kgroveshok/z80-homebrew/images/20220320_144750.jpg

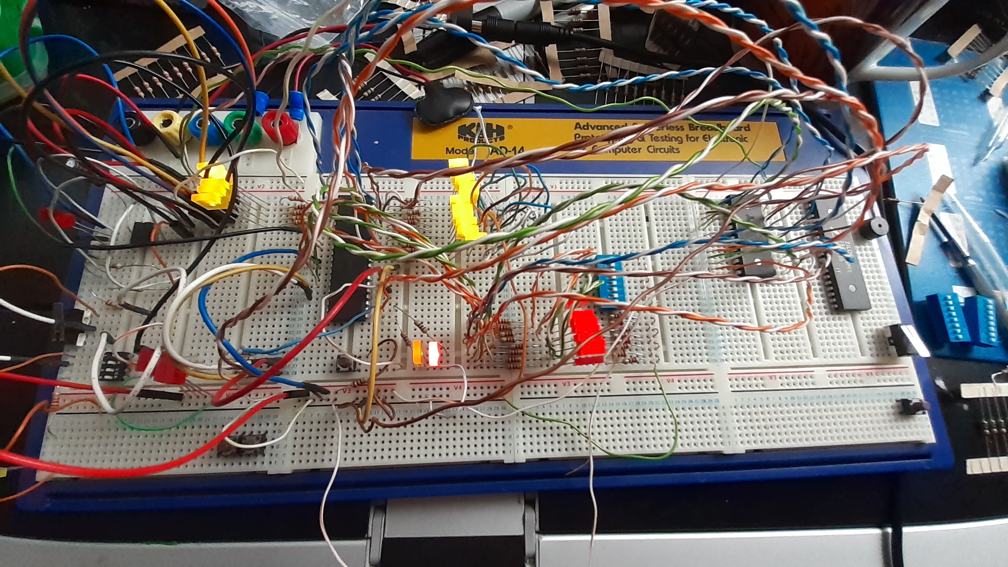
images/20220320_144750.jpg
