kgroveshok/z80-homebrew/images/20220322_210655.jpg

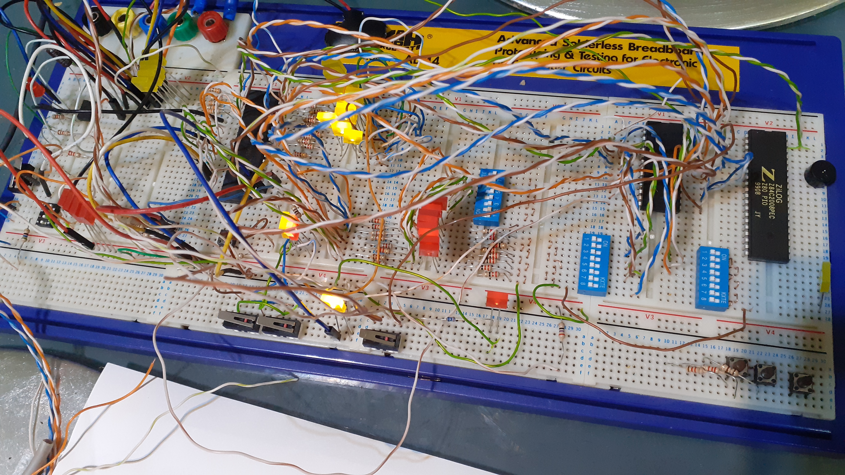
images/20220322_210655.jpg
