kgroveshok/z80-homebrew/Schematics/PCB_PCB_z80-spi-sound-cat5_2025-08-04.png

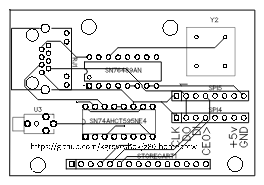
Schematics/PCB_PCB_z80-spi-sound-cat5_2025-08-04.png
