kgroveshok/z80-homebrew/Schematics/Schematic_PicoSPINet_2025-07-04.png

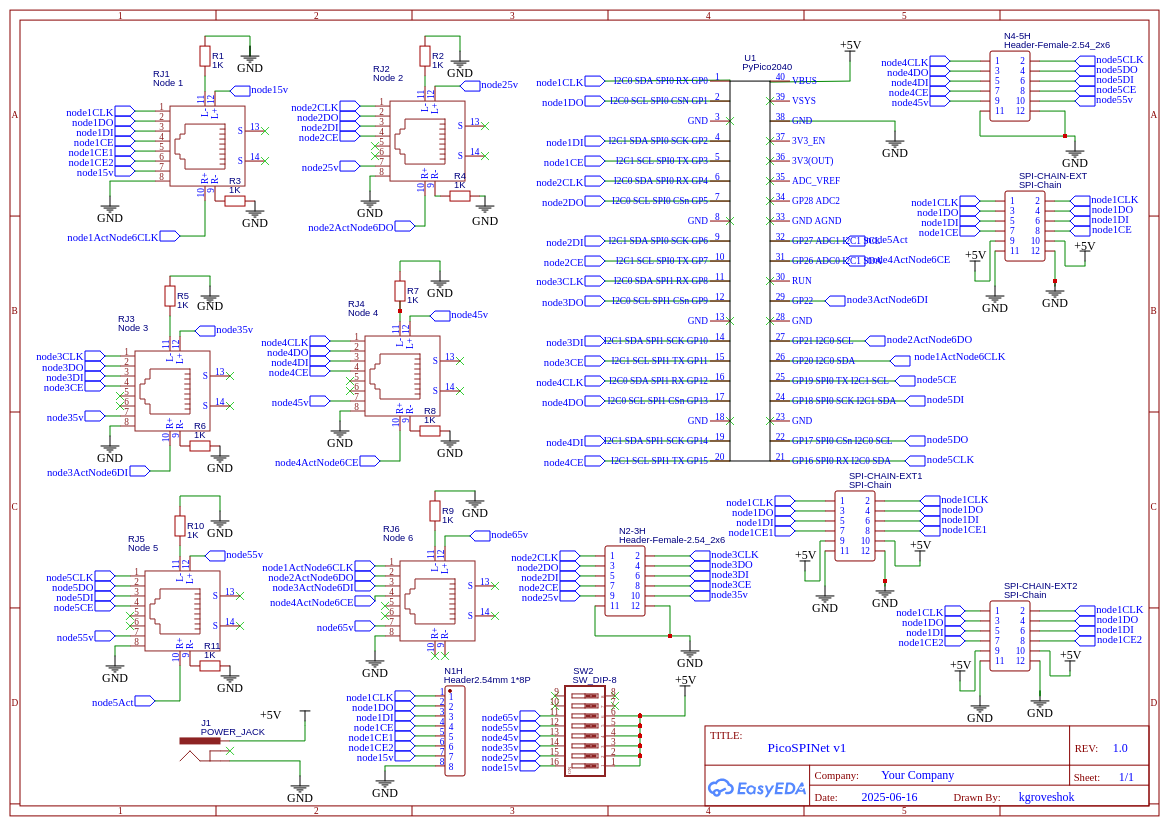
Schematics/Schematic_PicoSPINet_2025-07-04.png
