kgroveshok/z80-homebrew/Schematics/Schematic_z80-spi-sound-cat5_2025-08-04.png

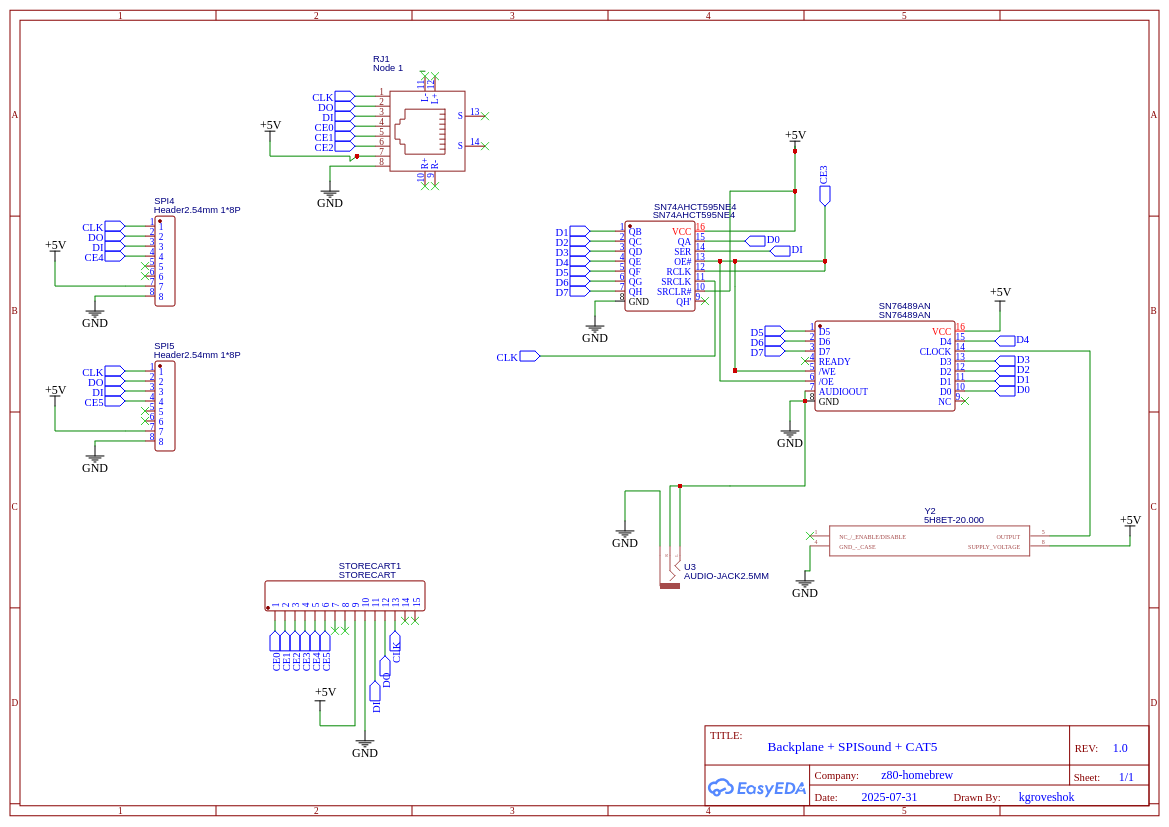
Schematics/Schematic_z80-spi-sound-cat5_2025-08-04.png
