kgroveshok/z80-homebrew/stage3.0/20230630_131646.jpg

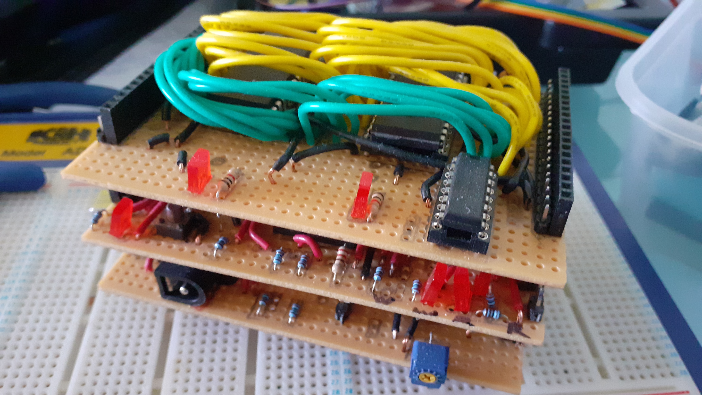
stage3.0/20230630_131646.jpg
