kgroveshok/z80-homebrew/stage3.0/20230630_132038.jpg

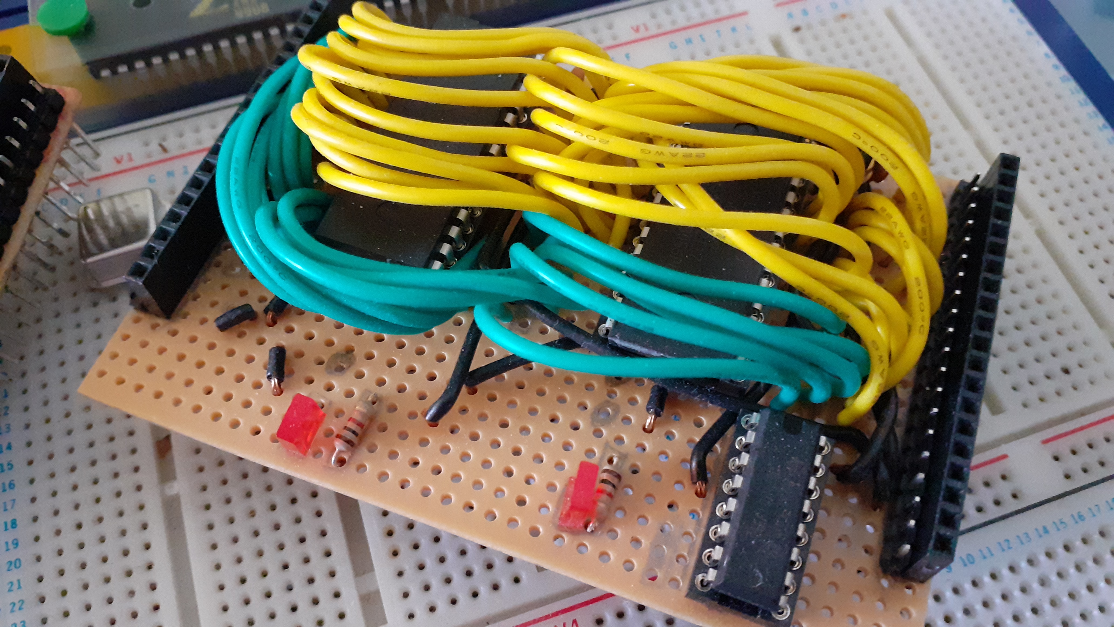
stage3.0/20230630_132038.jpg
