kgroveshok/z80-homebrew/stage3.0/20230630_132042.jpg

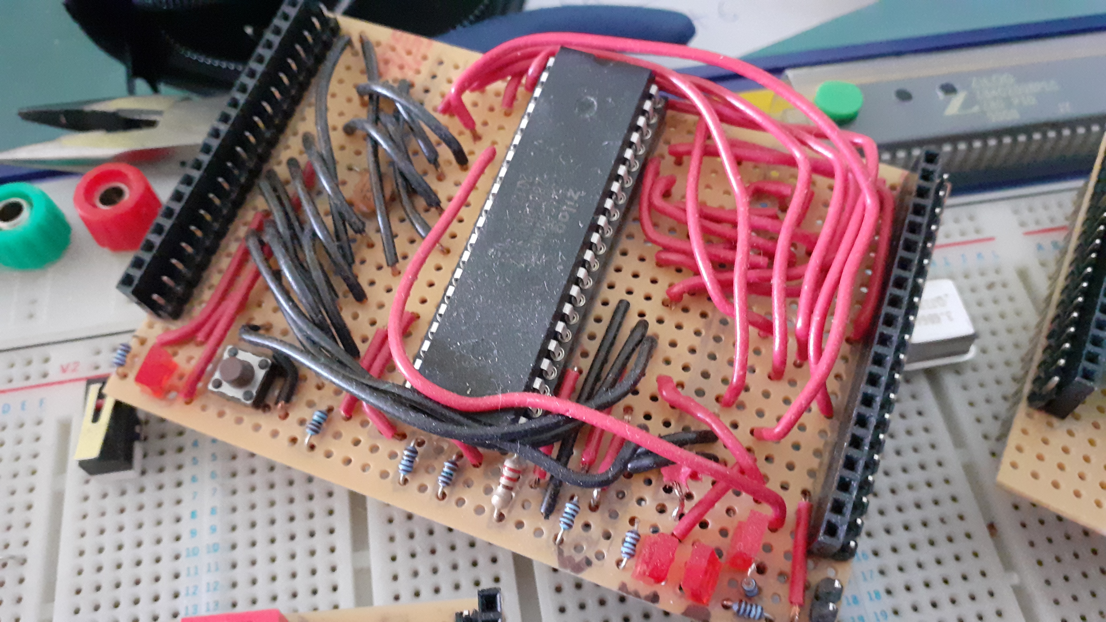
stage3.0/20230630_132042.jpg
