kgroveshok/z80-homebrew/stage3.0/20230711_081456.jpg

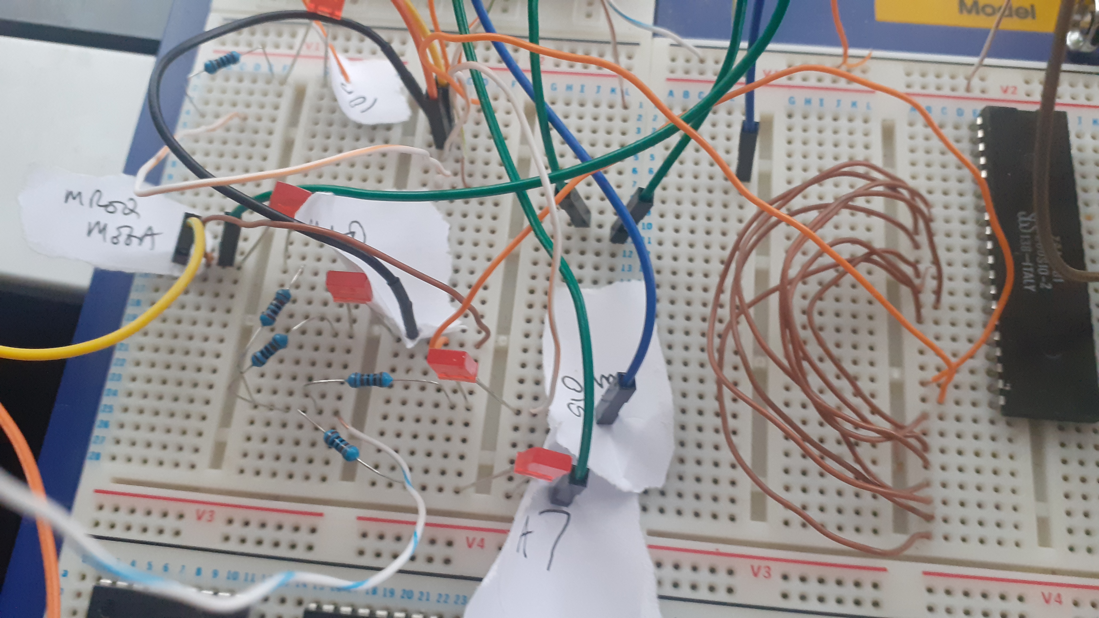
stage3.0/20230711_081456.jpg
