kgroveshok/z80-homebrew/stage3.0/20230711_081505.jpg

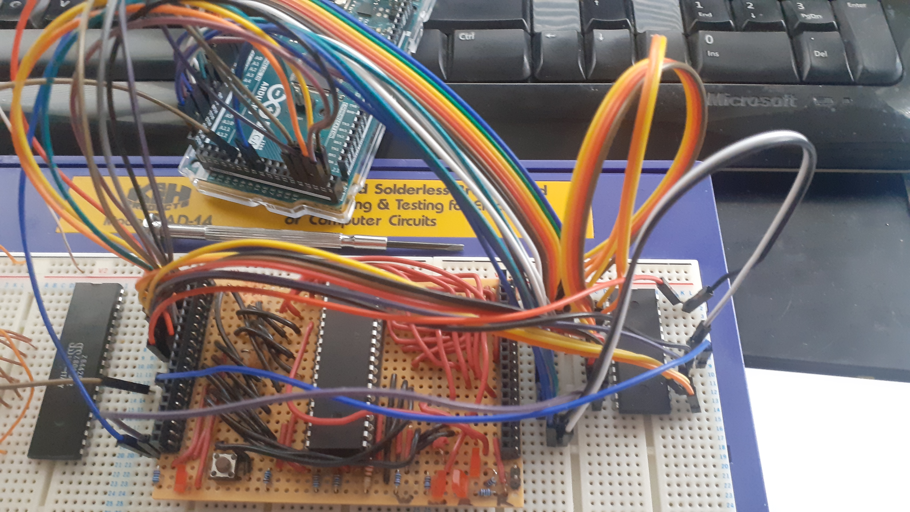
stage3.0/20230711_081505.jpg
