kgroveshok/z80-homebrew/stage3.0/20230711_175603.jpg

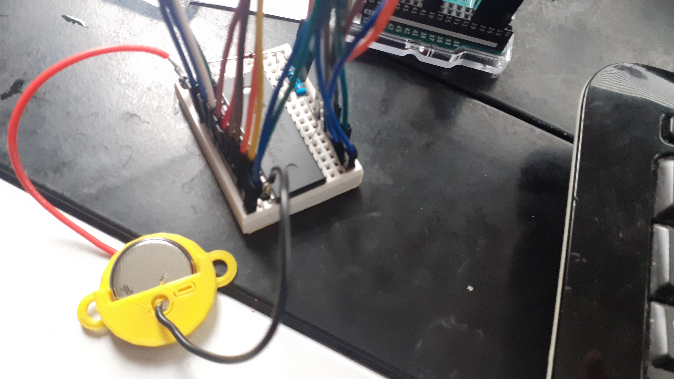
stage3.0/20230711_175603.jpg
