kgroveshok/z80-homebrew/stage3.0/addreslogic.png

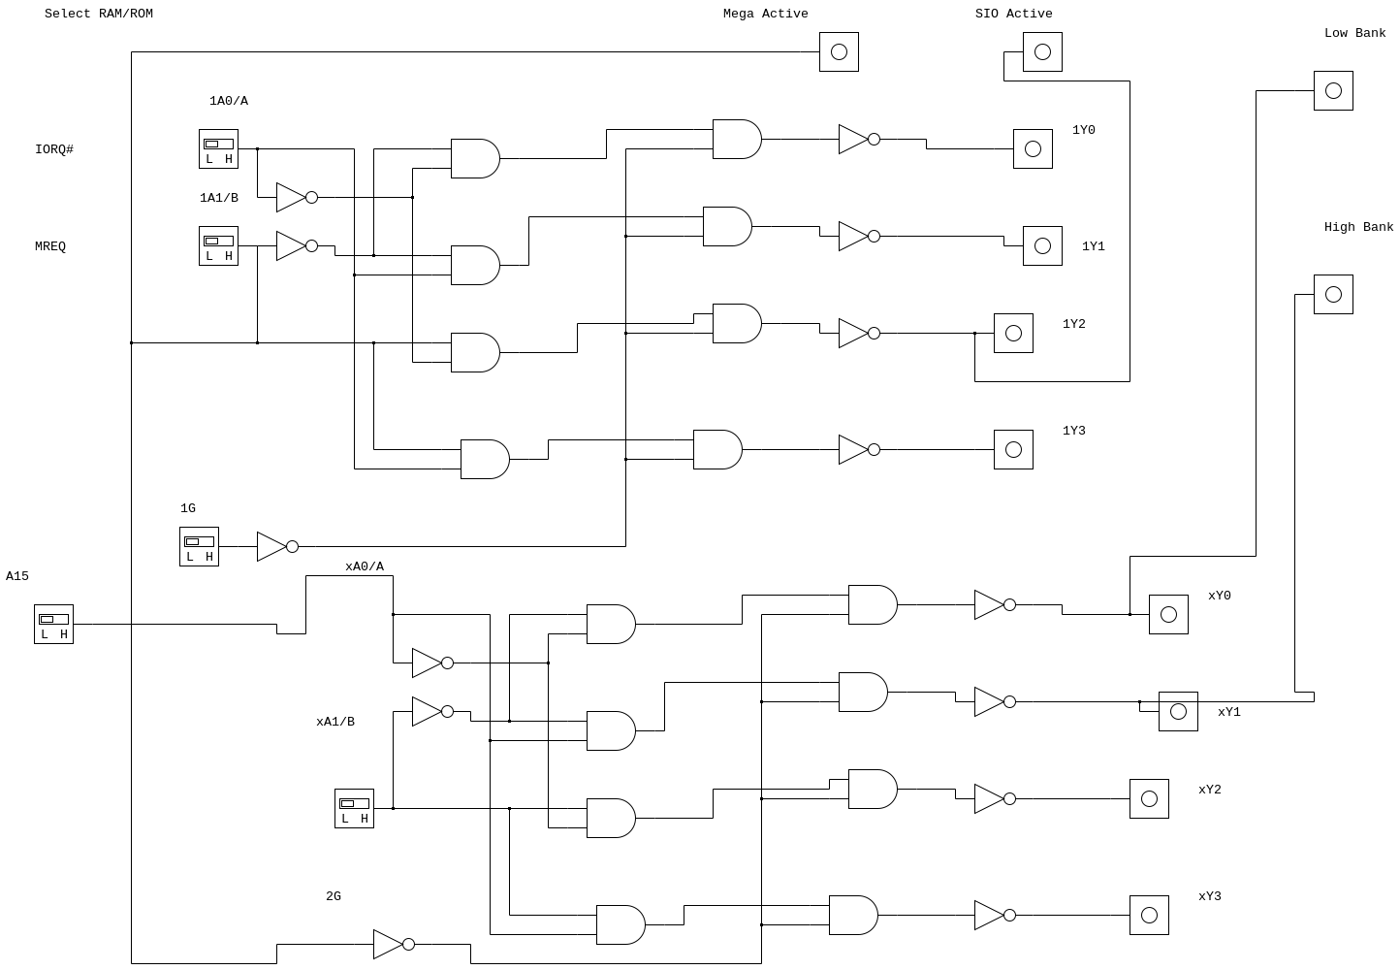
stage3.0/addreslogic.png
