kgroveshok/z80-homebrew/case/megav4.5-leftkeyboard.stl

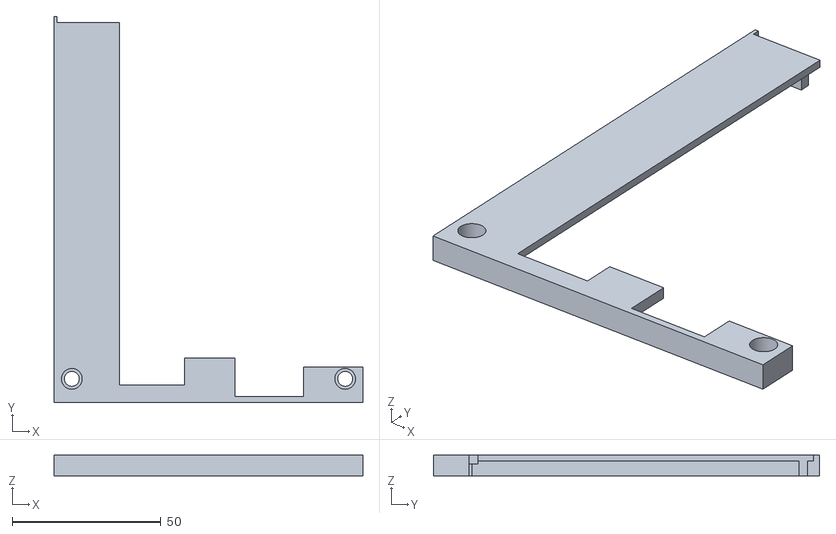
[picture p55: CAD file, 2026-07-11]
case/megav4.5-leftkeyboard.stl
104.0 x 130.0 x 7.00
