kgroveshok/z80-homebrew/case/megav4.5-pcbfoot.stl

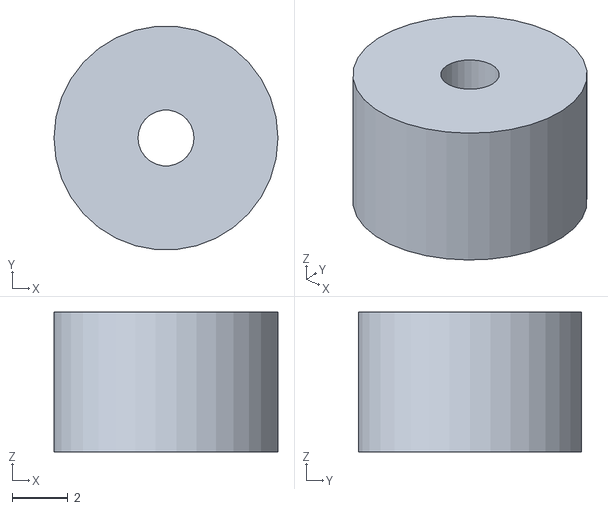
[picture p56: CAD file, 2026-07-11]
case/megav4.5-pcbfoot.stl
8.00 x 7.97 x 5.00
