kgroveshok/z80-homebrew/case/megav4.5-lid.stl

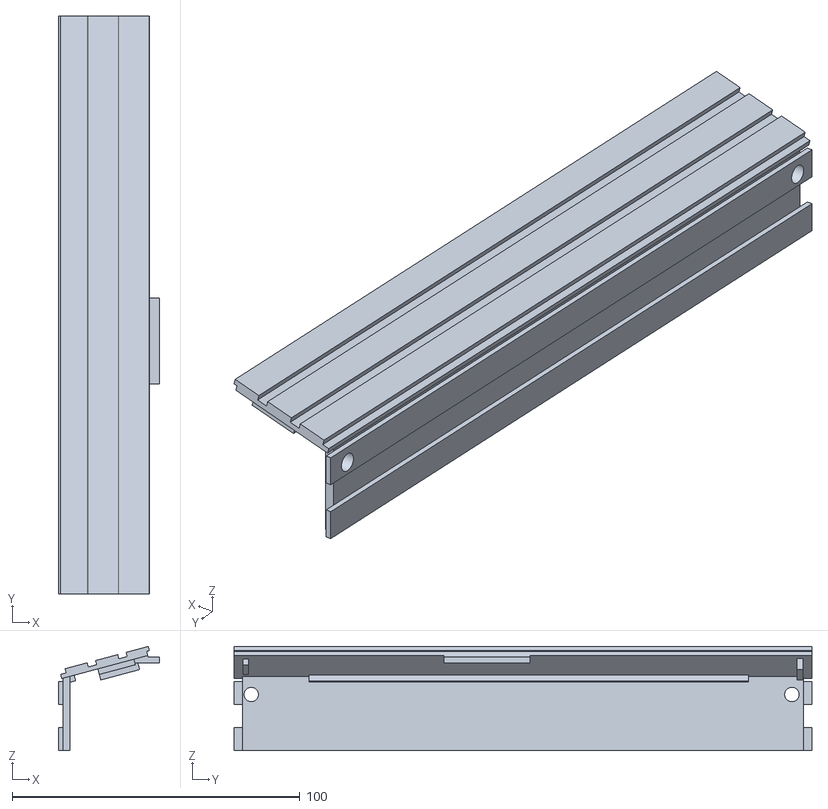
[picture p57: CAD file, 2026-06-28]
case/megav4.5-lid.stl
35.0 x 201.0 x 36.2
