kgroveshok/z80-homebrew/case/megav4.5-rightside.stl

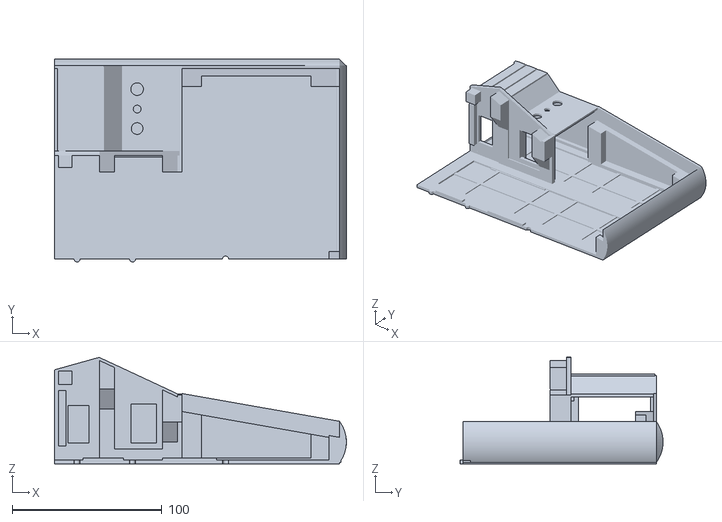
[picture p58: CAD file, 2026-06-28]
case/megav4.5-rightside.stl
194.7 x 135.4 x 71.0
