kgroveshok/z80-homebrew/case/megav2.FCStd

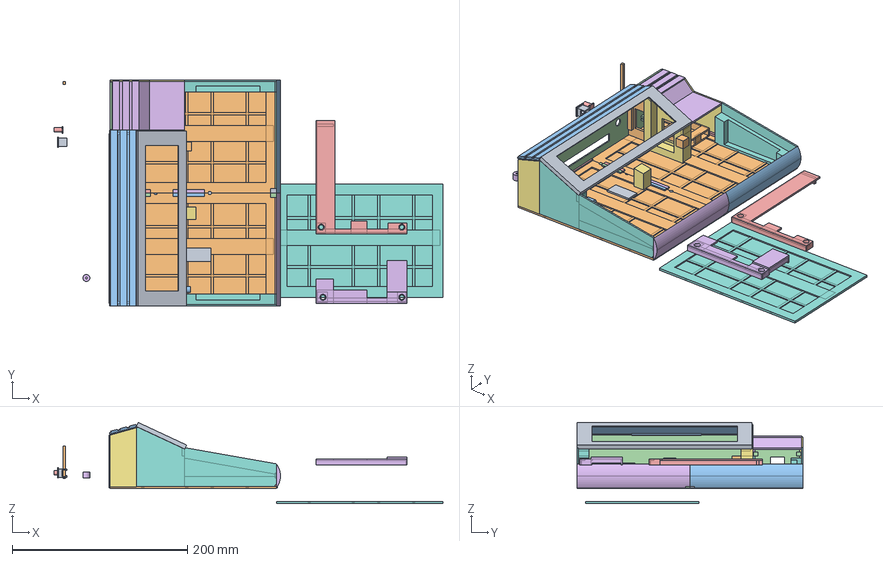
[picture p59: CAD file, 2025-09-19]
case/megav2.FCStd
444.0 x 258.0 x 92.5 mm
reset
pwrjack
PCBFoot
keyboardcentrepillar
RightPillar001
keyboardcentrepillar002
RightExtCartSlotWithHole
WristRest002
NewBasePanelSection
LinkPlate
BoxPanelSupports
LcdBezel
keyboardcentrepillar001
WristRest1
LeftExtCartSlot
keyboardlcdleftpillar
BoxLid
BoxPanelRight
LcdBezel001
LcdBezel002
batteryholder
