kgroveshok/z80-homebrew/case/megav2-NewLid.stl

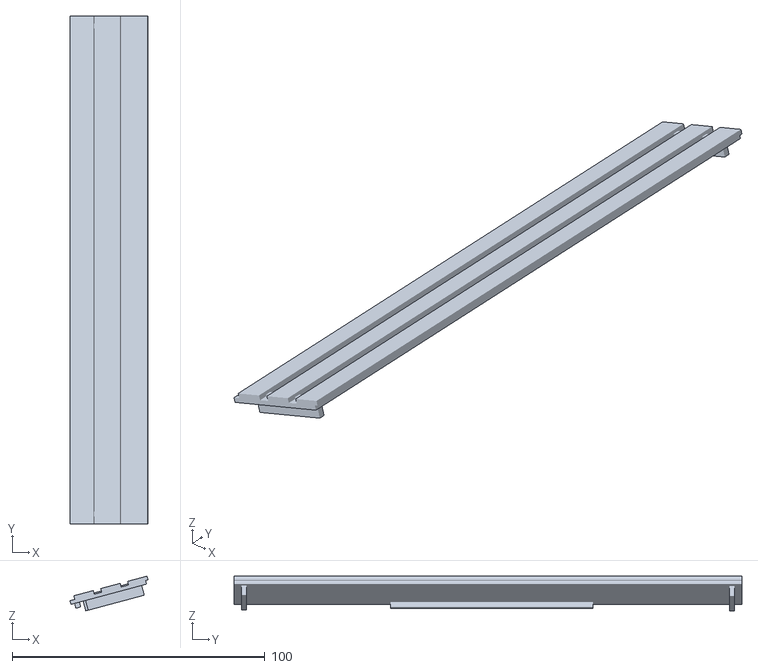
[picture p60: CAD file, 2025-04-25]
case/megav2-NewLid.stl
30.9 x 201.0 x 13.7
