kgroveshok/z80-homebrew/case/megav2-Back.stl

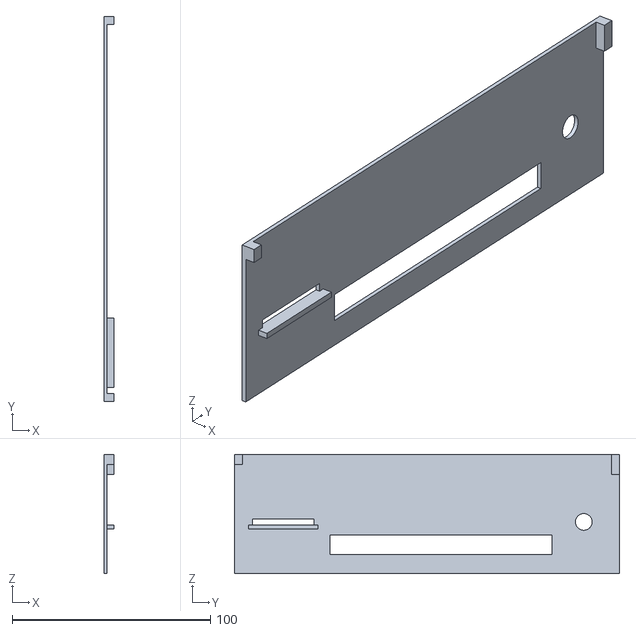
[picture p61: CAD file, 2025-03-21]
case/megav2-Back.stl
5.00 x 194.0 x 60.0
