kgroveshok/z80-homebrew/case/megav2-PowerBox.stl

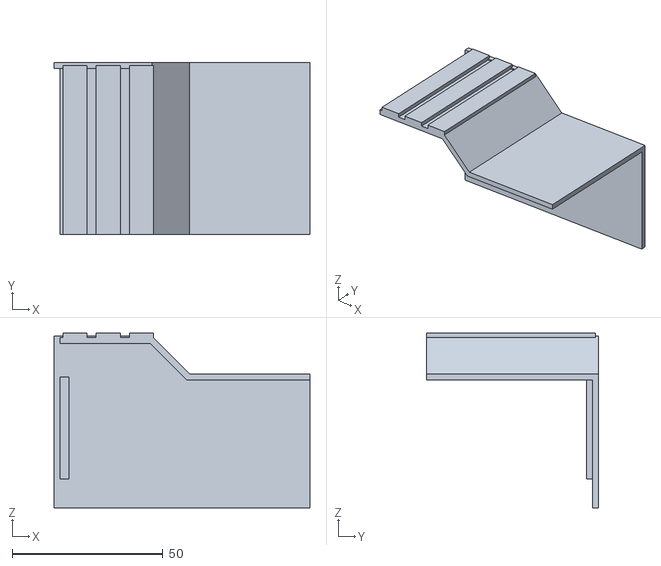
[picture p62: CAD file, 2025-03-20]
case/megav2-PowerBox.stl
85.0 x 57.0 x 58.0
