kgroveshok/z80-homebrew/case/megav2-RightSide.stl

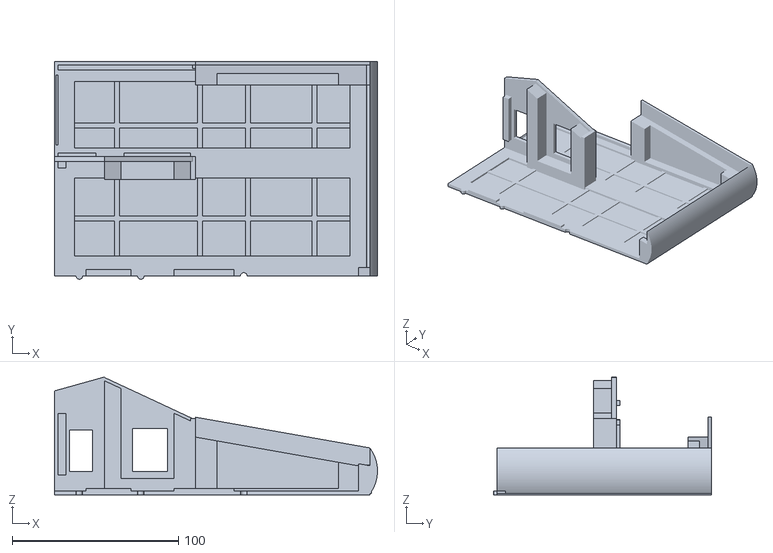
[picture p63: CAD file, 2025-03-20]
case/megav2-RightSide.stl
194.5 x 131.0 x 71.0
