kgroveshok/z80-homebrew/case/megav2-LeftSide.stl

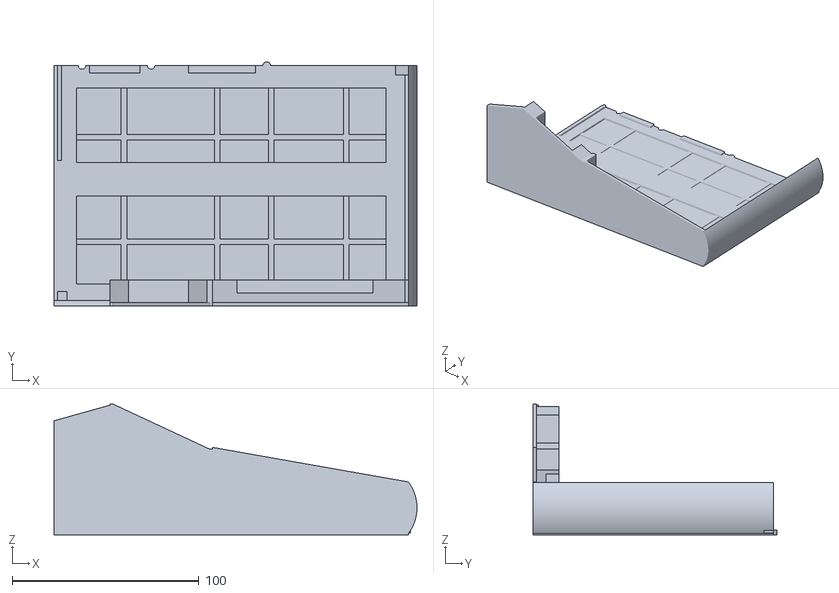
[picture p64: CAD file, 2025-03-20]
case/megav2-LeftSide.stl
194.5 x 131.0 x 70.0
