kgroveshok/z80-homebrew/case/megav4.5-batteryholder.stl

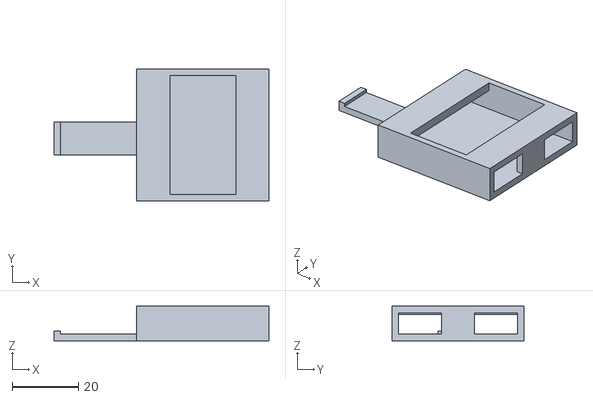
[picture p65: CAD file, 2025-03-20]
case/megav4.5-batteryholder.stl
65.0 x 40.0 x 10.5
