kgroveshok/z80-homebrew/case/megav2-Lid002.stl

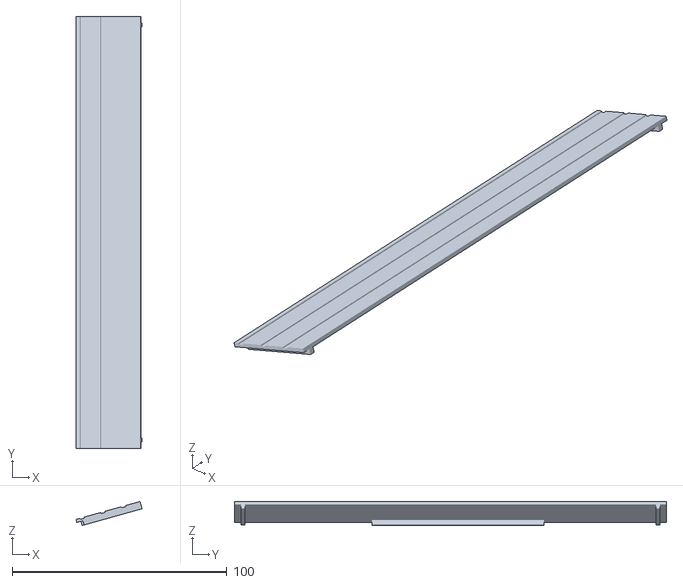
[picture p66: CAD file, 2025-03-14]
case/megav2-Lid002.stl
30.8 x 201.0 x 11.2
