kgroveshok/z80-homebrew/case/megav1.FCStd

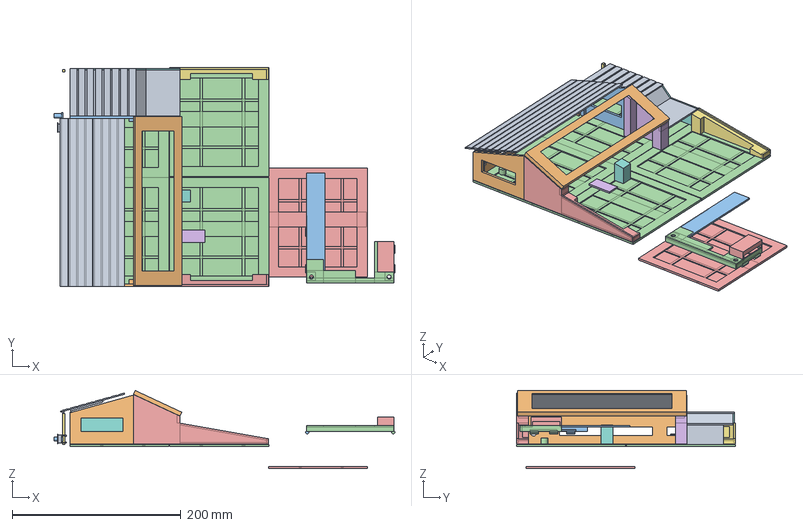
[picture p67: CAD file, 2024-06-13]
case/megav1.FCStd
404.0 x 259.0 x 92.5 mm
PCBFoot
keyboardlcdleftpillar
rightlcdpillar002
keyboardrightpillar
keyboardcentrepillar
Lid002
LeftExtCartSlotWithHole
RightExtCartSlotWithHole
NewBasePanelSection
LinkPlate
BoxPanelSupports
BoxPanelRight
BoxLid
LcdBezel
KeyboardBezelLeft
KeyboardBezelRight
