kgroveshok/z80-homebrew/case/megav1-LcdBezel.stl

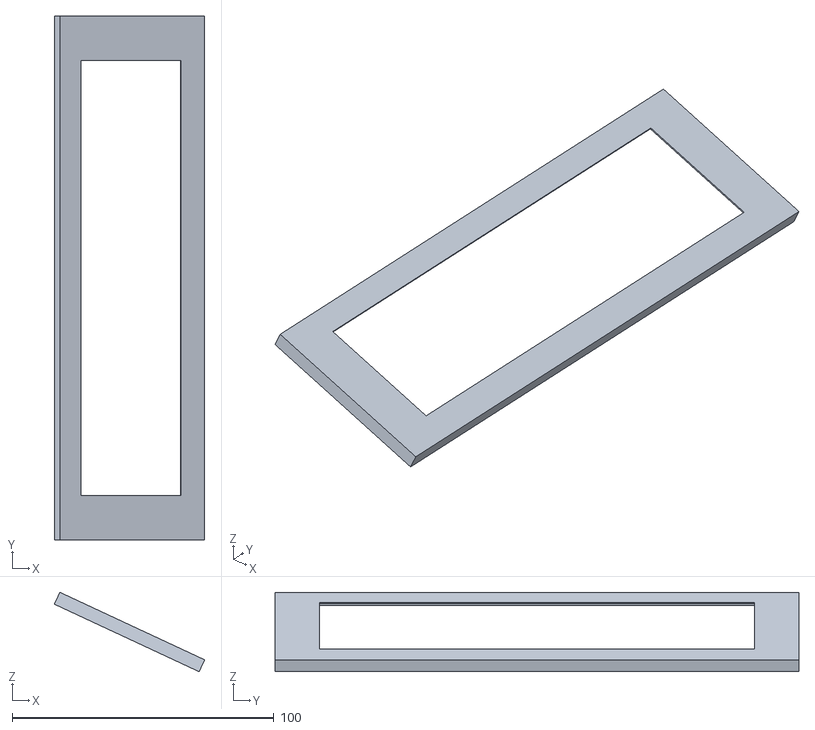
[picture p68: CAD file, 2024-06-13]
case/megav1-LcdBezel.stl
57.4 x 200.0 x 30.3
