kgroveshok/z80-homebrew/case/megav1-LinkPlate.stl

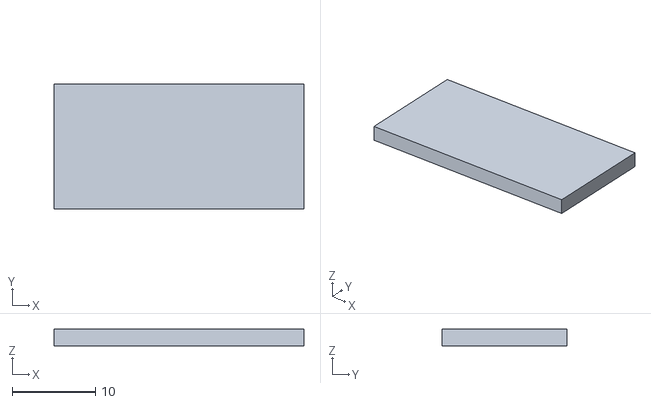
[picture p69: CAD file, 2024-06-11]
case/megav1-LinkPlate.stl
30.0 x 15.0 x 2.00
