kgroveshok/z80-homebrew/case/megav1-KeyboardBezelLeft.stl

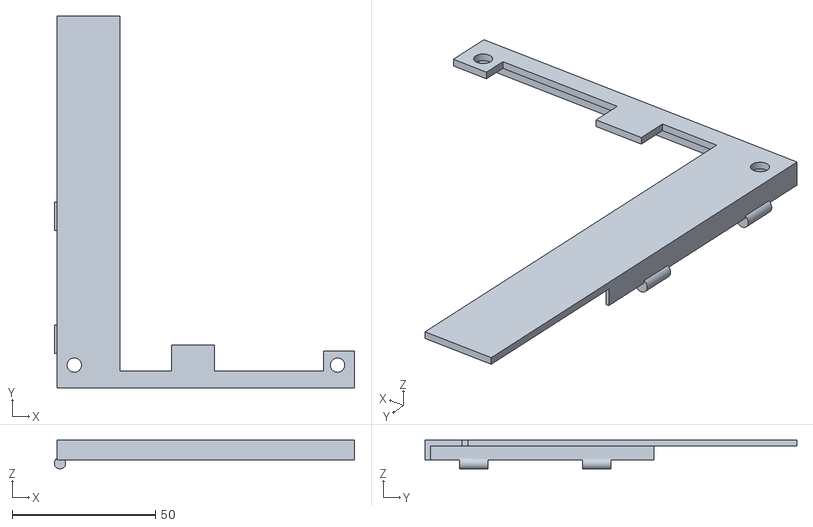
[picture p70: CAD file, 2024-06-11]
case/megav1-KeyboardBezelLeft.stl
105.0 x 130.0 x 10.00
