kgroveshok/z80-homebrew/case/megav1-KeyboardBezelRightBox.stl

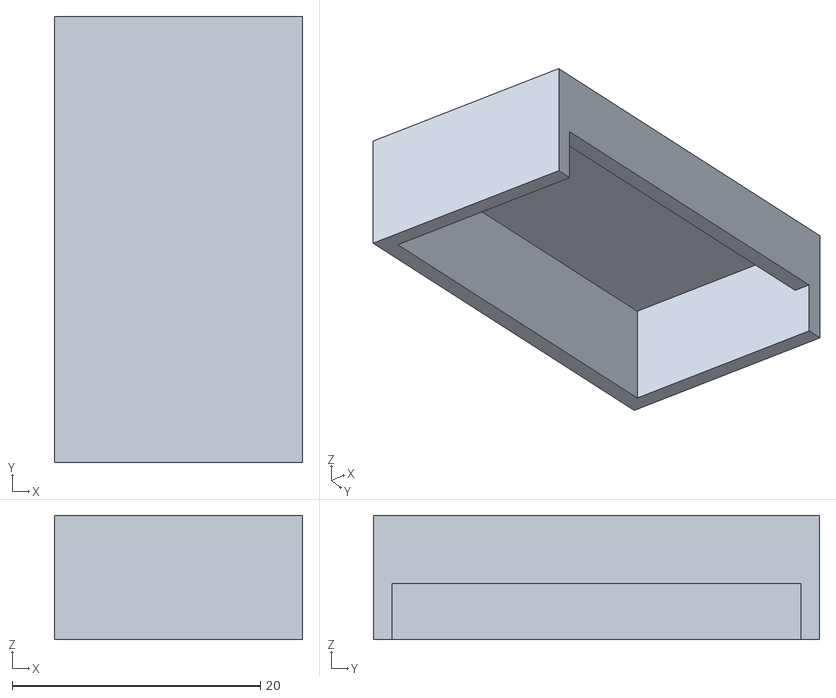
[picture p71: CAD file, 2024-06-11]
case/megav1-KeyboardBezelRightBox.stl
20.0 x 36.0 x 10.0
