kgroveshok/z80-homebrew/case/megav1-BoxPanelRight.stl

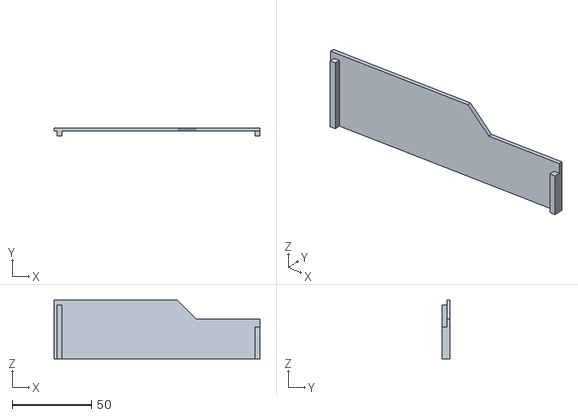
[picture p72: CAD file, 2024-06-11]
case/megav1-BoxPanelRight.stl
130.0 x 5.00 x 37.0
