kgroveshok/z80-homebrew/case/megav1-set1.3mf

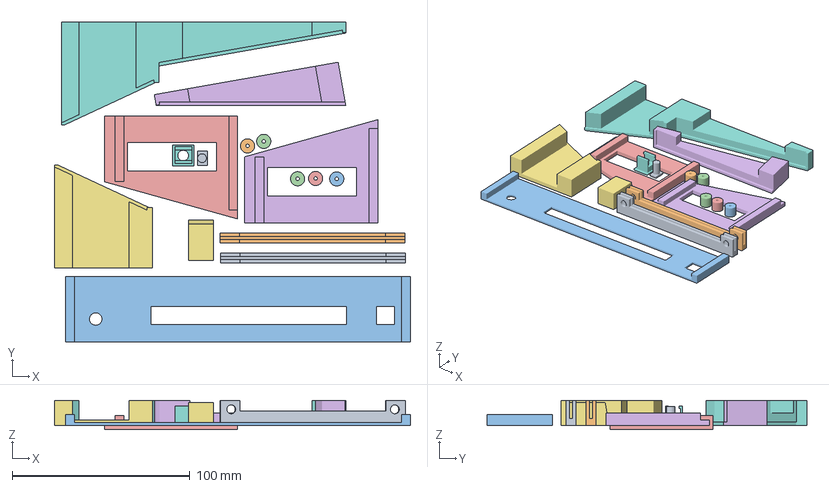
[picture p73: CAD file, 2024-06-11]
case/megav1-set1.3mf
200.2 x 180.1 x 16.3 mm
megav1-KeyBoardRiser.stl
megav1-KeyBoardRiser.stl(1)
megav1-Back.stl
megav1-PCBFoot.stl
megav1-LeftExtCartSlotWithHole.stl
megav1-RightExtCartSlotWithHole.stl
megav1-keyboardcentrepillar.stl
megav1-resetbutton-case.stl
megav1-resetbutton.stl
megav1-PCBFoot.stl(1)
megav1-PCBFoot.stl(2)
megav1-PCBFoot.stl(3)
megav1-PCBFoot.stl(4)
megav1-keyboardrightpillar.stl
megav1-rightlcdpillar002.stl
megav1-keyboardlcdleftpillar.stl
