kgroveshok/z80-homebrew/case/megav1-KeyboardBezelRight.stl

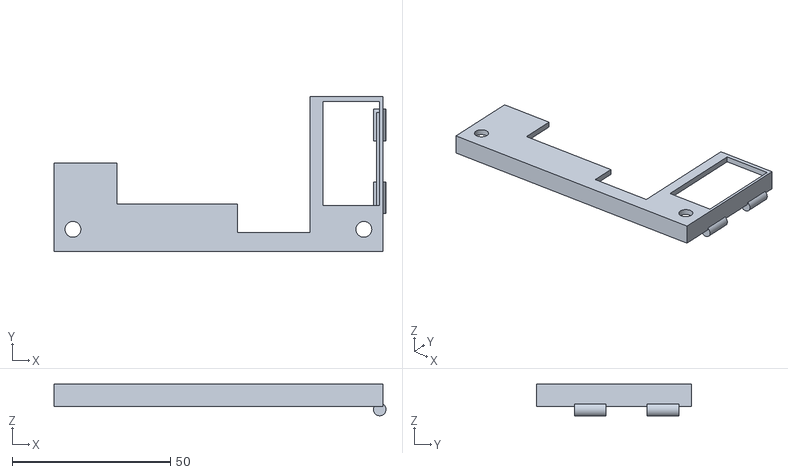
[picture p74: CAD file, 2024-06-11]
case/megav1-KeyboardBezelRight.stl
105.0 x 49.0 x 10.00
