kgroveshok/z80-homebrew/case/megav4.5-keyboardpillar.stl

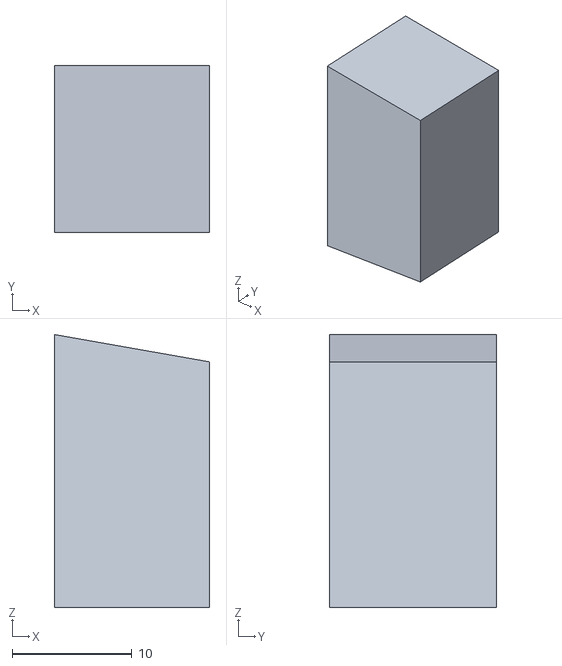
[picture p75: CAD file, 2024-06-11]
case/megav4.5-keyboardpillar.stl
13.0 x 14.0 x 22.8
