kgroveshok/z80-homebrew/case/megav1-BoxLid.stl

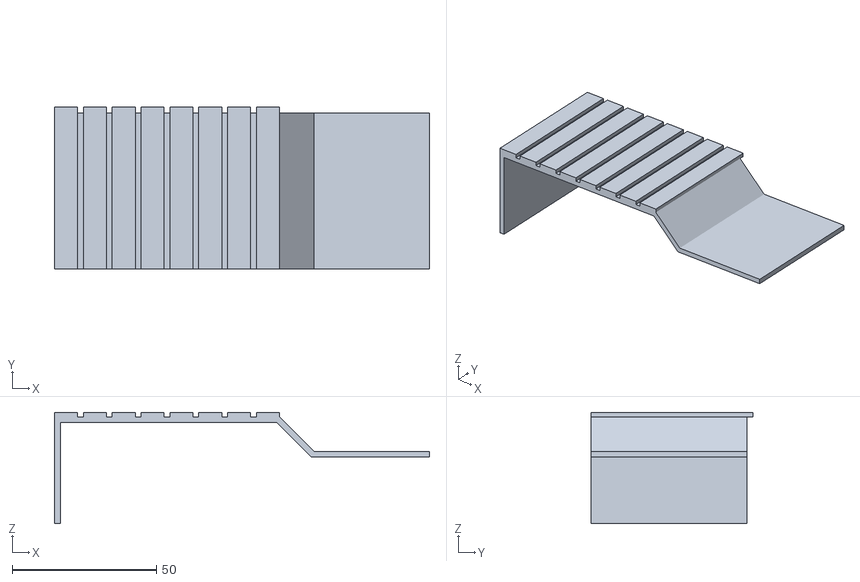
[picture p76: CAD file, 2024-06-11]
case/megav1-BoxLid.stl
130.0 x 56.0 x 38.5
