kgroveshok/z80-homebrew/case/megav1-rightlcdpillar002.stl

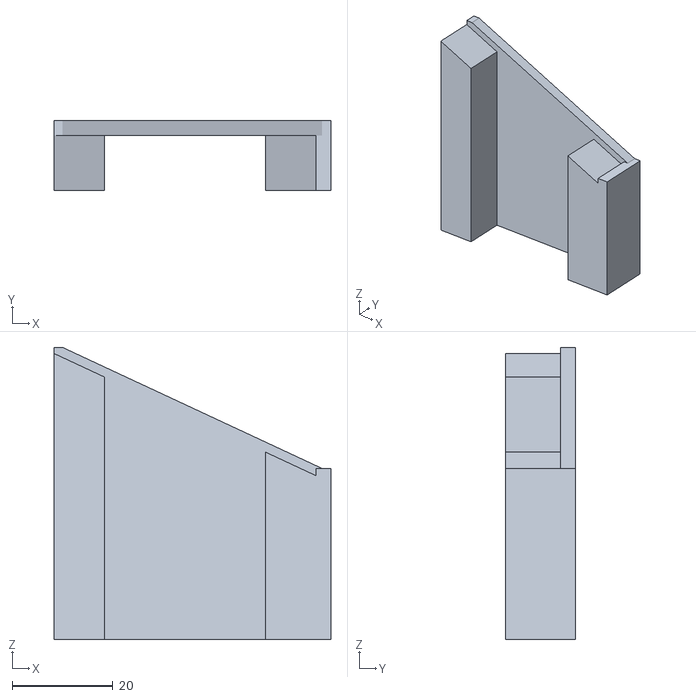
[picture p77: CAD file, 2024-06-11]
case/megav1-rightlcdpillar002.stl
55.0 x 14.0 x 58.0
