kgroveshok/z80-homebrew/case/megav1-NewBasePanelSection.stl

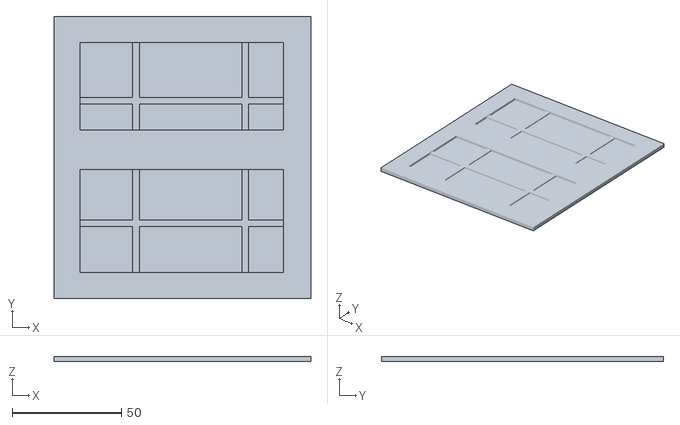
[picture p78: CAD file, 2024-06-09]
case/megav1-NewBasePanelSection.stl
117.5 x 129.0 x 2.50
