kgroveshok/z80-homebrew/case/megav1-keyboardlcdleftpillar.stl

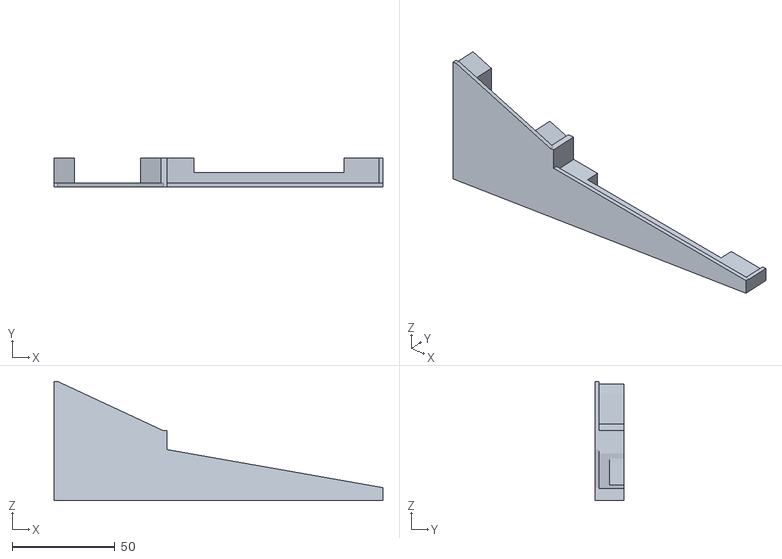
[picture p79: CAD file, 2024-06-09]
case/megav1-keyboardlcdleftpillar.stl
160.0 x 14.0 x 58.0
