kgroveshok/z80-homebrew/case/megav1-KeyBoardRiser.stl

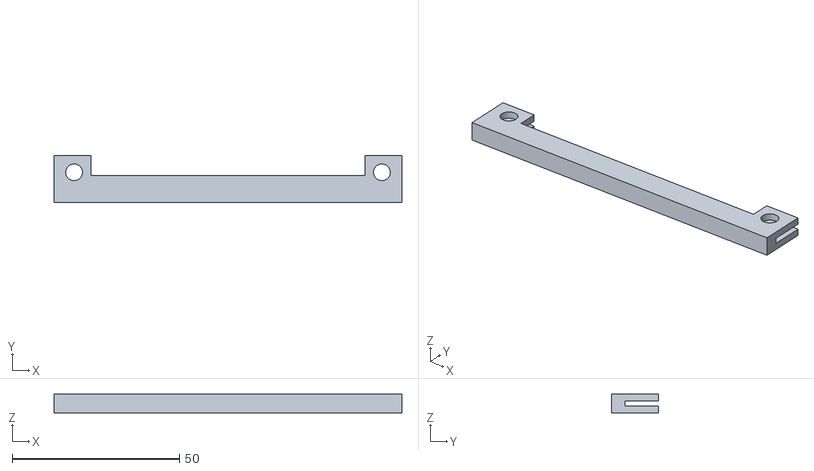
[picture p80: CAD file, 2024-06-09]
case/megav1-KeyBoardRiser.stl
104.0 x 14.0 x 5.60
