kgroveshok/z80-homebrew/case/megav1-PCBFoot.stl

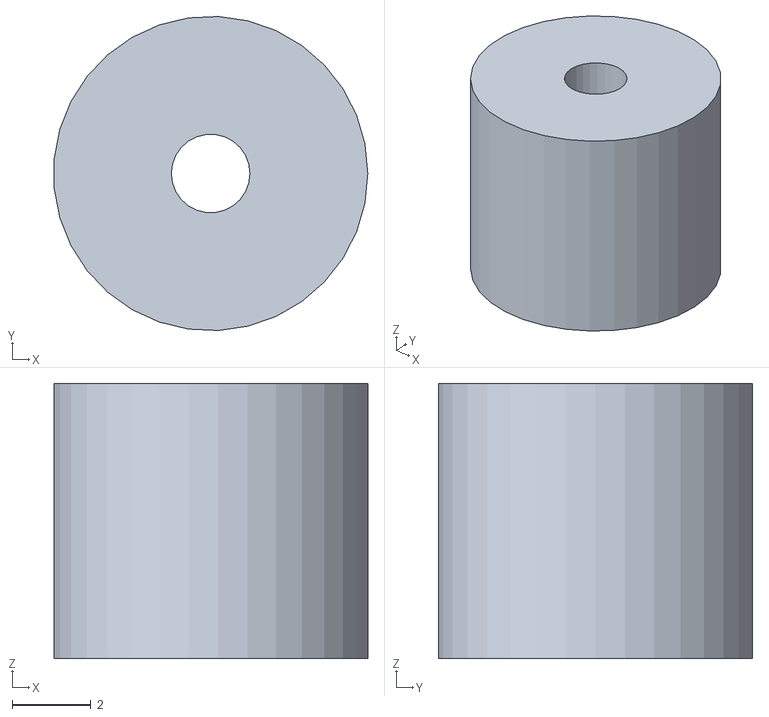
[picture p81: CAD file, 2024-06-08]
case/megav1-PCBFoot.stl
7.98 x 7.99 x 7.00
