kgroveshok/z80-homebrew/case/megav1-Lid002.stl

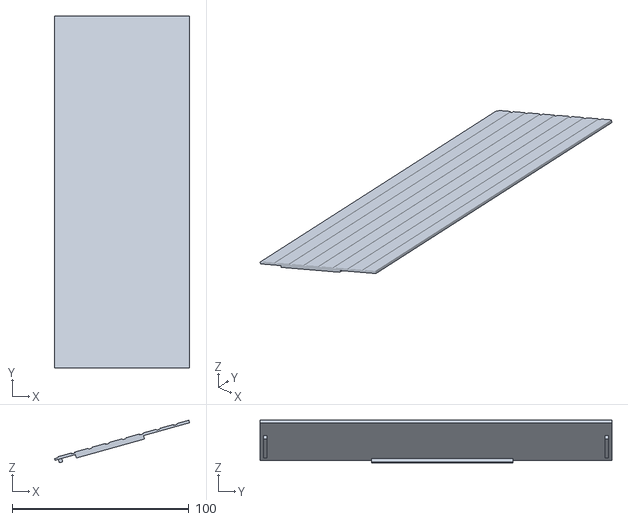
[picture p82: CAD file, 2024-06-07]
case/megav1-Lid002.stl
76.4 x 199.0 x 24.1
