kgroveshok/z80-homebrew/case/megav1-KeyboardRight.stl

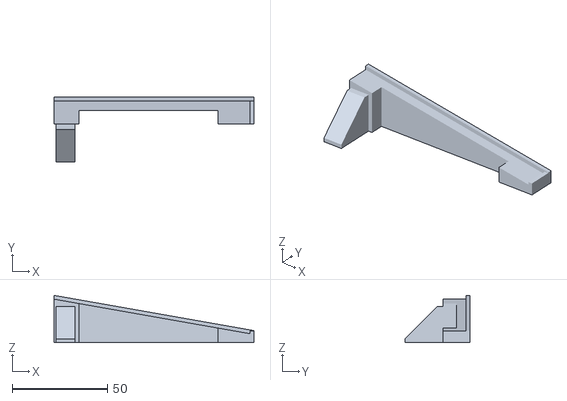
[picture p83: CAD file, 2024-06-07]
case/megav1-KeyboardRight.stl
105.0 x 34.0 x 24.8
