kgroveshok/z80-homebrew/case/megav1-keyboardrightpillar.stl

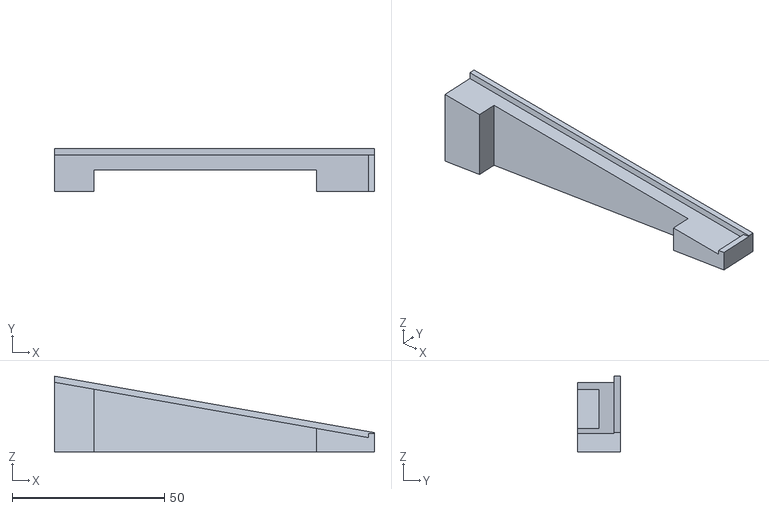
[picture p84: CAD file, 2024-06-07]
case/megav1-keyboardrightpillar.stl
105.0 x 14.0 x 24.8
