kgroveshok/z80-homebrew/case/megav1-lcdrightpillar.stl

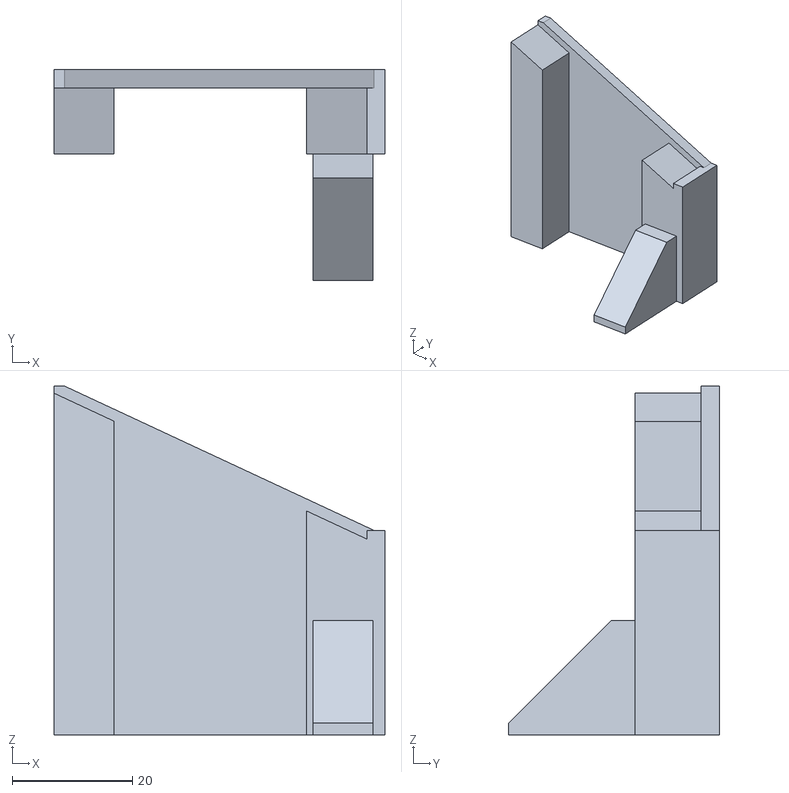
[picture p85: CAD file, 2024-06-07]
case/megav1-lcdrightpillar.stl
55.0 x 35.0 x 58.0
