kgroveshok/z80-homebrew/case/megav1-resetbutton-case.stl

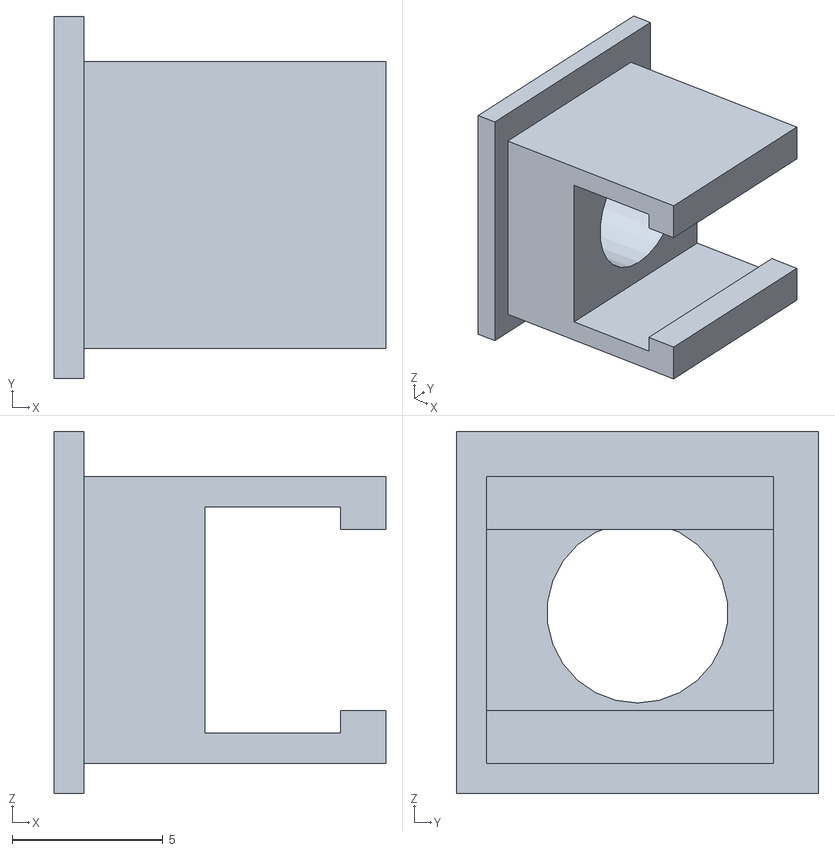
[picture p86: CAD file, 2024-06-07]
case/megav1-resetbutton-case.stl
11.0 x 12.0 x 12.0
