kgroveshok/z80-homebrew/case/megav1-LeftExtCartSlotWithHole.stl

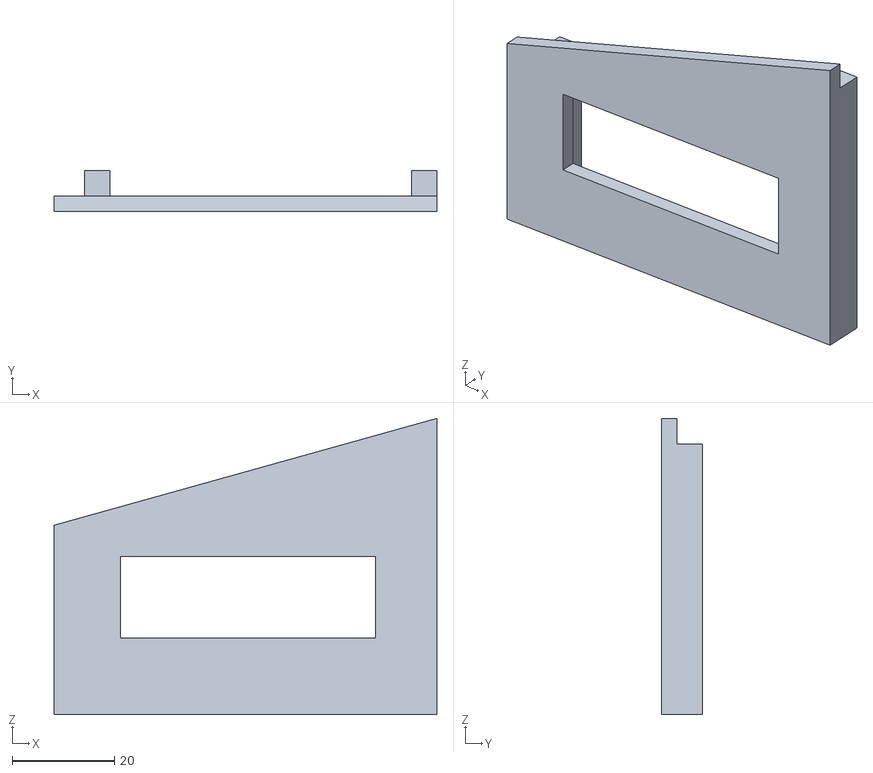
[picture p87: CAD file, 2024-06-07]
case/megav1-LeftExtCartSlotWithHole.stl
75.0 x 8.00 x 58.0
