kgroveshok/z80-homebrew/case/megav1-RightExtCartSlotWithHole.stl

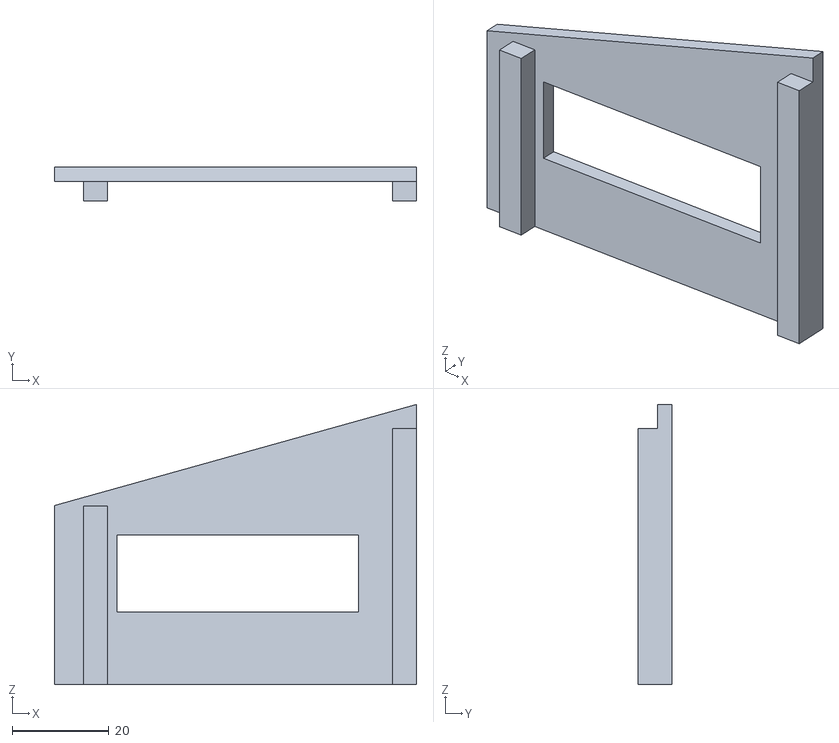
[picture p88: CAD file, 2024-06-07]
case/megav1-RightExtCartSlotWithHole.stl
75.0 x 7.00 x 58.0
