kgroveshok/z80-homebrew/case/megav1-Back.stl

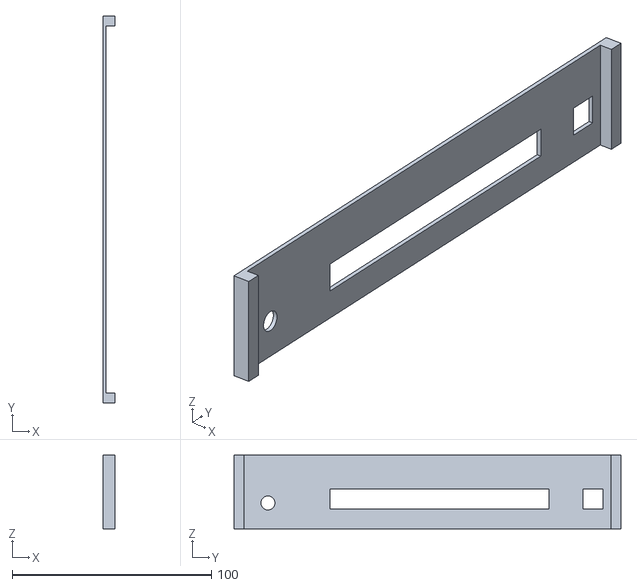
[picture p89: CAD file, 2024-06-07]
case/megav1-Back.stl
6.00 x 194.0 x 37.0
