kgroveshok/z80-homebrew/case/megav1-resetbutton.stl

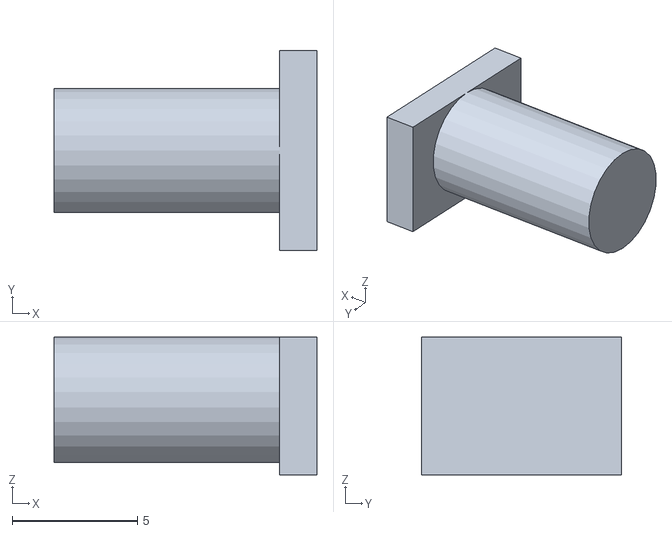
[picture p90: CAD file, 2024-06-07]
case/megav1-resetbutton.stl
10.5 x 8.00 x 5.50
