kgroveshok/z80-homebrew/case/case4.FCStd

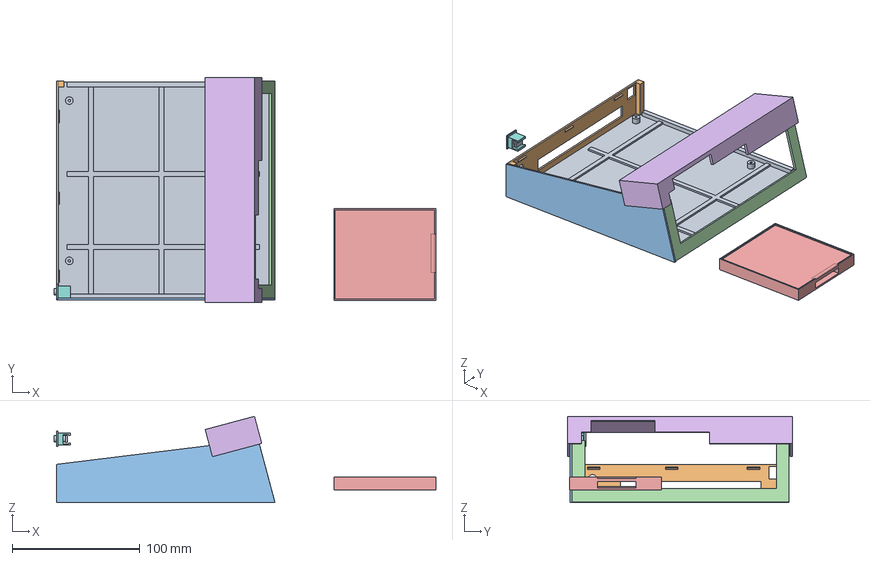
[picture p91: CAD file, 2024-06-06]
case/case4.FCStd
299.0 x 176.0 x 67.6 mm
sidewall
