kgroveshok/z80-homebrew/case/case2.FCStd

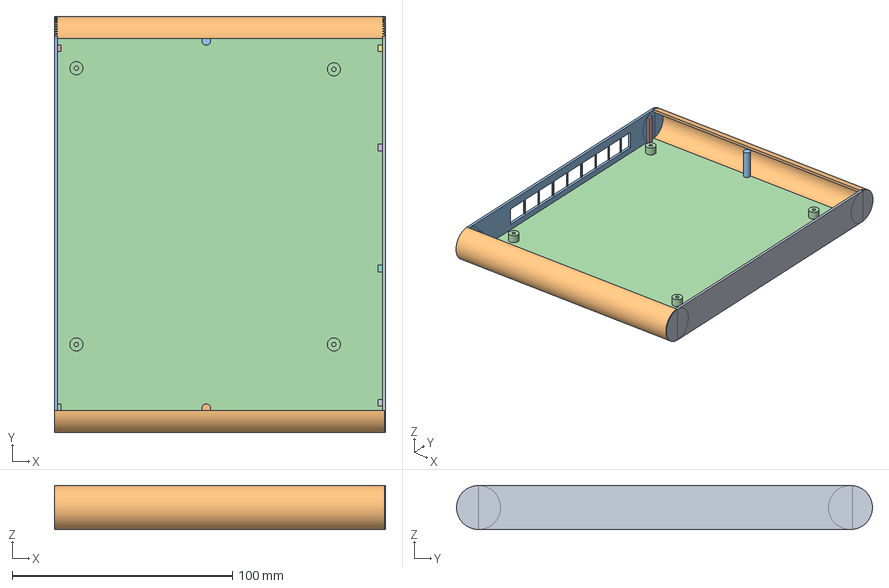
[picture p92: CAD file, 2024-05-09]
case/case2.FCStd
150.5 x 189.0 x 20.0 mm
Front
