kgroveshok/z80-homebrew/case/case3.FCStd

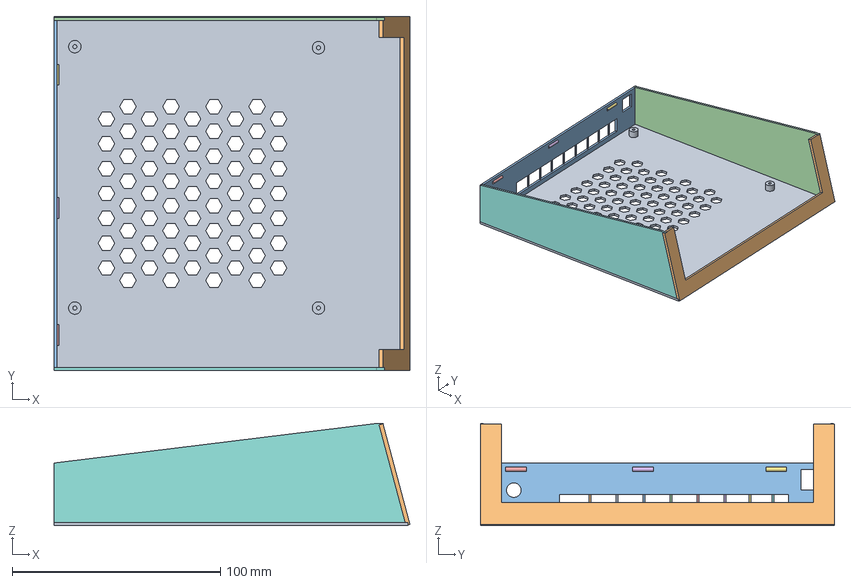
[picture p93: CAD file, 2024-05-09]
case/case3.FCStd
170.9 x 170.0 x 49.0 mm
sidewall001
sidewall
