kgroveshok/z80-homebrew/case/case1.FCStd

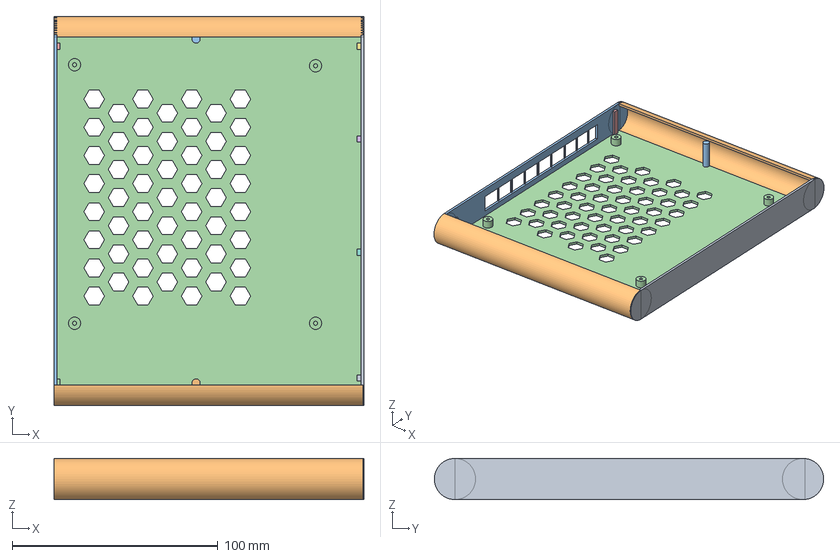
[picture p94: CAD file, 2024-05-09]
case/case1.FCStd
150.5 x 189.0 x 20.0 mm
Front
