kgroveshok/z80-homebrew/case/case4-Side1.stl

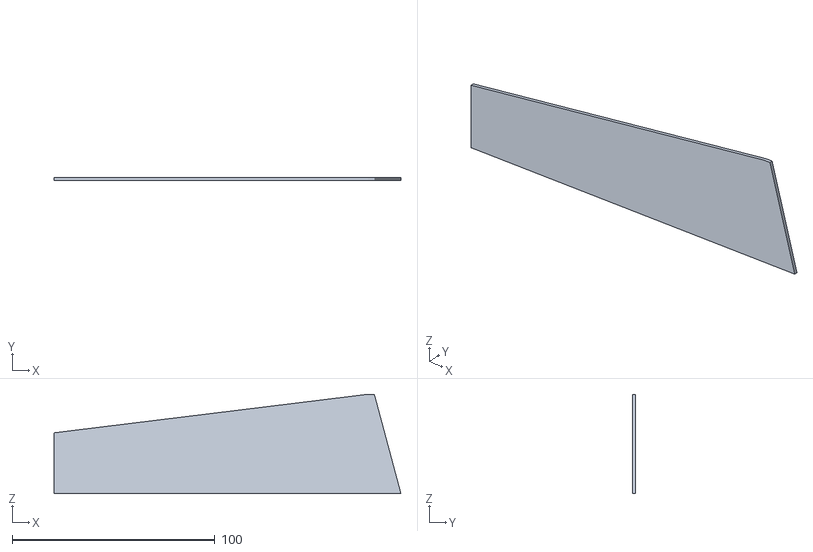
[picture p96: CAD file, 2024-05-09]
case/case4-Side1.stl
171.0 x 1.50 x 49.0
