kgroveshok/z80-homebrew/case/case1-Front.stl

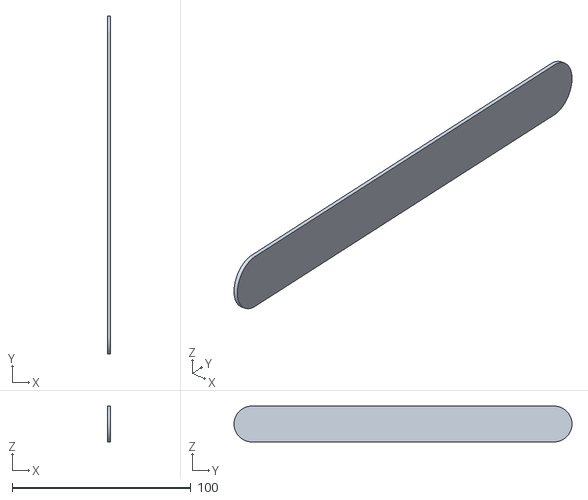
[picture p97: CAD file, 2024-05-09]
case/case1-Front.stl
1.50 x 189.0 x 20.0
