kgroveshok/z80-homebrew/case/case1-Fusion004solid.stl

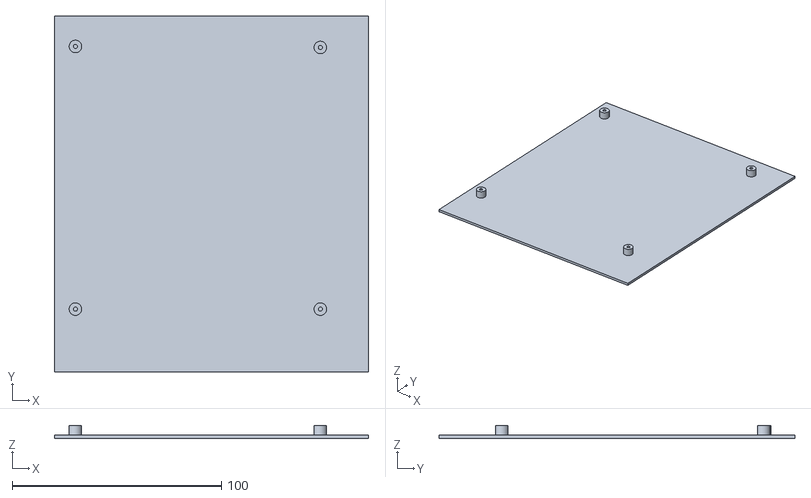
[picture p98: CAD file, 2024-05-09]
case/case1-Fusion004solid.stl
150.0 x 170.0 x 6.00
