kgroveshok/z80-homebrew/case/case4-keypad.stl

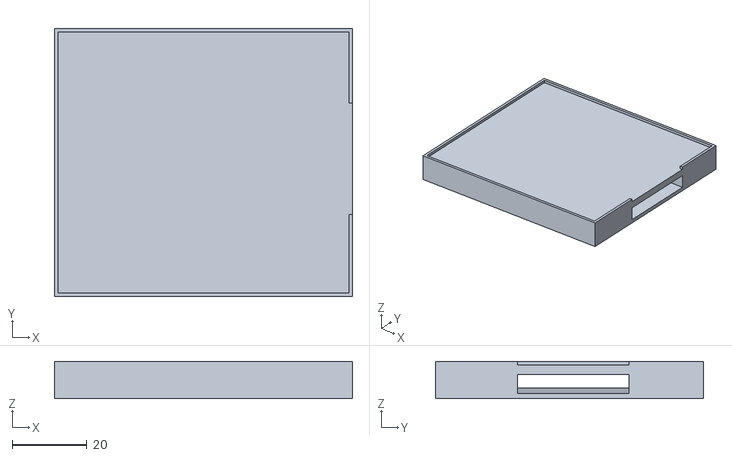
[picture p99: CAD file, 2024-05-09]
case/case4-keypad.stl
80.0 x 72.0 x 10.0
