kgroveshok/z80-homebrew/case/case1-Case.step

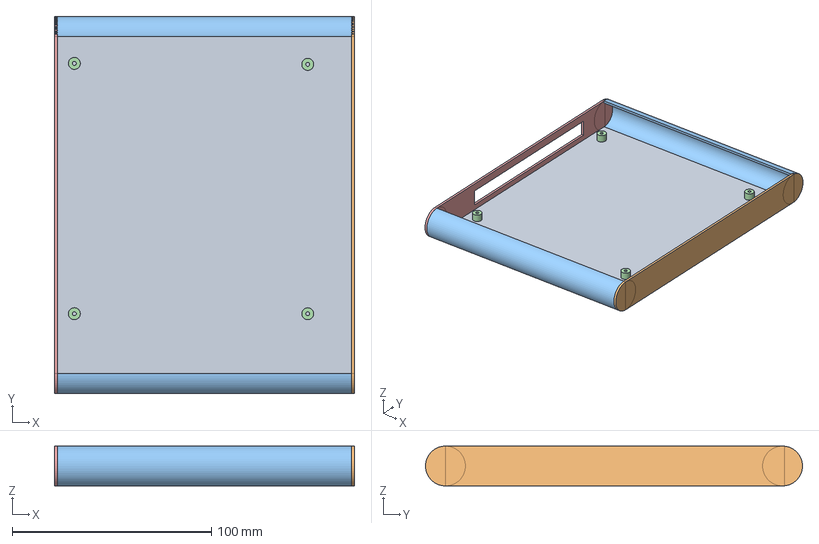
[picture p100: CAD file, 2024-05-09]
case/case1-Case.step
150.5 x 189.0 x 20.0 mm
base
Front
