kgroveshok/z80-homebrew/case/case4-CaseBase.stl

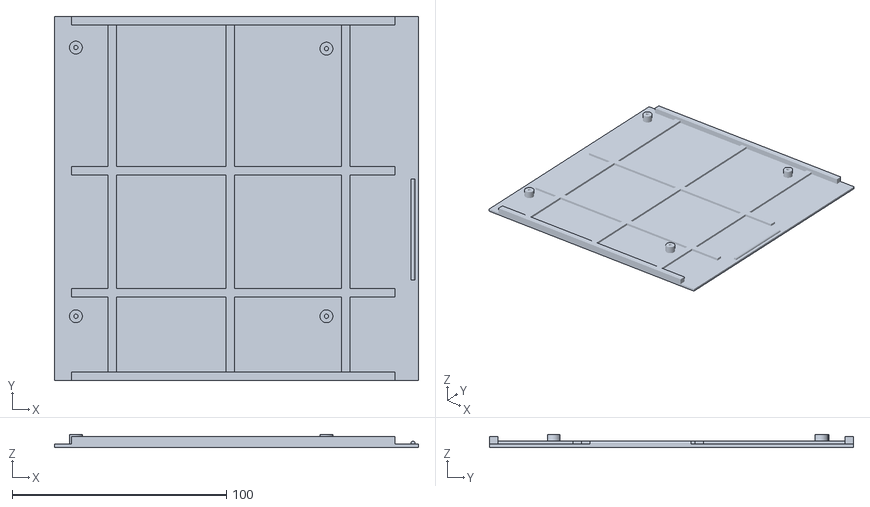
[picture p101: CAD file, 2024-05-09]
case/case4-CaseBase.stl
170.0 x 170.0 x 6.00
