kgroveshok/z80-homebrew/case/case4-Back.stl

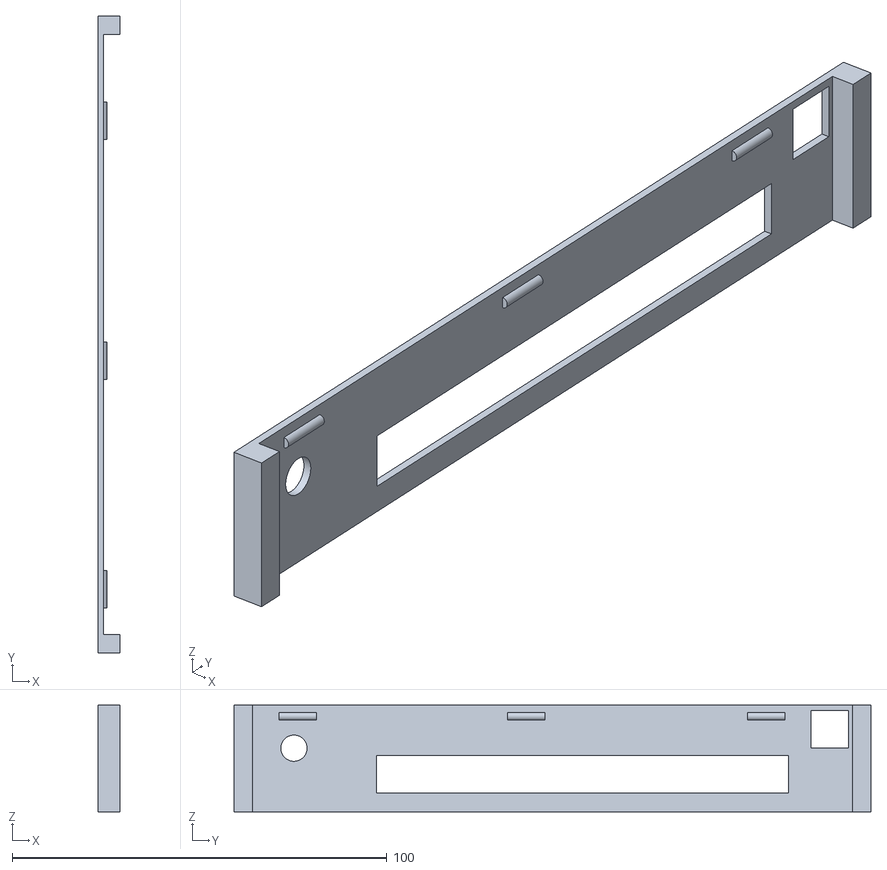
[picture p102: CAD file, 2024-05-09]
case/case4-Back.stl
6.00 x 170.0 x 28.5
