kgroveshok/z80-homebrew/case/case4-Front.stl

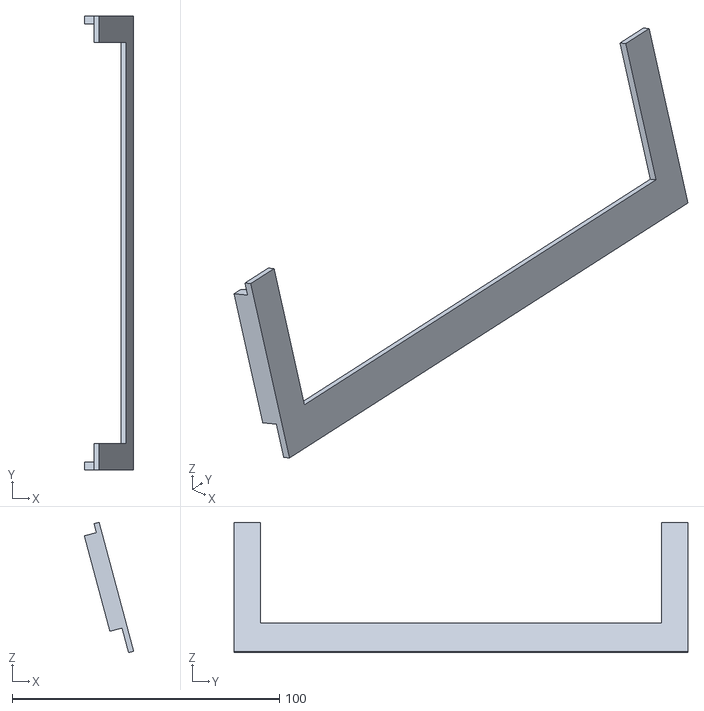
[picture p103: CAD file, 2024-05-09]
case/case4-Front.stl
18.5 x 170.0 x 48.8
