kgroveshok/z80-homebrew/case/case3-CaseBase-nogrill.stl

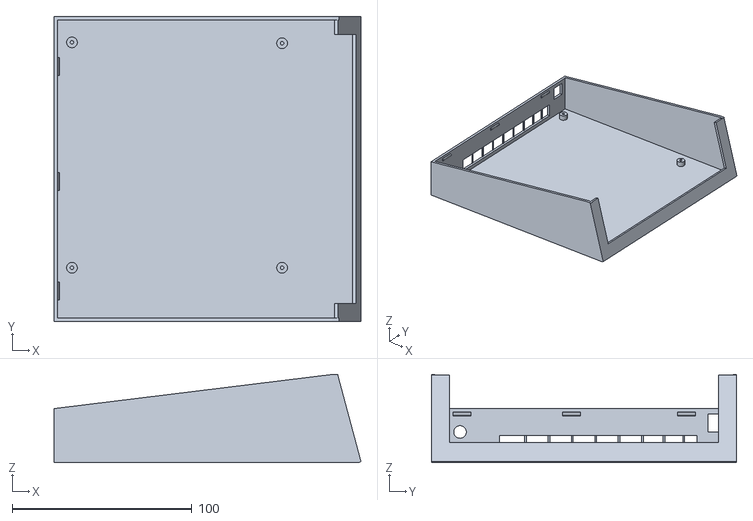
[picture p104: CAD file, 2024-05-09]
case/case3-CaseBase-nogrill.stl
170.9 x 170.0 x 49.0
