kgroveshok/z80-homebrew/case/case4-LCDCap.stl

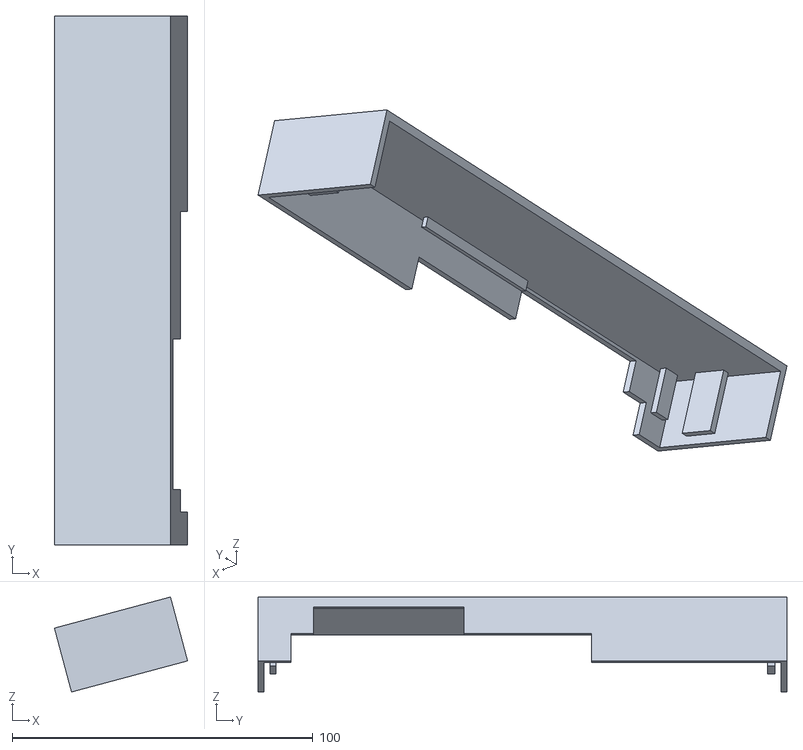
[picture p105: CAD file, 2024-05-09]
case/case4-LCDCap.stl
44.3 x 176.0 x 31.6
