kgroveshok/z80-homebrew/case/case1-Cut003.stl

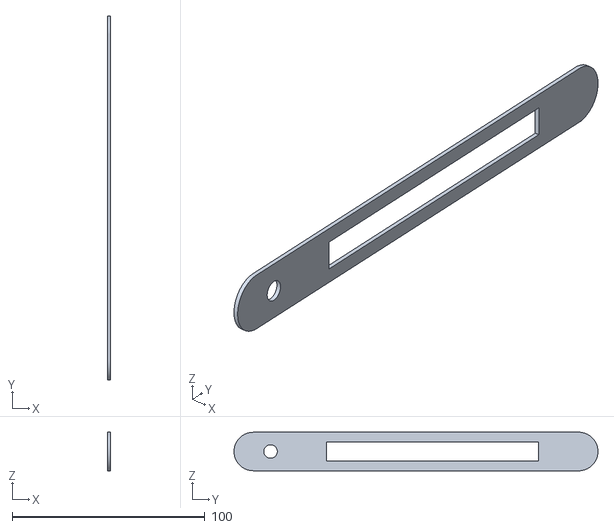
[picture p106: CAD file, 2024-05-09]
case/case1-Cut003.stl
1.50 x 189.0 x 20.0
