kgroveshok/z80-homebrew/stage2.0/Front-Panel-Layer.pdf

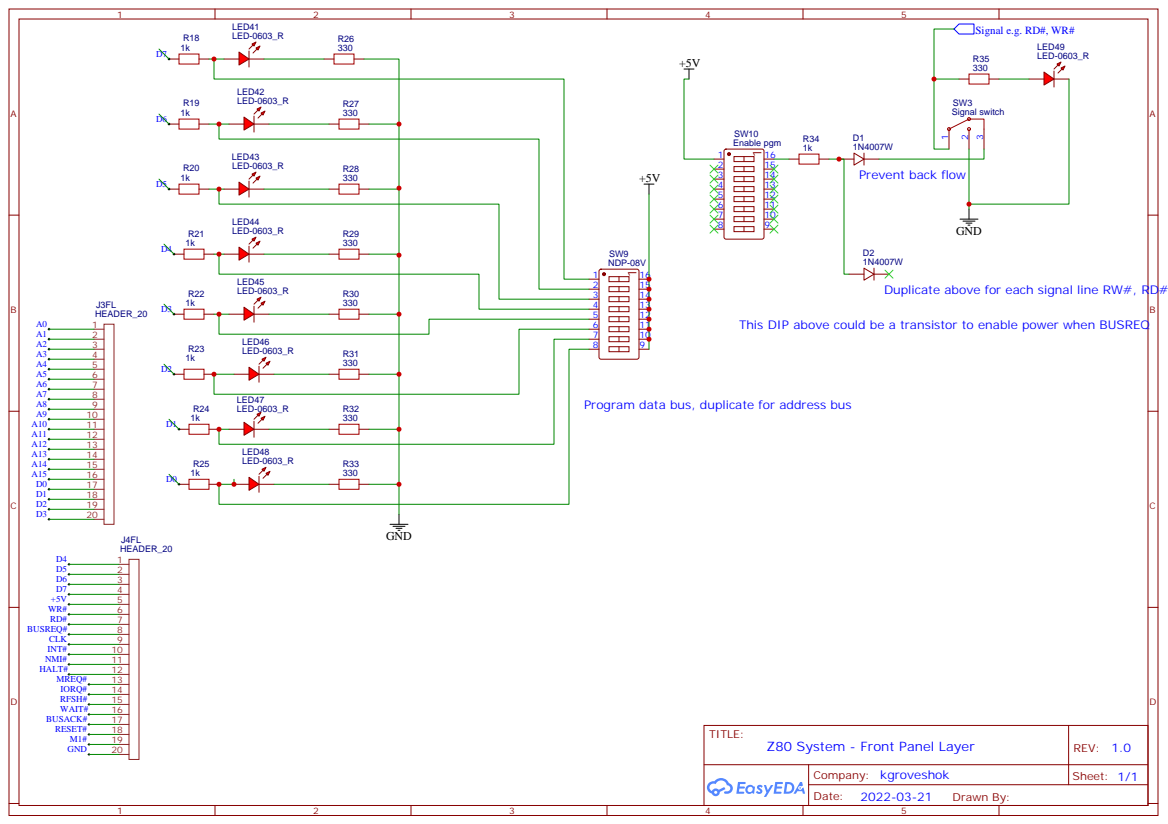
[picture p135: page 1]

Duplicate above for each signal line RW#, RD#, etc

This DIP above could be a transistor to enable power when BUSREQ

Program data bus, duplicate for address bus
