kgroveshok/z80-homebrew/stage2.0/Memory-Layer.pdf

+5V | +5V
WR# | WR#

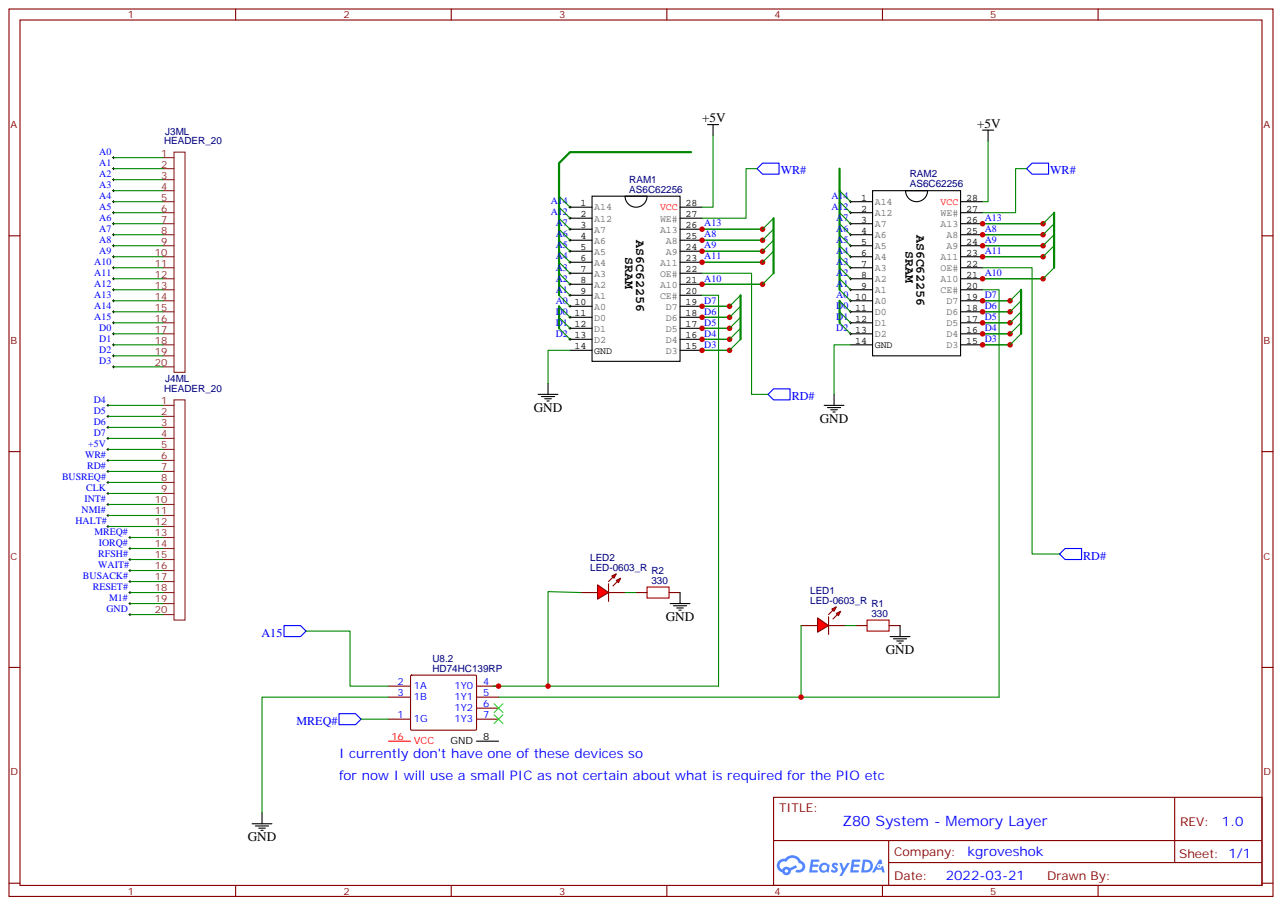
[picture p136: page 1]

I currently don't have one of these devices so
for now I will use a small PIC as not certain about what is required for the PIO etc
