kgroveshok/z80-homebrew/Schematics/PCB_PCB_z80-system-3-sbc_2025-04-02.pdf

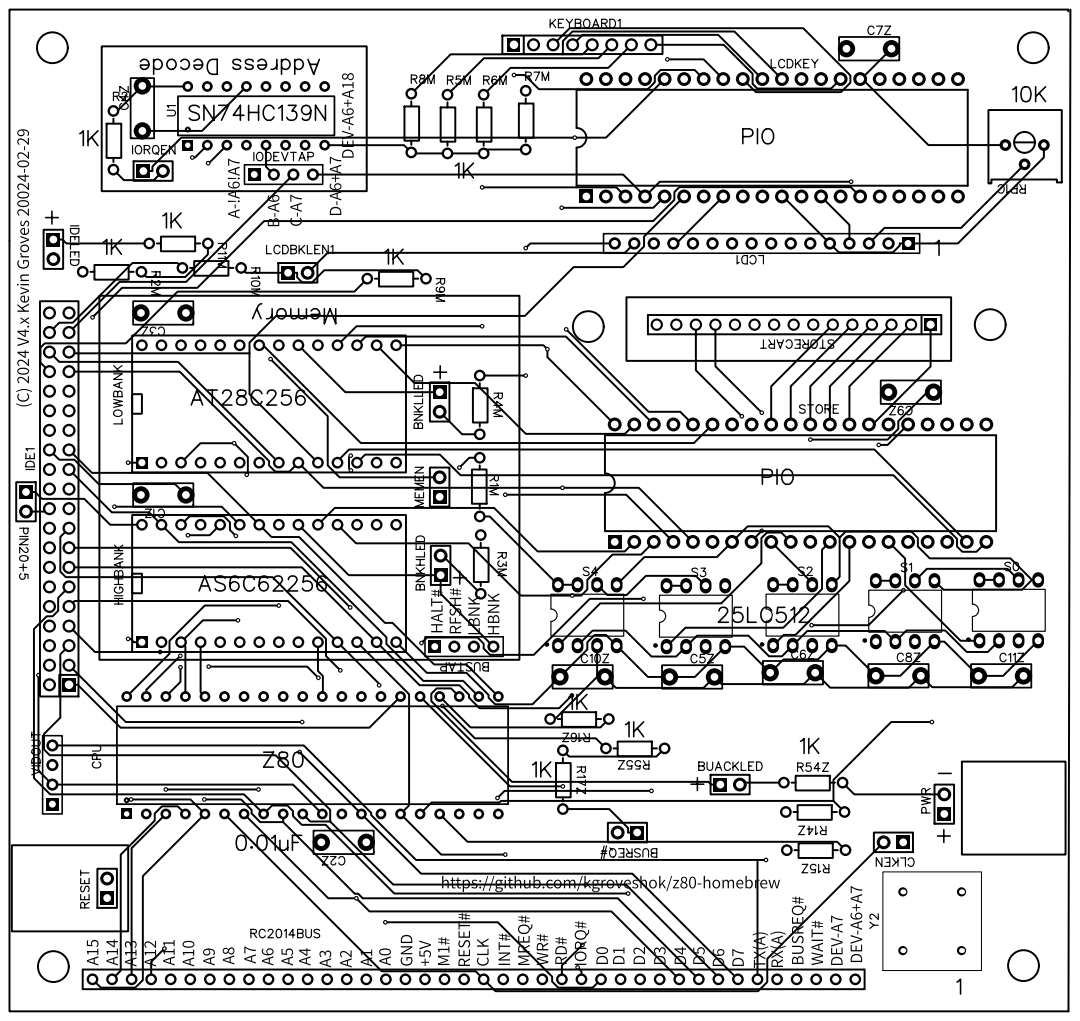
[picture p148: page 1]
