kgroveshok/z80-homebrew/Schematics/PCB_PCB_z80-system-4-maxi keyboard_2025-04-02.pdf

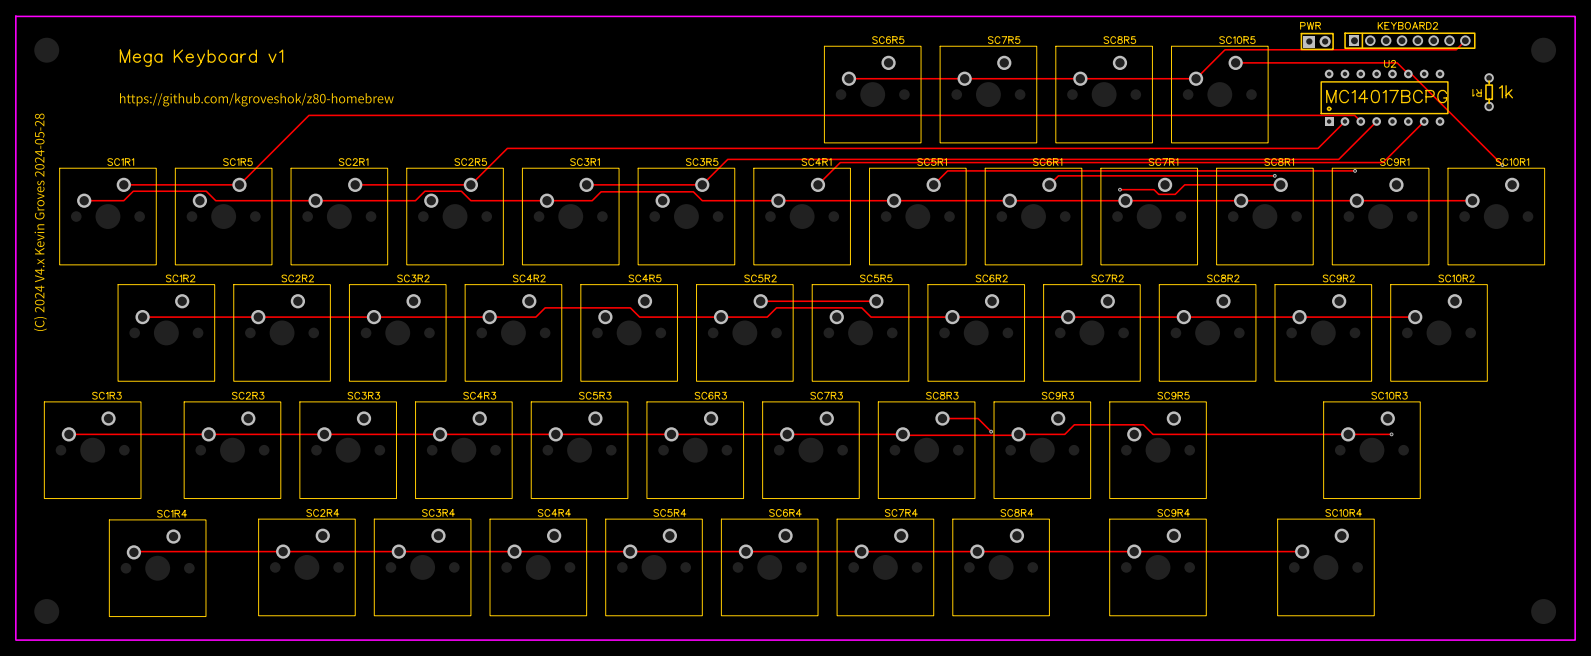
[picture p149: page 1]
