kgroveshok/z80-homebrew/Schematics/Schematic_z80-system-4-maxi keyboard_2025-04-02.pdf

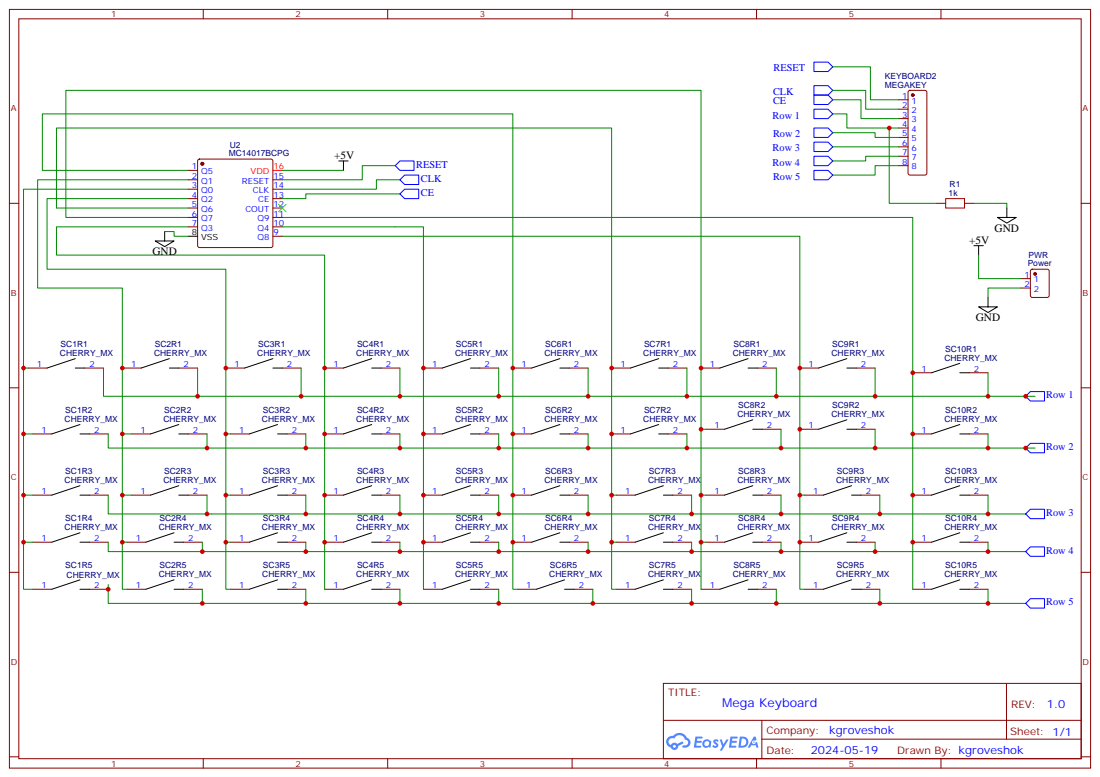
[picture p150: page 1]
