kgroveshok/z80-homebrew/Schematics/Schematic_z80-system-4-sbc copy_2025-04-02.pdf

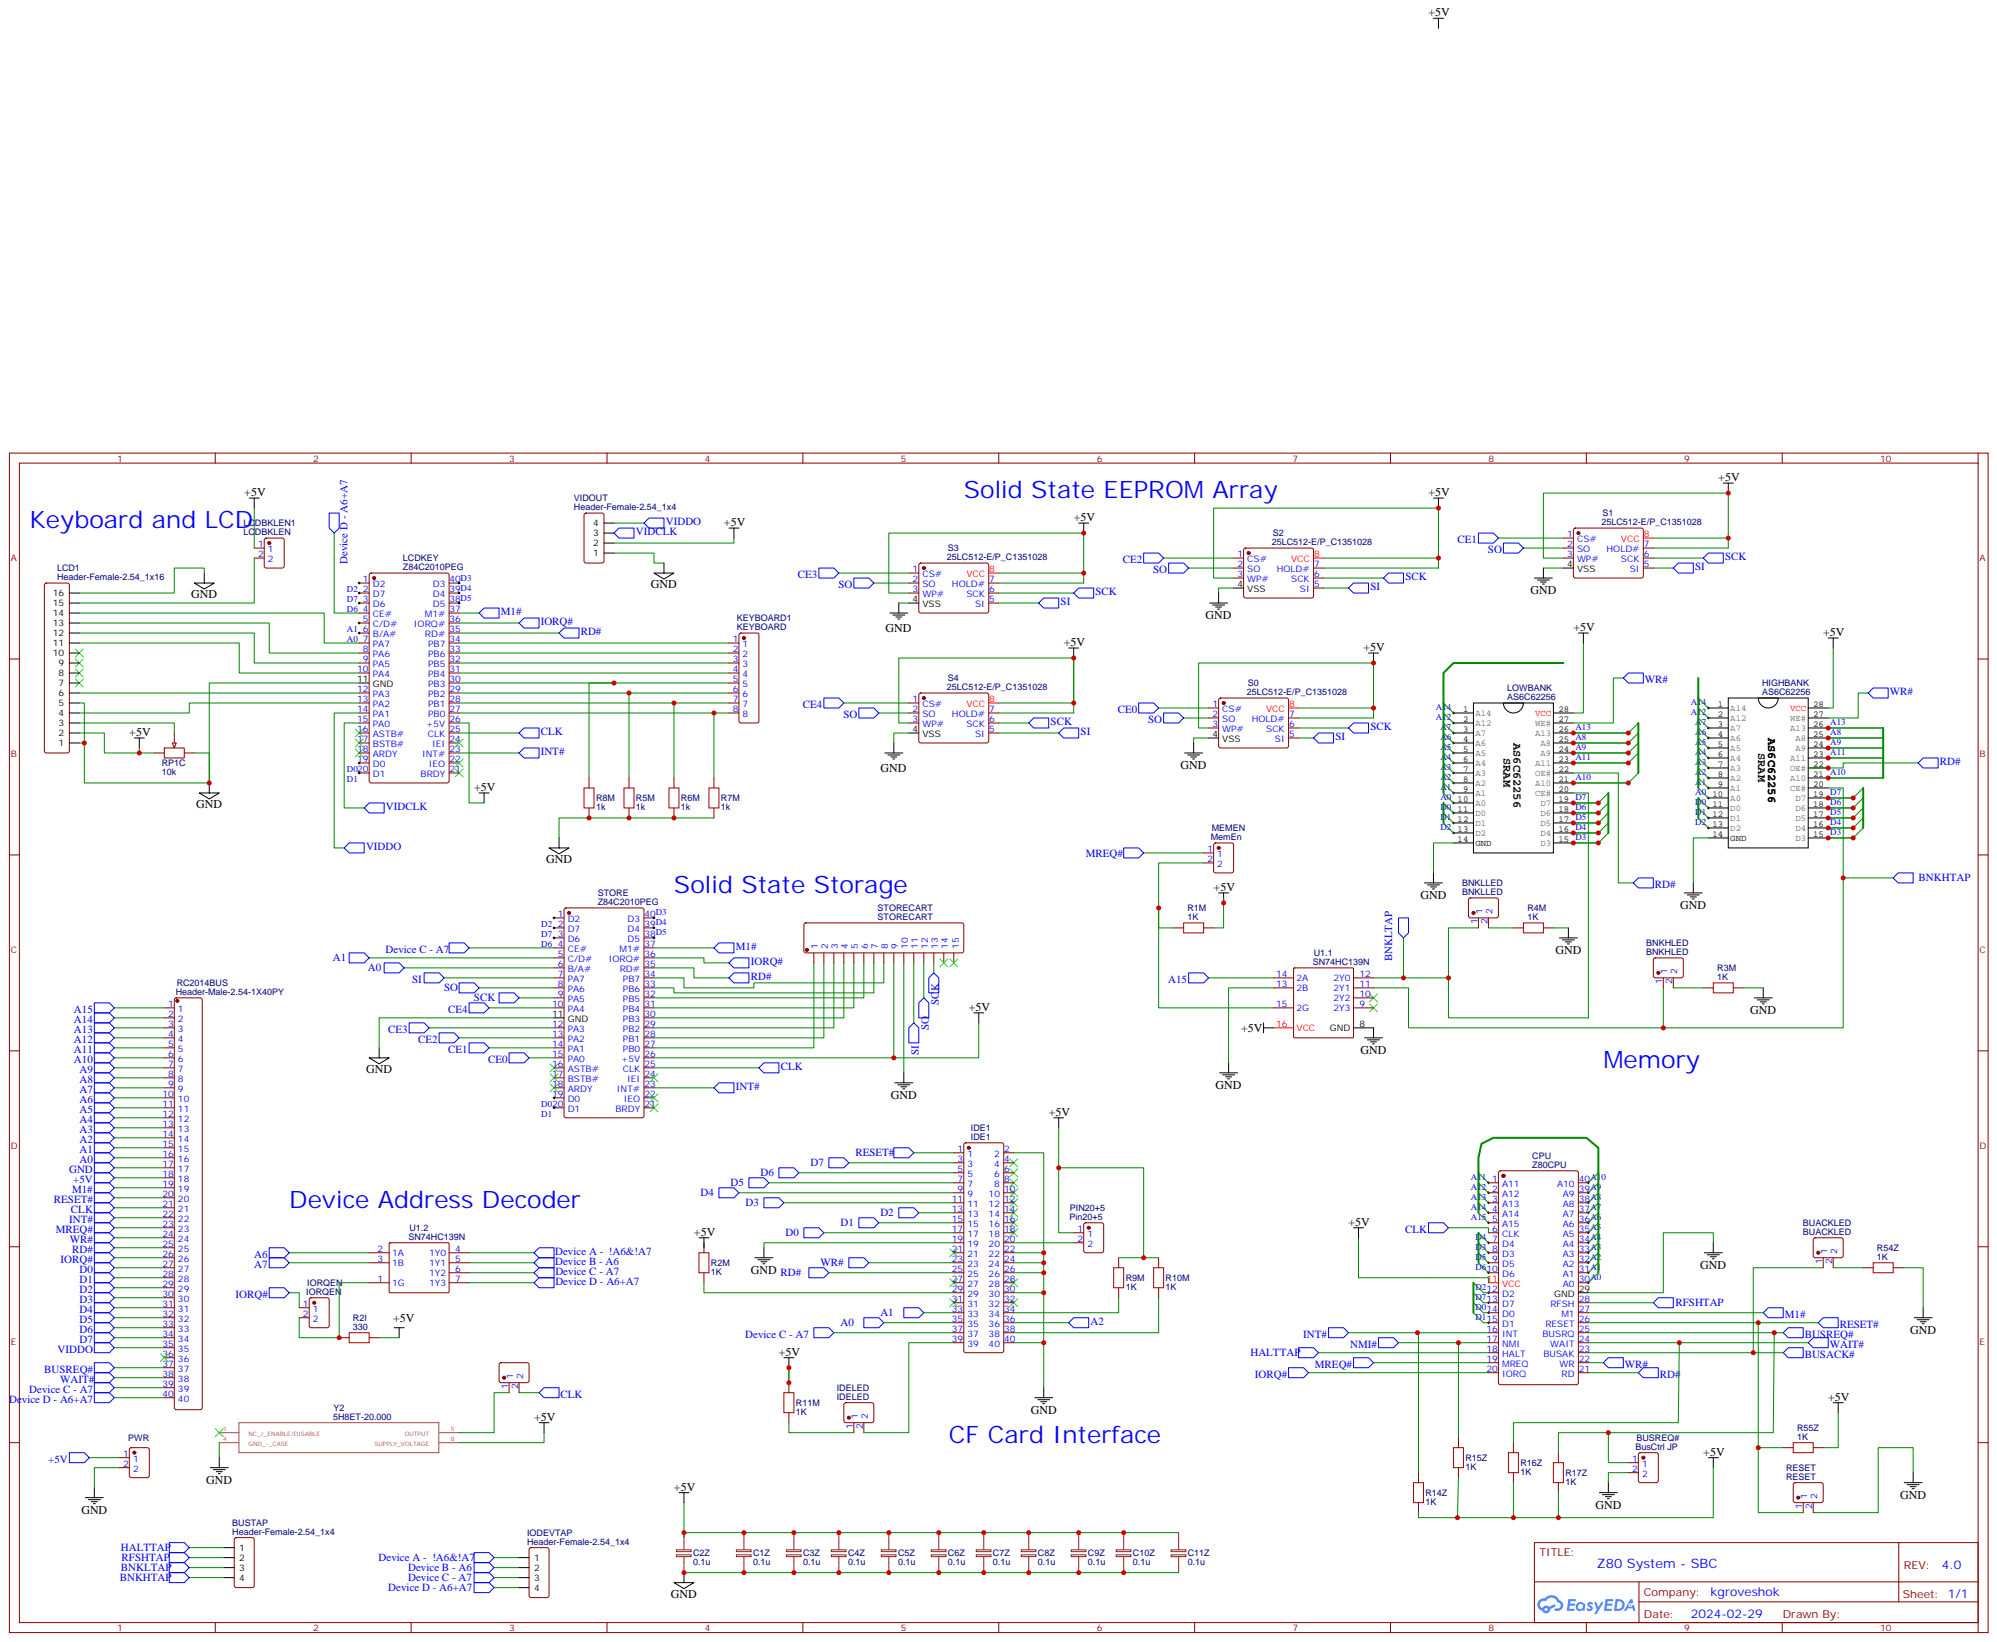
[picture p151: page 1]

Solid State EEPROM Array
