kgroveshok/z80-homebrew/stage4.0/Schematic_z80-system-4-sbc-2024-03-02.pdf

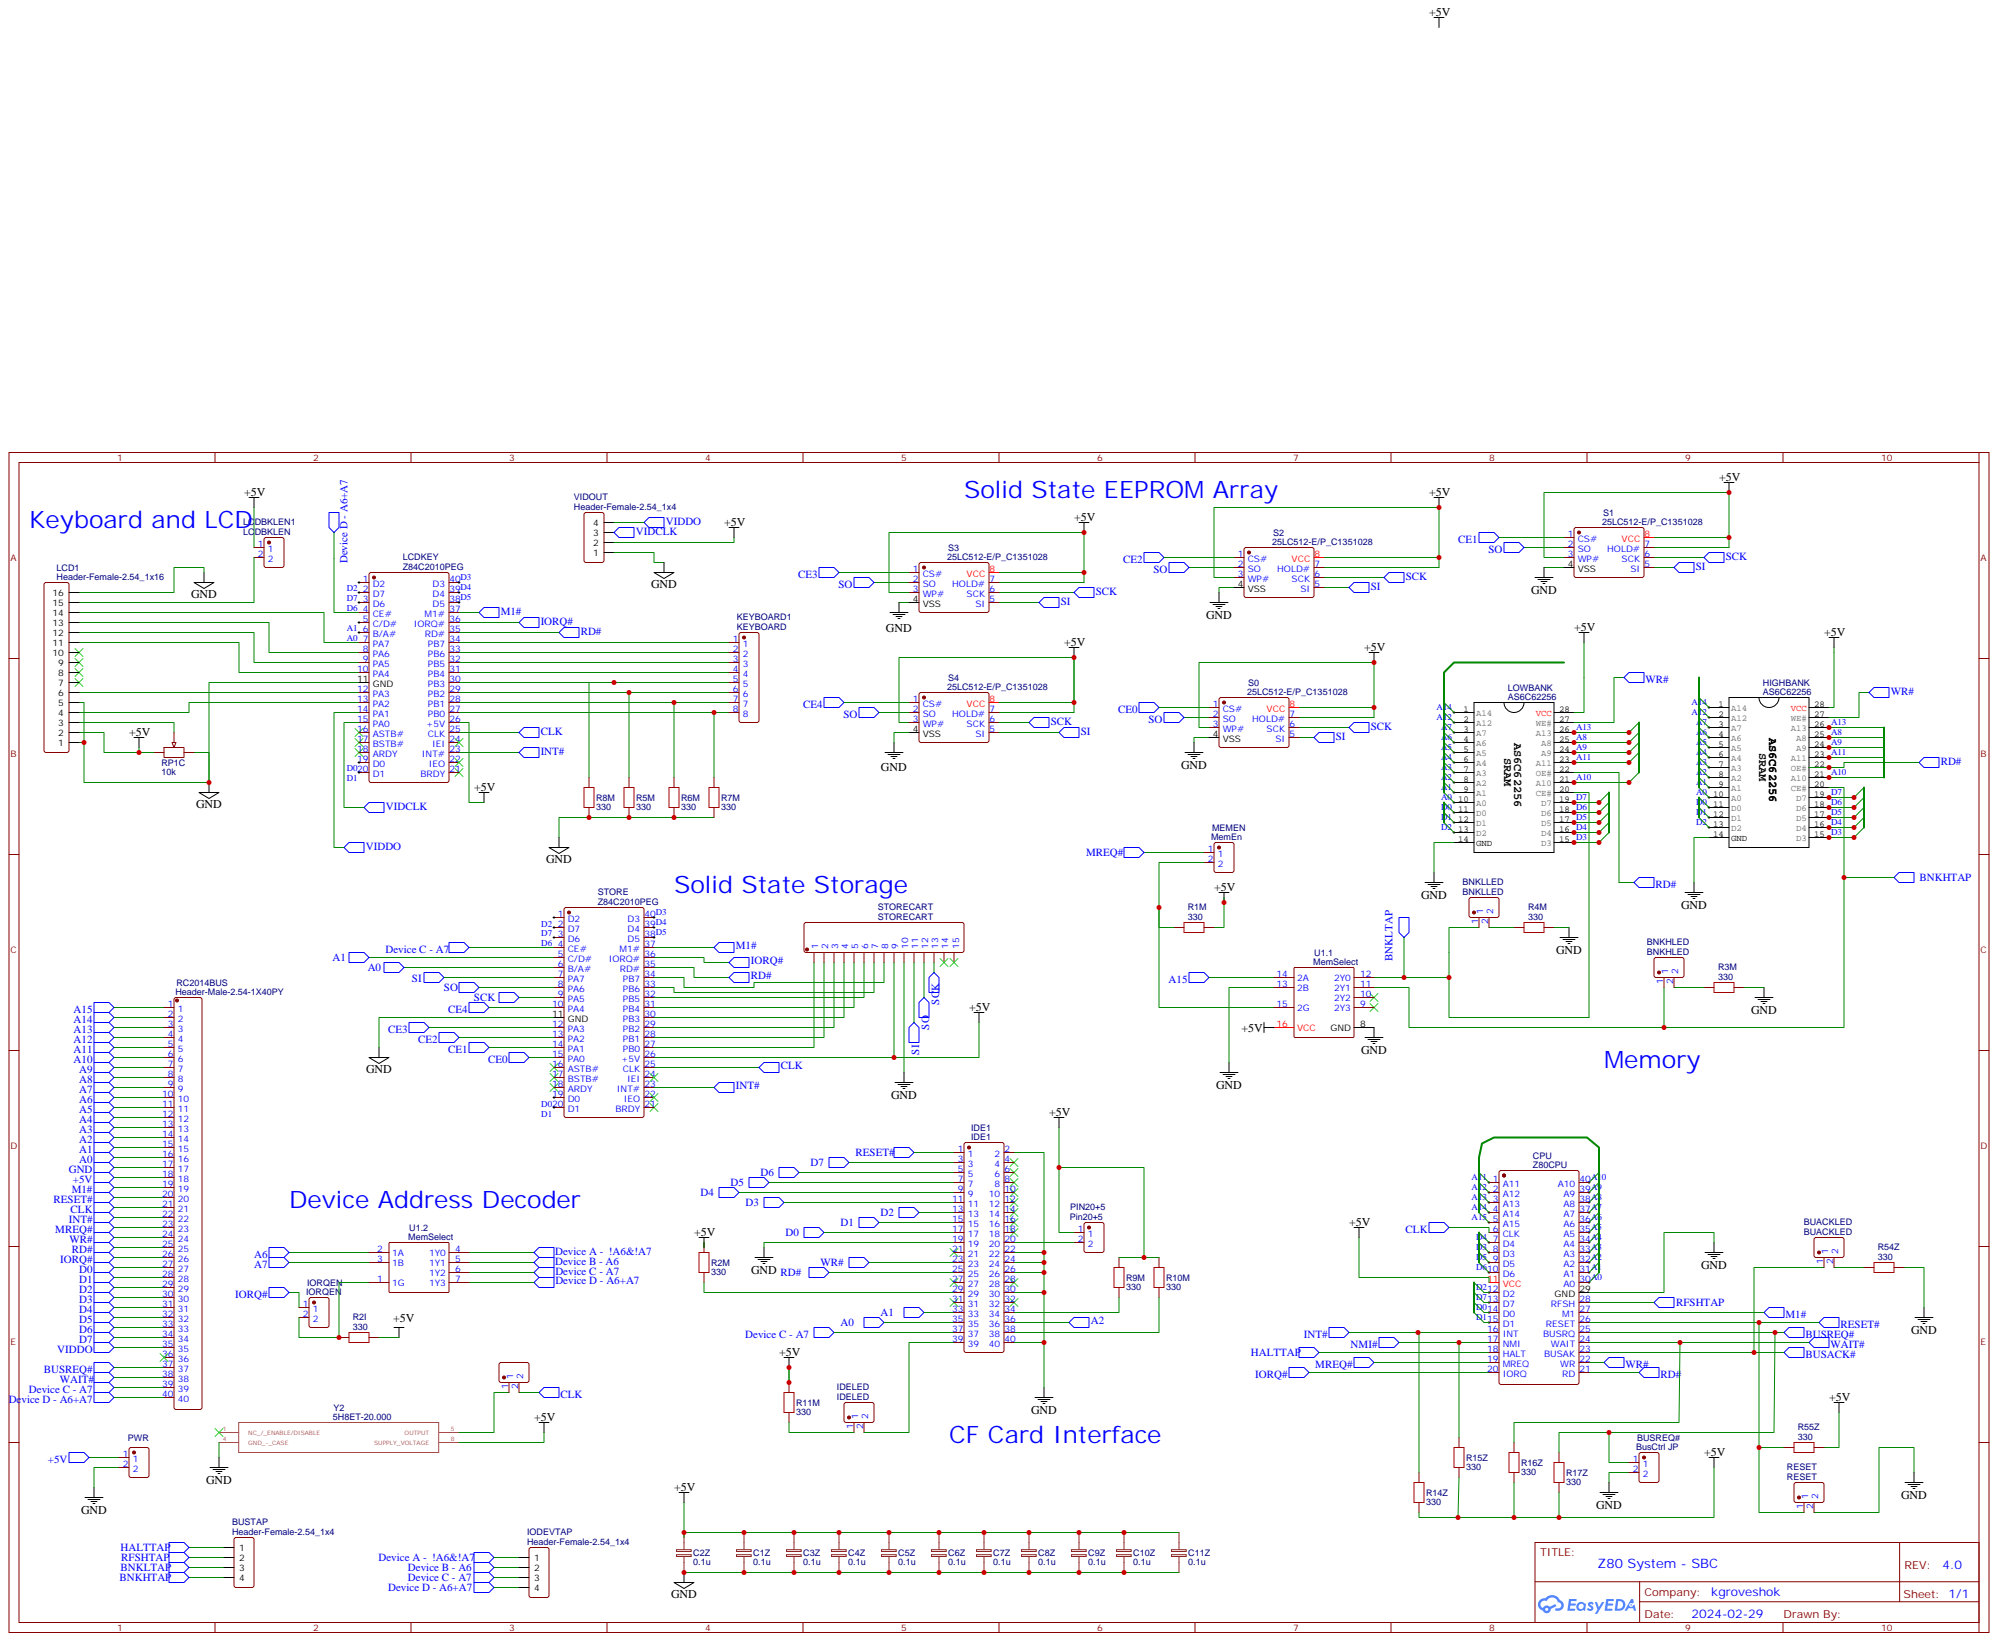
[picture p152: page 1]

Solid State EEPROM Array
