kgroveshok/z80-homebrew/stage3.0/Schematic_z80-system-3-sbc_2023-07-12.pdf

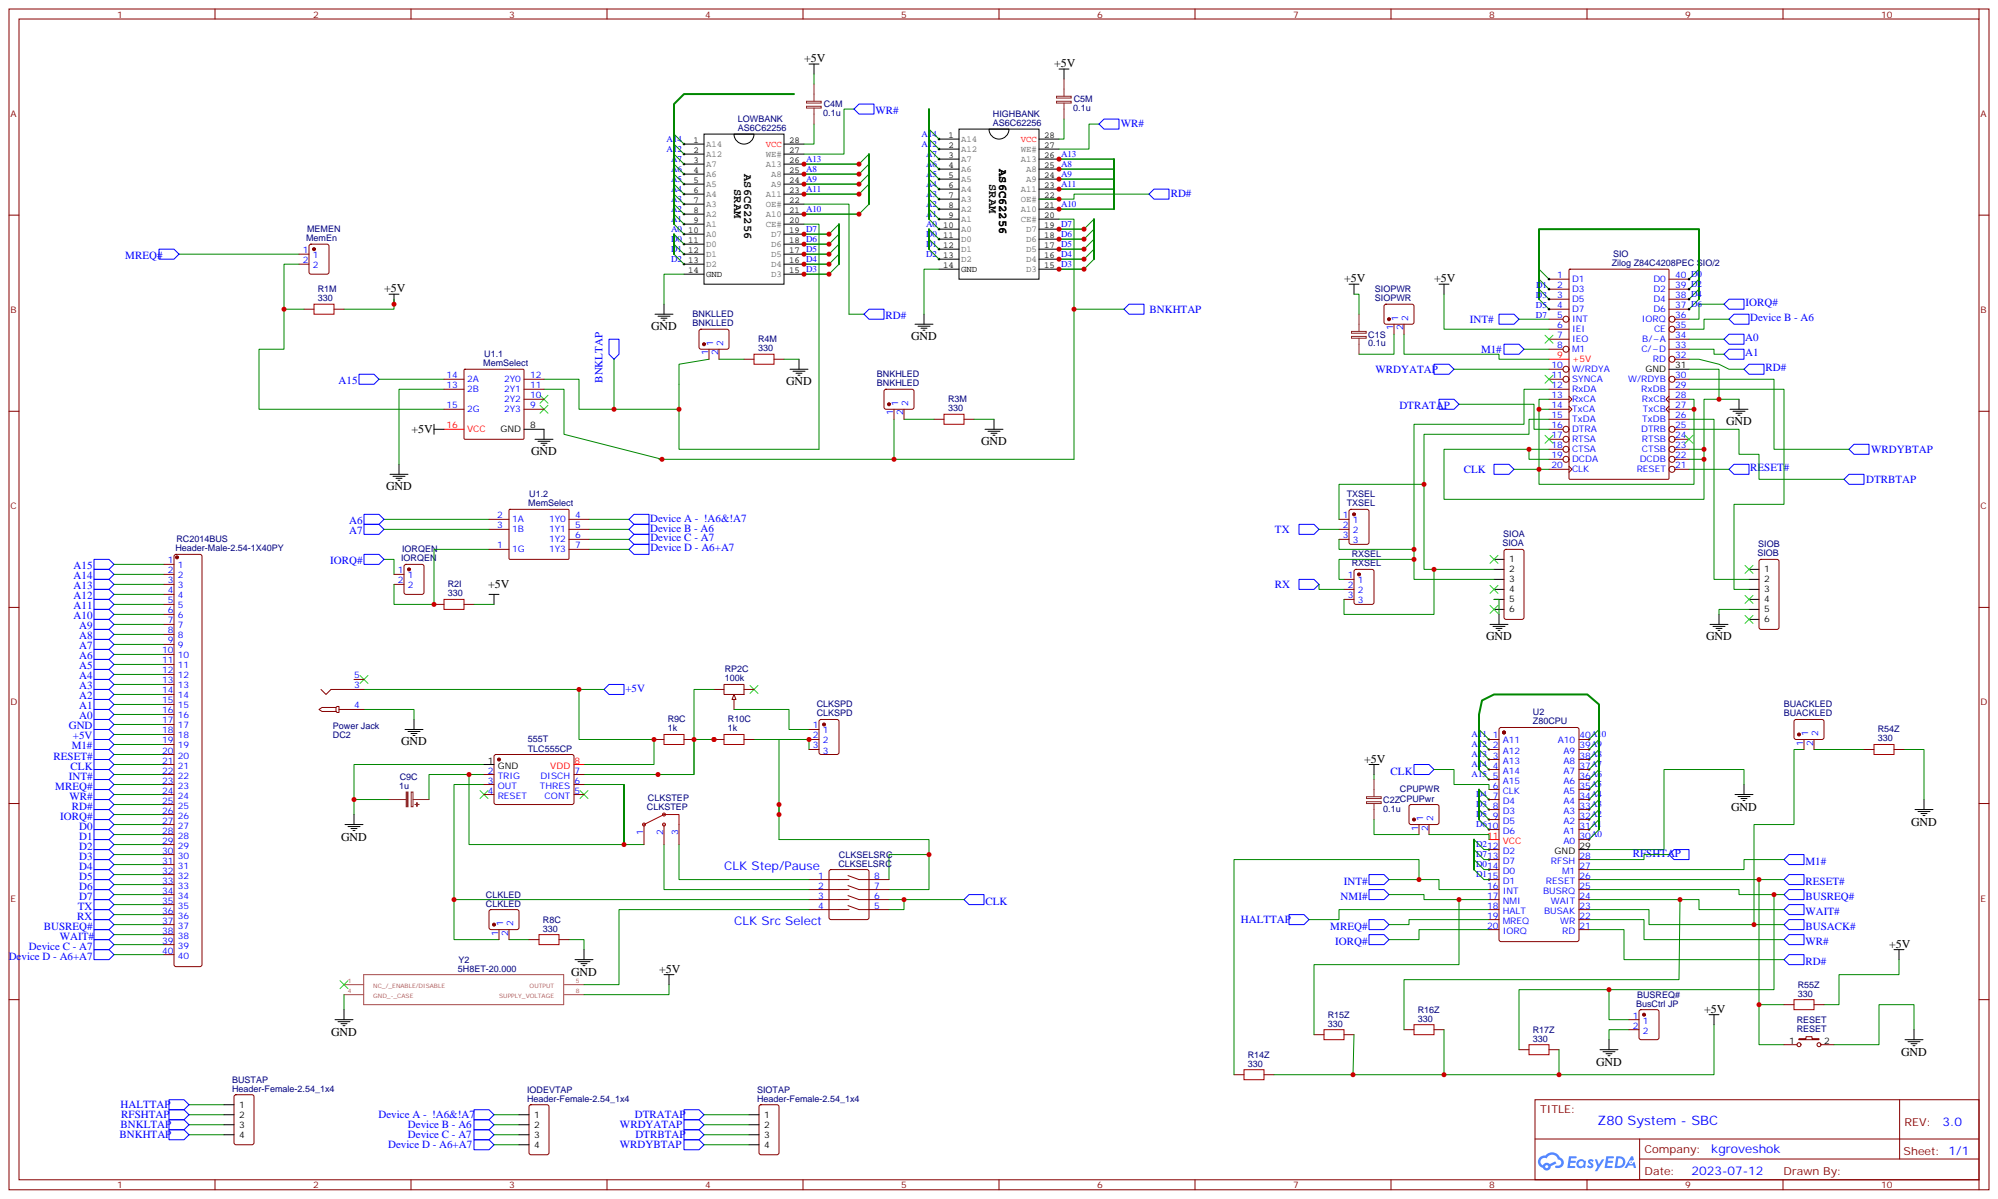
[picture p153: page 1]
