kgroveshok/z80-homebrew/stage3.0/PCB_PCB_z80-system-3-sbc_2023-07-12.pdf

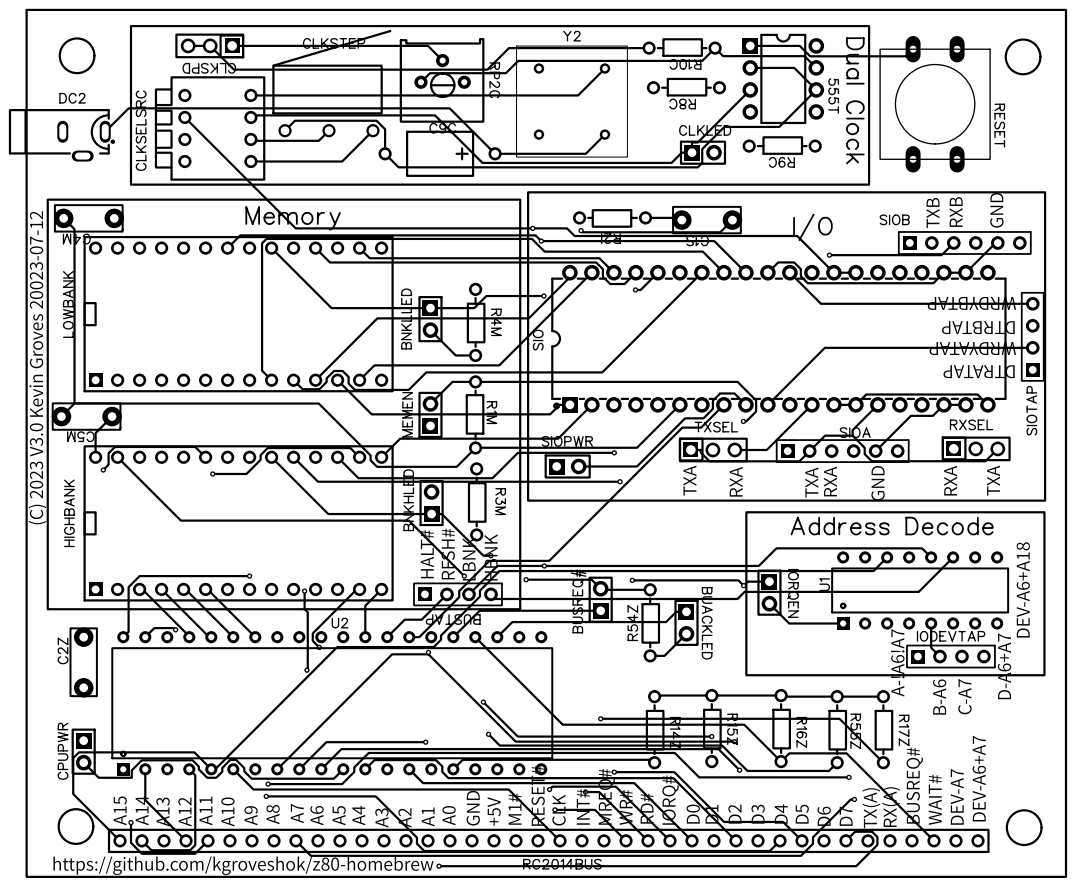
[picture p154: page 1]
