kgroveshok/z80-homebrew/stage2.0/CPU-Layer.pdf

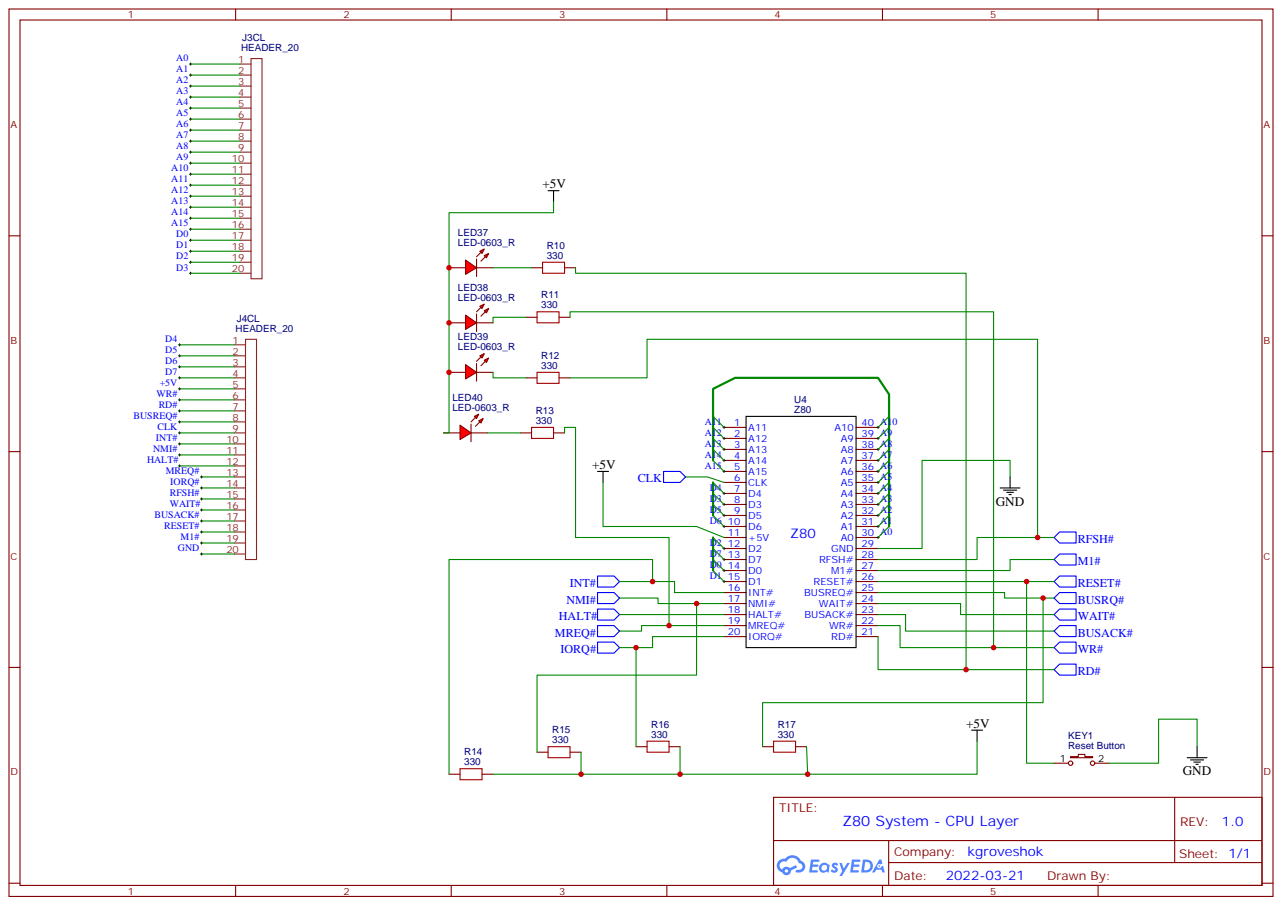
[picture p155: page 1]
