kgroveshok/z80-homebrew/stage2.0/PIC-Loader-Layer.pdf

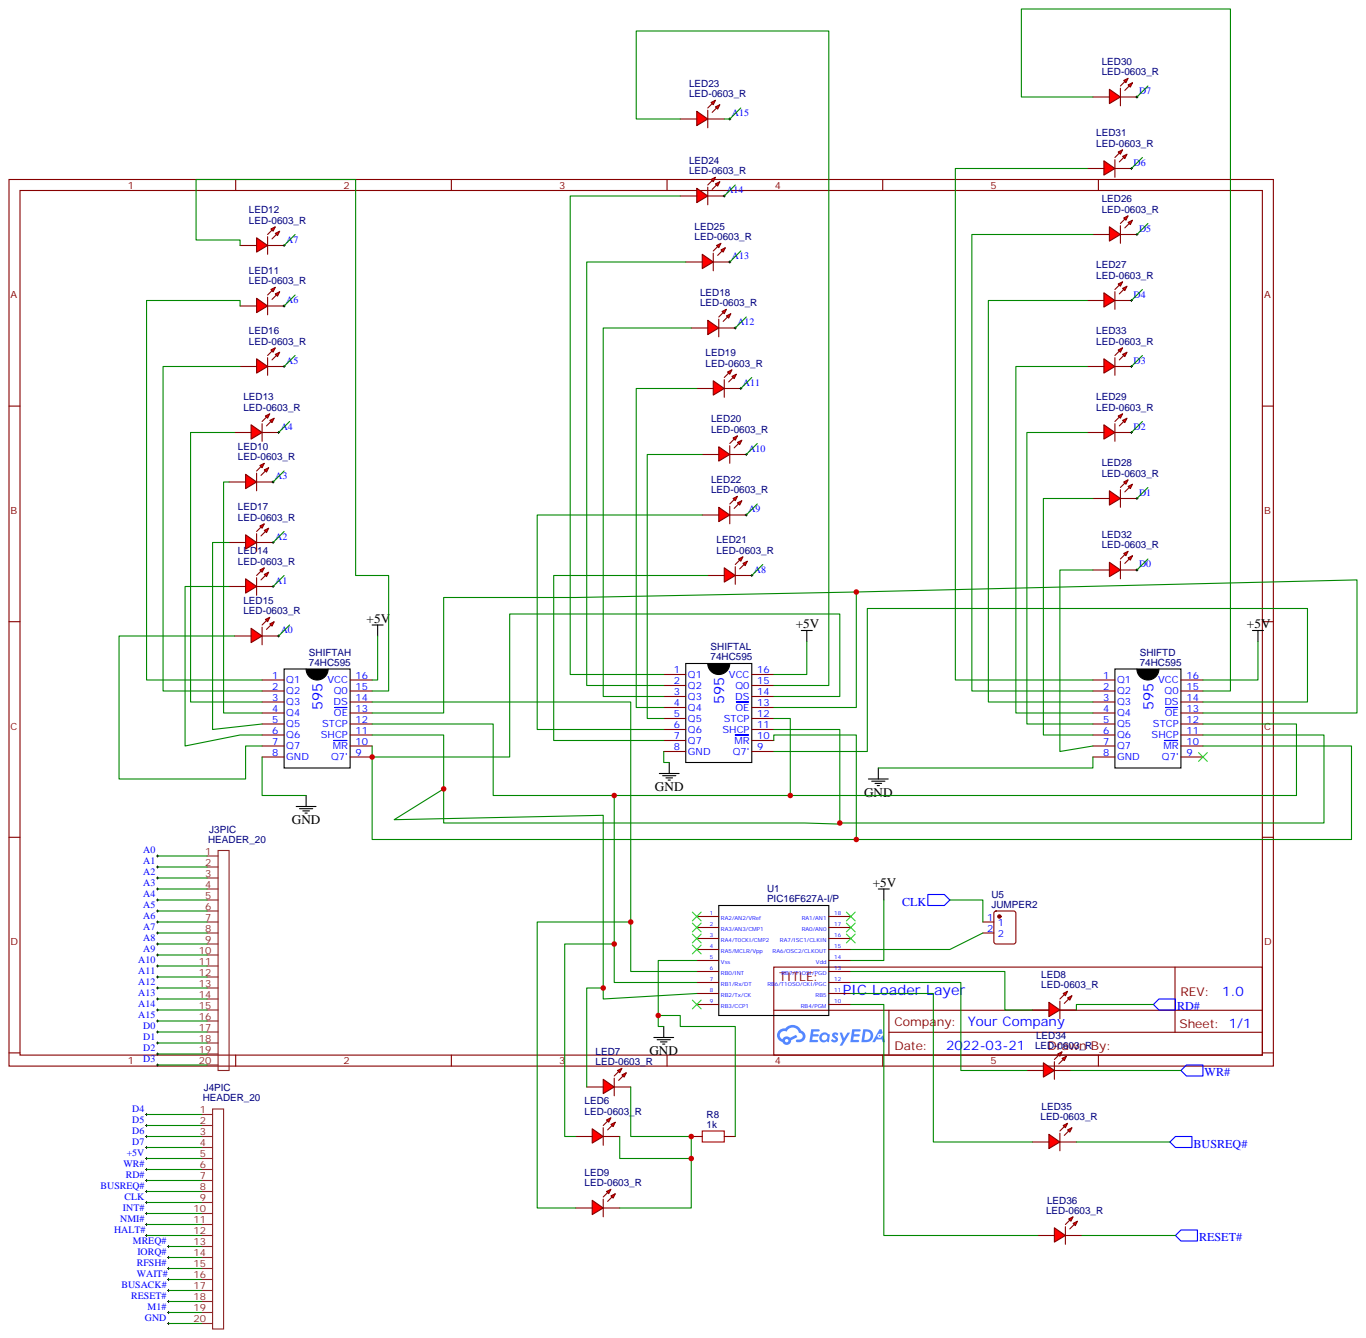
[picture p156: page 1]
