kgroveshok/z80-homebrew/stage2.0/Power-Layer.pdf

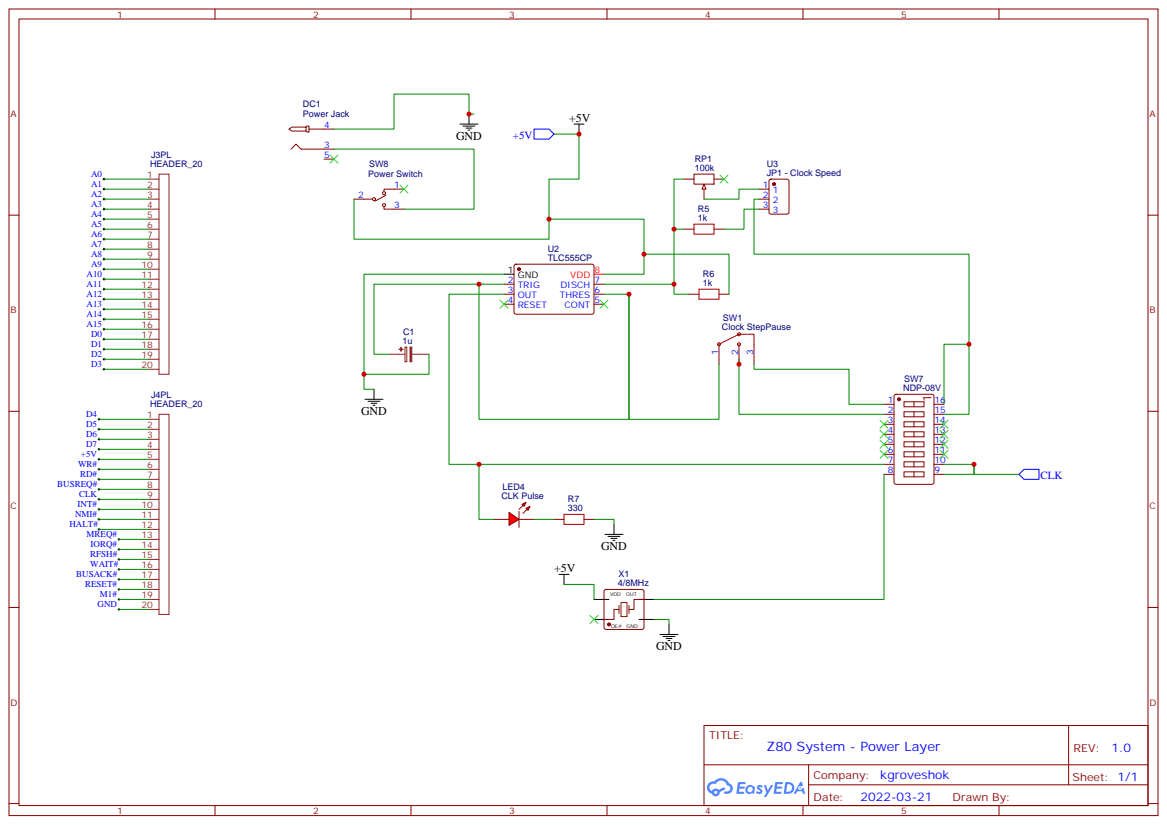
[picture p157: page 1]
