kgroveshok/z80-homebrew/os/forth_kernel.asm

;
; kernel to the forth OS

DS_TYPE_STR: equ 1     ; string type
DS_TYPE_INUM: equ 2     ; $ 16 bit unsigned int usually a hex address
DS_TYPE_SNUM: equ 3     ; $ 16 bit signed int 
DS_TYPE_CONST: equ 4     ; string type that won't be freed on a POP
;DS_TYPE_FNUM: equ 3      ; 24/32 bit floating point  do string conversion instead of a new type

FORTH_PARSEV1: equ 0
FORTH_PARSEV2: equ 0
FORTH_PARSEV3: equ 0
FORTH_PARSEV4: equ 0
FORTH_PARSEV5: equ 0
FORTH_PARSEV6: equ 1

;if FORTH_PARSEV5
;	FORTH_END_BUFFER: equ 0
;else
FORTH_END_BUFFER: equ 127
;endif

FORTH_TRUE: equ 1
FORTH_FALSE: equ 0

if FORTH_PARSEV4
include "forth_stackops.asm"
endif

if FORTH_PARSEV5
include "forth_stackopsv5.asm"
endif

if FORTH_PARSEV6
include "forth_stackopsv5.asm"
endif
loadwordinhl:	

	push de

	ld e, (hl)
	inc hl
	ld d, (hl)
	ex de,hl 

	pop de

	ret

user_word_eol: 
	; hl contains the pointer to where to create a linked list item from the end
	; of the user dict to continue on at the system word dict
	
	; poke the stub of the word list linked list to repoint to rom words

	; stub format
	; db   word id
	; dw    link to next word
        ; db char length of token
	; db string + 0 term
	; db exec code.... 

;	ld a, WORD_SYS_ROOT     ; root word
	ld (hl), WORD_SYS_ROOT		; word id
	inc hl

	ld de, sysdict
	ld (hl), e		; next word link ie system dict
	inc hl
	ld (hl), d		; next word link ie system dict
	inc hl	

;	ld (hl), sysdict		; next word link ie system dict
;	inc hl
;	inc hl

;	inc hl
;	inc hl

;	ld a, 2			; word length is 0
	ld (hl), 2
	inc hl

;	ld a, '~'			; word length is 0
	ld (hl), '~'
	inc hl
;	ld a, 0			; save empty word
	ld (hl), 0

	ret

	

forthexec_cleanup:
	FORTH_RSP_POP
	ret

forth_call_hl:
	; taking hl
	push hl
	ret

; this is called to reset Forth system but keep existing uwords etc

forth_warmstart:
	; setup stack over/under flow checks
	if DEBUG_FORTH_STACK_GUARD
		call chk_stk_init
	endif

	; init stack pointers  - * these stacks go upwards * 
	ld hl, cli_ret_stack
	ld (cli_ret_sp), hl	
	; set bottom of stack
;	ld a,0
	ld (hl),0
	inc hl
	ld (hl),0

	ld hl, cli_data_stack
	ld (cli_data_sp), hl	
	; set bottom of stack
;	ld a,0
	ld (hl),0
	inc hl
	ld (hl),0

	ld hl, cli_loop_stack
	ld (cli_loop_sp), hl	
	; set bottom of stack
;	ld a,0
	ld (hl),0
	inc hl
	ld (hl),0

	; init extent of current open file

	ld a, 0
	ld (store_openext), a

	ret



; Cold Start - this is called to setup the whole Forth system

forth_init:

	; setup stack over/under flow checks

;	if DEBUG_FORTH_STACK_GUARD
;		call chk_stk_init
;	endif

	; enable auto display updates (slow.....)

	ld a, 1
	ld (cli_autodisplay), a

	; if storage is in use disable long reads for now
	ld a, 0
	ld (store_longread), a


	; show start up screen

	call clear_display

	ld a,0
	ld (f_cursor_ptr), a

	; set start of word list in start of ram - for use when creating user words

	ld hl, baseram
	ld (os_last_new_uword), hl
	call user_word_eol
	
;		call display_data_sp
;		call next_page_prompt




	ret

.bootforth: db " Forth Kernel Init ",0

; TODO push to stack

; 

if FORTH_PARSEV2


	include "forth_parserv2.asm"

endif


; parse cli version 1

if FORTH_PARSEV1



      include "forth_parserv1.asm"
endif
	
if FORTH_PARSEV3
      include "forth_parserv3.asm"
	include "forth_wordsv3.asm"
endif

if FORTH_PARSEV4
      include "forth_parserv4.asm"
	include "forth_wordsv4.asm"
endif

if FORTH_PARSEV5
      include "forth_parserv5.asm"
	include "forth_wordsv4.asm"
endif

if FORTH_PARSEV6
      include "forth_parserv6.asm"
	include "forth_wordsv4.asm"
endif
;;;;;;;;;;;;;; Debug code


;if DEBUG_FORTH_PARSE
.nowordfound: db "No match",0
.compword:	db "Comparing word ",0
.nextwordat:	db "Next word at",0
.charmatch:	db "Char match",0
;endif
if DEBUG_FORTH_JP
.foundword:	db "Word match. Exec..",0
endif
;if DEBUG_FORTH_PUSH
.enddict:	db "Dict end. Push.",0
.push_str:	db "Pushing string",0
.push_num:	db "Pushing number",0
.data_sp:	db "SP:",0
.wordinhl:	db "Word in HL (2/0):",0
.wordinde:	db "Word in DE (3/0):",0
.wordinbc:	db "Word in BC (4/0):",0
;endif
;if DEBUG_FORTH_MALLOC
.push_malloc:	db "Malloc address",0
;endif



; display malloc address and current data stack pointer 

malloc_error:
	push de
	push af
	push hl
	call clear_display
	ld de, .mallocerr
	ld a,0
;	ld de,os_word_scratch
	call str_at_display
	ld a, display_row_1+17
if DEMARK_VERSION = 1
	ld de, (debug_mark)
endif

if DEMARK_VERSION = 0
	ld de, debug_mark
endif

	call str_at_display
	call update_display
	;call break_point_state
	call cin_wait

;	ld a, ' '
;	ld (os_view_disable), a
	call bp_on
	pop hl
	pop af
	pop de	
	CALLMONITOR
	ret

.mallocerr: 	db "Malloc Error",0
;if DEBUG_FORTH_PUSH
display_data_sp:
	push af

	; see if disabled


	ld a, (debug_vector)
	cp $C9  ; RET
	;ld a, (os_view_disable)
	;cp '*'
	jr z, .skipdsp

	push hl
	push hl
push hl
	call clear_display
pop hl
	ld a,h
	ld hl, os_word_scratch
	call hexout
	pop hl
	ld a,l
	ld hl, os_word_scratch+2
	call hexout
	ld hl, os_word_scratch+4
;	ld a,0
	ld (hl),0
	ld de,os_word_scratch
		ld a, display_row_2
		call str_at_display
	ld de, .wordinhl
	ld a, display_row_1

		call str_at_display
;	ld de, debug_mark
if DEMARK_VERSION = 1
	ld de, (debug_mark)
endif

if DEMARK_VERSION = 0
	ld de, debug_mark
endif
	ld a, display_row_1+17

		call str_at_display

	; display current data stack pointer
	ld de,.data_sp
		ld a, display_row_2 + 8
		call str_at_display

	ld hl,(cli_data_sp)
	push hl
	ld a,h
	ld hl, os_word_scratch
	call hexout
	pop hl
	ld a,l
	ld hl, os_word_scratch+2
	call hexout
	ld hl, os_word_scratch+4
;	ld a,0
	ld (hl),0
	ld de,os_word_scratch
		ld a, display_row_2 + 11
		call str_at_display


	call update_display
	call delay1s
	call delay1s
	pop hl
.skipdsp:
	pop af
	ret

display_data_malloc:

	push af
	push hl
	push hl
push hl
	call clear_display
pop hl
	ld a,h
	ld hl, os_word_scratch
	call hexout
	pop hl
	ld a,l
	ld hl, os_word_scratch+2
	call hexout
	ld hl, os_word_scratch+4
;	ld a,0
	ld (hl),0
	ld de,os_word_scratch
		ld a, display_row_2
		call str_at_display
	ld de, .push_malloc
	ld a, display_row_1

		call str_at_display

	; display current data stack pointer
	ld de,.data_sp
		ld a, display_row_2 + 8
		call str_at_display

	ld hl,(cli_data_sp)
	push hl
	ld a,h
	ld hl, os_word_scratch
	call hexout
	pop hl
	ld a,l
	ld hl, os_word_scratch+2
	call hexout
	ld hl, os_word_scratch+4
;	ld a,0
	ld (hl),0
	ld de,os_word_scratch
		ld a, display_row_2 + 11
		call str_at_display

	call update_display
	call delay1s
	call delay1s
	pop hl
	pop af
	ret
;endif

include "forth_autostart.asm"



; stack over and underflow checks

; init the words to detect the under/overflow

chk_stk_init:
	; a vague random number to check so we dont get any "lucky" hits
	ld a, 45
	ld l, a
	nop
	ld a, 23
	ld h, a

	ld (chk_word), hl     ; the word we need to check against

;	ld (chk_stund), hl	; stack points....
	ld (chk_stovr), hl
	ld (chk_ret_und), hl
	ld (chk_ret_ovr), hl
	ld (chk_loop_ovr), hl
	ld (chk_data_ovr), hl
	ret
	
check_stacks:
	; check all stack words for corruption

	; Stack checks 


	; stack over
	; return under
	; return over
	; loop over
	; data over


	push hl
	ld hl, (hardware_config+1)
	bit 7, (hl)

	jr nz, .dochecks

	pop hl
	ret

.dochecks:

	push de

;	ld de,(chk_word)
;	ld hl, (chk_stund)	; stack points....
;	if DEBUG_STK_FAULT
;		DMARK "FAa"
;		CALLMONITOR
;	endif
;	call cmp16
;	jp z, .chk_faulta
;
;	ld de, sfaultsu
;	jp .chk_fault

.chk_faulta: ld hl, (chk_stovr)
	ld de,(chk_word)
	if DEBUG_STK_FAULT
		DMARK "FAb"
		CALLMONITOR
	endif
	call cmp16
	jr z, .chk_fault1
	ld de, sfaultso
	jp .chk_fault
.chk_fault1: 
	ld hl, (chk_ret_und)
	ld de,(chk_word)
	if DEBUG_STK_FAULT
		DMARK "FAU"
		CALLMONITOR
	endif
	call cmp16
	jp z, .chk_fault2
	ld de, sfaultru
	jp .chk_fault
.chk_fault2: 
	ld hl, (chk_ret_ovr)
	ld de,(chk_word)
	if DEBUG_STK_FAULT
		DMARK "FA1"
		CALLMONITOR
	endif
	call cmp16
	jp z, .chk_fault3
	ld de, sfaultro
	jp .chk_fault
.chk_fault3: 
	ld hl, (chk_loop_ovr)
	ld de,(chk_word)
	if DEBUG_STK_FAULT
		DMARK "FA2"
		CALLMONITOR
	endif
	call cmp16
	jp z, .chk_fault4
	ld de, sfaultlo
	jp .chk_fault
.chk_fault4: 
	ld hl, (chk_data_ovr)
	ld de,(chk_word)
	if DEBUG_STK_FAULT
		DMARK "FA3"
		CALLMONITOR
	endif
	call cmp16
	jp z, .chk_fault5
	ld de, sfaultdo
	jp .chk_fault


.chk_fault5: 
	pop de
	pop hl

	ret

.chk_fault: 	call clear_display
		ld a, display_row_2
		call str_at_display
		   ld de, .stackfault
		ld a, display_row_1
		call str_at_display
if DEMARK_VERSION = 1
	ld de, (debug_mark)
endif

if DEMARK_VERSION = 0
	ld de, debug_mark
endif
;		    ld de, debug_mark
		ld a, display_row_1+17
		call str_at_display
		call update_display

	; prompt before entering montior for investigating issue

	ld a, display_row_4
	ld de, endprog

	call update_display		

	call next_page_prompt

	pop de
	pop hl
		call monitor
		call forth_warmstart
		jp warmstart_afterauto
		;jp 0
		;halt



.stackfault: 	db "Stack fault:",0

sfaultsu: 	db	"Stack under flow",0
sfaultso: 	db	"Stack over flow",0
sfaultru:	db "RTS underflow",0
sfaultro:	db "RTS overflow/LS underflow", 0
sfaultlo:	db "LS overflow/DTS underflow", 0
sfaultdo:	db "DTS overflow", 0


fault_dsp_under:
	ld de, .dsp_under
	jp .show_fault

fault_rsp_under:
	ld de, .rsp_under
	jp .show_fault
fault_loop_under:
	ld de, .loop_under
	jp .show_fault

.dsp_under: db "DSP Underflow",0
.rsp_under: db "RSP Underflow",0
.loop_under: db "LOOP Underflow",0


type_faultn: 	push de
		push hl
		call clear_display
		   ld de, .typefaultn
		ld a, display_row_1
		call str_at_display
;		    ld de, debug_mark
if DEMARK_VERSION = 1
	ld de, (debug_mark)
endif

if DEMARK_VERSION = 0
	ld de, debug_mark
endif
		ld a, display_row_1+17
		call str_at_display
		call update_display

	; prompt before entering montior for investigating issue

	ld a, display_row_4
	ld de, endprog

	call update_display		

	call next_page_prompt

		push hl
		push de
		call monitor
		call forth_warmstart
		jp warmstart_afterauto
		halt


.typefaultn: db "NUM Type Expected TOS!",0

type_faults: 	push de
		push hl
		call clear_display
		   ld de, .typefaults
		ld a, display_row_1
		call str_at_display
;		    ld de, debug_mark
if DEMARK_VERSION = 1
	ld de, (debug_mark)
endif

if DEMARK_VERSION = 0
	ld de, debug_mark
endif
		ld a, display_row_1+17
		call str_at_display
		call update_display

	; prompt before entering montior for investigating issue

	ld a, display_row_4
	ld de, endprog

	call update_display		

	call next_page_prompt

		pop hl
		pop de
		call monitor
		call forth_warmstart
		jp warmstart_afterauto


.typefaults: db "STR Type Expected TOS!",0

.show_fault: 	
		push de
		call clear_display
		pop de
		ld a, display_row_1
		call str_at_display
;		    ld de, debug_mark
if DEMARK_VERSION = 1
	ld de, (debug_mark)
endif

if DEMARK_VERSION = 0
	ld de, debug_mark
endif
		ld a, display_row_1+17
		call str_at_display
		call update_display

	; prompt before entering montior for investigating issue

	ld a, display_row_4
	ld de, endprog

	call update_display		

	call next_page_prompt

		pop hl
		pop de
		call monitor
; do a dump to cli and not warmstart so we preserve all of the uwords. 
; TODO Make optional fault restart to cli or warm boot?
		;jp warmstart
		jp cli
		halt


; handle the auto run of code from files in storage


include "forth_startup.asm"

; eof
