kgroveshok/z80-homebrew/os/firmware_strings.asm

; TODO string len
; input text string, end on cr with zero term
; a offset into frame buffer to start prompt
; d is max length
; e is display size TODO
; c is current cursor position
; hl is ptr to where string will be stored and edited directly


; TODO check limit of buffer for new inserts
; TODO check insert does not push beyond buffer
; TODO scroll in a limited display area
; TODO scroll whole screen on page wrap


; TODO use LCD cursor?

EDIT_V1: equ 0
EDIT_V2: equ 1



if EDIT_V2
input_str:

	    	ld (input_at_pos),a      ; save display position to start
;		ld (input_at_cursor),a	; save draw pos of cursor relative to start
		ld (input_start), hl     ; save ptr to buffer
;		ld a, c
;		call addatohl
;		ld (input_ptr), hl     ; save ptr to point under the cursor
		ld a,d
	        ld (input_size), a       ; save length of input area
		ld a, c
		ld (input_cursor),a      ; init cursor start position relative to start of string
		ld a,e
	        ld (input_display_size), a       ; save length of input area that is displayed TODO


		; add a trailing space to make screen refresh nicer

		;ld hl, (input_start)
		;push hl
		;ld a, 0
		;call strlent
		;ld a, l
		;pop hl
		;call addatohl
		;dec hl
		;ld a, ' '
		;ld (hl), a
		;inc hl
		;ld (hl), a
		;inc hl
		;ld a, 0
		;ld (hl), a

; TODO move out to cin as cursor shape is used by the 4x4 ???
		; init cursor shape if not set by the cin routines
		ld hl, cursor_shape
if BASE_KEV
;		ld a, 255
		ld (hl), 255
else
		;ld a, '#'
		ld (hl), '#'
endif
		inc hl
;		ld a, 0
		ld (hl), 0

		ld a, CUR_BLINK_RATE
		ld (input_cur_flash), a
		ld a, 1
		ld (input_cur_onoff),a
.inmain:	

		call input_disp_ref

		; save current length of string

		ld hl, (input_start)
		ld a, 0
		call strlent
		ld a,l
		ld (input_len), a

		;call input_disp_oncur

		; display current state of input buffer

		; clean any backspace chars

		ld a, " "
		ld (scratch),a
		ld a, 0
		ld (scratch+1),a
		ld a,(input_at_pos)
		add l
		ld de, scratch
		call str_at_display

		; pause 1ms

		ld a, 1
		call aDelayInMS

; display cursor if visible on this cycle

		; dec flash counter
		ld a, (input_cur_flash)
		dec a
		ld (input_cur_flash), a
;		cp 0
		or a
		jr nz, .inochgstate


		; reset on change of state
		ld a, CUR_BLINK_RATE
		ld (input_cur_flash), a

		; change state
		ld a,(input_cur_onoff)
		neg
		ld (input_cur_onoff),a




		; TODO is cursor visible?
		; TODO if so then over write the char at curspos pos with the cursor shape

					

.inochgstate:
		ld a,(input_cur_onoff)
		cp 255
		jr z, .skipcursor
		ld a, (input_at_pos)
		ld b, a
		ld a, (input_cursor)
		add b
		ld de, cursor_shape
		
		call str_at_display

.skipcursor:
	if DEBUG_INPUTV2

		ld a,(input_at_pos)
		ld hl, LFSRSeed
		call hexout
		ld a, (input_cursor)
		ld hl, LFSRSeed+2
		call hexout
		ld a,(input_size)
		ld hl, LFSRSeed+4
		call hexout

		ld a,(input_cur_onoff)
		ld hl, LFSRSeed+6
		call hexout

		ld a,(input_cur_flash)
		ld hl, LFSRSeed+8
		call hexout

		ld a,(input_len)
		ld hl, LFSRSeed+10
		call hexout
		ld hl, LFSRSeed+12
;		ld a, 0
		ld (hl),0
		ld a, display_row_4
		ld de, LFSRSeed
		call str_at_display
	endif
		call update_display

		; TODO keyboard processing

if BASE_CPM
		call cin_wait
else
		call cin    ; _wait
endif
;		cp 0
		or a
		jp z, .inmain


		; TODO handle macro



		cp KEY_LEFT    ; cursor left
		jp z, input_left
	
		cp KEY_RIGHT      ; cursor right
		jp z, input_right

		cp KEY_CR
		ret z

		cp KEY_BS
		jp z, input_delchar

		cp KEY_NEXTWORD
		jp z, input_nxtword

		cp KEY_PREVWORD
		jp z, input_prvword

		cp KEY_HOME    ; jump to start of line
		jr nz, .ikh
		ld a, 0
		ld (input_cursor), a
		jp z, .inmain
.ikh:

		cp KEY_END     ; jump to end of line
		jr nz, .ike
		ld a, (input_len)
		ld (input_cursor),a
		jp z, .inmain
.ike:
	        cp KEY_UP      ; recall last command
		ret z
;jr nz, .irec
; TODO next word
; TODO prev word
; 
;
;	ld hl, scratch
;	ld de, os_last_cmd
;	call strcpy
;		jp  .inmain
.irec:
;		jr .instr1



		; if any keys not intercepted by above but are special keys like function keys then return them to the program

; TODO return if any special keys are given
;		ld l, a
;		ld a, 28 ; KEY_F12   ; 27
;		sub l
;		ret m
;		ld a, l
		; if no special key then insert as a char



		jp input_inschr

	
input_nxtword:
	; jump to start next word after the cursor

.insknwn:	
		call input_curptr	
		ld a,(hl)	
;		cp 0
		or a
		jp z, .inmain    ; end of string

; if we are on a word, then move off of it

		cp ' '
		jr z, .inspace     ; we are on space so eat the space until we hit non-space
		ld hl, input_cursor
		inc (hl)
		jr .insknwn

.inspace:

		call input_curptr	
		ld a,(hl)	
;		cp 0
		or a
		jp z, .inmain    ; end of string

; if we are on a word, then move off of it

		cp ' '
		jp nz, .inmain     ; we are on non space so at next word
		ld hl, input_cursor
		inc (hl)
		jr .inspace




input_prvword:
	; jump to the start of previous word before the cursor

; where are we to start with currently?

		call input_curptr	
		ld a, (hl)
		cp ' '
		jr z, .inspacep     ; we are on space so eat the space until we hit non-space



.inskpwn:	
		ld a,(input_cursor)
;		cp 0
		or a
		jp z, .inmain    ; start of string

;if we are on a word, then move off of it

		call input_curptr	
		ld a, (hl)
		cp ' '
		jr z, .iwstart     ; we are on space so eat the space until we hit non-space
		;jp z, .inmain    ; start of string
		ld hl, input_cursor
		dec (hl)
		jr .inskpwn
.iwstart:
		ld hl, input_cursor
		inc (hl)
		jp .inmain
		

.inspacep:

		;jp .inmain    ; start of string



		ld a,(input_cursor)
;		cp 0
		or a
		jp z, .inmain    ; start of string

; if we are on a word, then move off of it

		call input_curptr	
		ld a, (hl)
		cp ' '
		jp nz, .incharp     ; we are on non space so at end of prev word
		ld hl, input_cursor
		dec (hl)
		jr .inspacep


.incharp:	
		; eat the word to get to the start
		ld a,(input_cursor)
;		cp 0
		or a
		jp z, .inmain    ; start of string

; if we are on a word, then move off of it

		call input_curptr	
		ld a, (hl)
		cp ' '
		jr z, .ipwordst     ; we are on space so eat the space until we hit non-space
		ld hl, input_cursor
		dec (hl)
		jr .incharp
.ipwordst:
		; at space before the prev word so reposition over it
		ld hl, input_cursor
		inc (hl)
		jr .inskpwn
		


input_left:
	; move cursor left
	ld hl, input_cursor
	dec (hl)
;	cp 0
;	jp z, .inmain    ; ignore left as at the start of the string
	jp .inmain

input_right:
	; move cursor right
	
	;ld a, (input_size)
	;ld b, a
	ld hl, input_cursor
	inc (hl)
	;dec b
	;cp 0
	;jp z, .inmain   ; ignore as at end of the string buffer
	;ld a, b
	;inc a
	;ld (input_cursor), a
	jp .inmain



input_disp_ref:
	; display the text from start of buffer (ie full refresh)
	ld a, (input_at_pos)
	ld hl,(input_start)
	ex de, hl
	call str_at_display 
	ret
input_disp_oncur:
	; display the text from cursor position to end of buffer
	; TODO position start of string at cursor position on screen
	; TODO draw from that point on
	ld a, (input_cursor)
	ld b, a
	ld a, (input_at_pos)
	add b
	ld c, b     ; save a
	ld a, b     ; inc string start for cursor
	ld hl,(input_start)
	call addatohl
	ex de, hl
	ld a, c
	call str_at_display 
	ret

input_nxtw:
	; Find next word
	ret

input_prvw:
	; Find previous word
	ret

input_lenrem:  
	; Calculate the length of string remaining from current cursor
	; position to end of buffer (exc null term)
	
	ld a, (input_cursor)
	ld c, a
	ld a, (input_size)
	sub c
	ld b, 0
	dec c
	ret	

input_curptr:
	; calc address of the character under the cursor
	
	ld hl, (input_start)
	ld a, (input_cursor)
	call addatohl
	ret

input_inschr:
	; Insert char at cursor position
	push af   ; save char
	;call input_lenrem    ; get bc length of remaining string

	
	call input_curptr
;	ld hl, (input_start)
;	ld a, (input_cursor)
;	call addatohl
	;push hl   ; save to come back to

	; shift everything up one to end of buffer

	;push hl
	;dec de
	;inc de
;	ldir
	
	;pop hl

	; are we adding to the end of line?

	ld a, (input_cursor)
	ld b, a
	ld a, (input_len)
	cp b
	jr nz, .insmid   ; no, insert in middle of text

	; tack on the end of the line
	pop af
	ld (hl), a   ; save new char
	inc hl
;	ld a, 0
	ld (hl), 0
	jp input_right
	
.insmid:
	; hl has insertion point so move everything up one to allow for insertion
	;call input_shiftright
	pop af

.shufinsmid:
	ld b, a     ; b contains new char, c prev char at this position 
	ld a, (hl)

;	cp 0    ; at end of string need to then dump new char and add term
	or a
	jr z, .endinsmid
	ld c, a
	ld a, b
	ld (hl), a
	inc hl
	ld a, c
	jr .shufinsmid
	



.endinsmid:
	ld a, b
	ld (hl), a
	inc hl
;	ld a, 0
	ld (hl), 0


;	ld (hl), a   ; save new char

	jp input_right

;input_shiftright:
;	; shift text right at cursor, hl has shift start
;	push hl
;	push de
;	push bc
;
;
;	; move to end of string past zero term
;	ld hl,(input_start)
;	ld a, (input_len)
;	call addatohl
;	inc hl
;;	inc hl
;;	inc hl
;	ld a, 0
;	ld (hl), a
;;	dec hl
;	
;;	ld (hl), a
;;	dec hl
;
;	push hl
;	pop de
;	inc de
;	
;
;;	ld hl,(input_start)
;;	ld a, (input_cursor)
;;	call addatohl
;
;
;	; calc how many bytes from cursor pos to end of string we need to shift
;	call input_lenrem    ; get bc length of remaining string
;	;ld a, (input_cursor)
;	;ld c, a
;	ld a, (input_len)
;	cp 2
;	jr z, .iskipzero	
;	;sub c
;	;inc a
;	;ld c, a
;	;ld b, 0
;	inc c
;	inc c
;	; move data
;	lddr
;.iskipzero:
;
;	pop bc
;	pop de
;	pop hl
;	ret	

input_delchar:
	; Delete char at cursor position
	call input_lenrem    ; get bc length of remaining string
	ld hl, (input_start)
	ld a, (input_cursor)
	call addatohl

	push hl
	pop de
	dec de

.dl:	
	ldi 
	ld a, (hl)
;	cp 0
	or a
	jr z, .dldone
	jr .dl
.dldone:
	ldi

	jp input_left


endif



if EDIT_V1
input_str:

	    	ld (input_at_pos),a      ; save display position to start
		add c
		ld (input_at_cursor),a	; save draw pos of cursor
		ld (input_start), hl     ; save ptr to buffer
		ld a, c
		call addatohl
		ld (input_ptr), hl     ; save ptr to point under the cursor
		ld a,d
	        ld (input_size), a       ; save length of input area
		ld a, c
		ld (input_cursor),a      ; init cursor start position 
		ld a,e
	        ld (input_display_size), a       ; save length of input area that is displayed TODO
		
		

;		ld a,(input_ptr)
;		ld (input_under_cursor),a 	; save what is under the cursor

; TODO move out to cin as cursor shape is used by the 4x4 ???
		; init cursor shape if not set by the cin routines
		ld hl, cursor_shape
if BASE_KEV
		ld a, 255
else
		ld a, '#'
endif
		ld (hl), a
		inc hl
		ld a, 0
		ld (hl), a

		ld a, CUR_BLINK_RATE
		ld (input_cur_flash), a
		ld a, 1
		ld (input_cur_onoff),a

;	if DEBUG_INPUT
;		push af
;		ld a, 'I'
;		ld (debug_mark),a
;		pop af
;		CALLMONITOR
;	endif
.is1:		; main entry loop



		; pause 1ms

		ld a, 1
		call aDelayInMS

		; dec flash counter
		ld a, (input_cur_flash)
		dec a
		ld (input_cur_flash), a
;		cp 0
		or a
		jr nz, .nochgstate


		; change state
		ld a,(input_cur_onoff)
		neg
		ld (input_cur_onoff),a


		; reset on change of state
		ld a, CUR_BLINK_RATE
		ld (input_cur_flash), a

.nochgstate:
		
		

		; display cursor 

;		ld hl, (input_start)
;		ld a, (input_cursor)
;		call addatohl

		; get char under cursor and replace with cursor
ld hl, (input_ptr)
;		ld a, (hl)
;		ld (input_under_cursor),a
;		ld a, '_'
;		ld (hl), a

		; display string

		ld de, (input_start)
		ld a, (input_at_pos)
		call str_at_display
;	        call update_display

		; find place to put the cursor
;		add h
;		ld l, display_row_1
;		sub l
; (input_at_pos)
		;ld c, a
;		ld a, (input_cursor)
;		ld l, (input_at_pos)
;		;ld b, h
;		add l
;		ld (input_at_cursor),a
		;ld l,h

;		ld h, 0
;		ld l,(input_at_pos)
;		ld a, (input_cursor)
;		call addatohl
;		ld a, 074H-19			; TODO BUG I dont know why offset is showing 74H
;		call subafromhl
;		ld a,l
;		ld (input_at_cursor), a

	if DEBUG_INPUT
		ld a, (hardware_diag)
;		cp 0
		or a
		jr z, .skip_input_diag

		ld a,(input_at_pos)
		ld hl, LFSRSeed
		call hexout
		ld a, (input_cursor)
		ld hl, LFSRSeed+2
		call hexout
		ld a,(input_at_cursor)
		ld hl, LFSRSeed+4
		call hexout

		ld a,(input_cur_onoff)
		ld hl, LFSRSeed+6
		call hexout

		ld a,(input_cur_flash)
		ld hl, LFSRSeed+8
		call hexout

		ld a,(input_len)
		ld hl, LFSRSeed+10
		call hexout
		ld hl, LFSRSeed+12
		ld a, 0
		ld (hl),a
		ld a, display_row_4
		ld de, LFSRSeed
		call str_at_display
		.skip_input_diag:
	endif

		; decide on if we are showing the cursor this time round

		ld a, (input_cur_onoff)
		cp 255
		jr z, .skipcur


		ld a,(input_at_cursor)
		ld de, cursor_shape
		call str_at_display

		; save length of current input string
		ld hl, (input_start)
		ld a, 0
		call strlent
		ld a,l
		ld (input_len),a

.skipcur:

	        call update_display
		


		; wait
	
		; TODO loop without wait to flash the cursor and char under cursor	
		call cin    ; _wait

;		cp 0
		or a
		jp z, .is1

		; get ptr to char to input into

		ld c,a
		ld hl, (input_start)
		ld a, (input_cursor)
		call addatohl
		ld (input_ptr), hl
		ld a,c

		; replace char under cursor

;		ld hl, (input_ptr)
;		ld a, (input_under_cursor) 	; get what is under the cursor
;		ld (hl), a

;	if DEBUG_INPUT
;		push af
;		ld a, 'i'
;		ld (debug_mark),a
;		pop af
;		CALLMONITOR
;	endif
		cp KEY_HOME
		jr nz, .iske

		ld a, (input_at_pos)
		ld (input_at_cursor),a
		ld a, 0
		ld (input_cursor), a
		jp .is1
		
.iske:		cp KEY_END
		jr nz, .isknw
		jp .is1

.isknw:		cp KEY_NEXTWORD
		jr nz, .iskpw

.isknwm:	ld hl, (input_ptr)
		ld a,(hl)	
;		cp 0
		or a
		jp z, .is1    ; end of string
		cp ' '
		jp z, .is1    ; end of word
		inc hl
		ld (input_ptr), hl
		ld a, (input_at_cursor)
		inc a
		ld (input_at_cursor), a
		jr .isknwm

.iskpw:		cp KEY_PREVWORD
		jr nz, .iskl
.iskpwm:	
		ld hl, (input_ptr)
		ld a,(hl)	
;		cp 0 
		or a
		jp z, .is1    ; end of string
		cp ' '
		jp z, .is1    ; end of word
		dec hl
		ld (input_ptr), hl
		ld a, (input_at_cursor)
		dec a
		ld (input_at_cursor), a
		jr .iskpwm


.iskl:		cp KEY_LEFT
		jr nz, .isk1

		ld a, (input_cursor)

;		cp 0
		or a
		jp z, .is1 		; at start of line to ignore 

		dec  a 		; TODO check underflow
		ld (input_cursor), a

		ld hl, (input_ptr)
		dec hl
		ld (input_ptr), hl
		
		ld a, (input_at_cursor)
		dec a
		ld (input_at_cursor), a

		ld a, 1		; show cursor moving
		ld (input_cur_onoff),a
		ld a, CUR_BLINK_RATE
		ld (input_cur_flash), a

		jp .is1

.isk1:		cp KEY_RIGHT
		jr nz, .isk2

		ld a,(input_len)		; TODO BUG why cant i load e direct?
		ld e,a
		ld a, (input_cursor)
		cp e
		jp z, .is1		; at the end of string so dont go right

		inc  a 		; TODO check overflow
		ld (input_cursor), a

		ld a, (input_at_cursor)
		inc a
		ld (input_at_cursor), a

		ld hl, (input_ptr)
		inc hl
		ld (input_ptr), hl

		ld a, 1		; show cursor moving
		ld (input_cur_onoff),a
		ld a, CUR_BLINK_RATE
		ld (input_cur_flash), a

		jp .is1

.isk2:		cp KEY_UP

		jr nz, .isk3

		; swap last command with the current on

		; move cursor to start of string
		ld hl, (input_start)
		ld (input_ptr), hl

		ld a, (input_at_pos)
		ld (input_at_cursor), a

		ld a, 0
		ld (input_cursor), a
		
		; swap input and last command buffers

		ld hl, os_cli_cmd
		ld de, os_last_cmd
		ld b, 255
.swap1:		ld a, (hl)
		ld c,a
		ld a, (de)
		ld (hl), a
		ld a,c
		ld (de),a
		inc hl
		inc de
		djnz .swap1





		jp .is1

.isk3:		cp KEY_BS
		jr nz, .isk4

		ld a, (input_cursor)

;		cp 0
		or a
		jp z, .is1 		; at start of line to ignore 

		dec  a 		; TODO check underflow
		ld (input_cursor), a

		; hl is source
		; de needs to be source - 1

;		ld a, 0
;		dec hl
;		ld (hl), a

		ld hl, (input_ptr)
		dec hl
		ld (input_ptr), hl

		; shift all data

		push hl
		inc hl
		pop de
		ld a, (input_len)		; TODO BUG WAS ld c, (input...
		ld c,a
		ld b,0
		ldir 




		ld a, (input_at_cursor)
		dec a
		ld (input_at_cursor), a


		ld a, 1		; show cursor moving
		ld (input_cur_onoff),a
		ld a, CUR_BLINK_RATE
		ld (input_cur_flash), a

		; remove char
		ld a, (input_at_cursor)
		inc a
		ld de,.iblank
		call str_at_display

		jp .is1

.isk4:		cp KEY_CR
		jr z, .endinput

		; else add the key press to the end

		ld c, a			; save key pressed

		ld a,(hl)		; get what is currently under char

;		cp 0			; we are at the end of the string
		or a
		jr nz, .onchar
		
		; add a char to the end of the string
	
		ld (hl),c
		inc hl
;		ld a,' '
;		ld (hl),a
;		inc hl
		ld a,0
		ld (hl),a
		dec hl

		ld a, (input_cursor)
		inc a				; TODO check max string length and scroll 
		ld (input_cursor), a		; inc cursor pos
				
		ld a, (input_at_cursor)
		inc a
		ld (input_at_cursor), a

		ld hl, (input_ptr)
		inc hl
		ld (input_ptr), hl

		ld hl, (input_ptr)
		inc hl
		ld (input_ptr), hl
;	if DEBUG_INPUT
;		push af
;		ld a, '+'
;		ld (debug_mark),a
;		pop af
;		CALLMONITOR
;	endif
		ld a, 1		; show cursor moving
		ld (input_cur_onoff),a
		ld a, CUR_BLINK_RATE
		ld (input_cur_flash), a
		jp .is1
		


		; if on a char then insert
.onchar:

		; TODO over flow check: make sure insert does not blow out buffer

		; need to do some maths to use lddr

		push hl   ; save char pos
		push bc

		ld hl, (input_start)
		ld a, (input_len)
		call addatohl  		; end of string
		inc hl
		inc hl		; past zero term
		push hl
		inc hl
		push hl 

					; start and end of lddr set, now how much to move?

				
		ld a, (input_cursor)		; BUG TODO why cant i load directly into b???
		ld b,a
		ld a,(input_len)
		ld e,a
		sub b
		inc a		;??
		inc a		;??
		inc a		;??

		ld b,0
		ld c,a

	if DEBUG_INPUT
		push af
		ld a, 'i'
		ld (debug_mark),a
		pop af
;		CALLMONITOR
	endif
		pop de
		pop hl
	if DEBUG_INPUT
		push af
		ld a, 'I'
		ld (debug_mark),a
		pop af
;		CALLMONITOR
	endif
		lddr
	


		; TODO have a key for insert/overwrite mode????
		pop bc
		pop hl
		ld (hl), c		; otherwise overwrite current char
		



		ld a, (input_cursor)
		inc  a 		; TODO check overflow
		ld (input_cursor), a

		ld a, (input_at_cursor)
		inc a
		ld (input_at_cursor), a

		jp .is1

.endinput:	; TODO look for end of string

		; add trailing space for end of token

		ld hl, (input_start)
		ld a,(input_len)
		call addatohl
		ld a, ' '
		ld (hl),a
		; TODO eof of parse marker

		inc hl
		ld a, 0
		ld (hl),a


		ret

.iblank: db " ",0


input_str_prev:	ld (input_at_pos), a
		ld (input_start), hl
		ld a,1			; add cursor
		ld (hl),a
		inc hl
		ld a,0
		ld (hl),a
		ld (input_ptr), hl
		ld a,d
		ld (input_size), a
		ld a,0
		ld (input_cursor),a
.instr1:	

		; TODO do block cursor
		; TODO switch cursor depending on the modifer key

		; update cursor shape change on key hold

		ld hl, (input_ptr)
		dec hl
		ld a,(cursor_shape)
		ld (hl), a

		; display entered text
		ld a,(input_at_pos)
            	CALL fLCD_Pos       ;Position cursor to location in A
            	LD   de, (input_start)
            	CALL fLCD_Str       ;Display string pointed to by DE

		call cin
;		cp 0
		or a
		jr z, .instr1

		; proecess keyboard controls first

		ld hl,(input_ptr)

		cp KEY_CR	 ; pressing enter ends input
		jr z, .instrcr

		cp KEY_BS 	; back space
		jr nz, .instr2
		; process back space

		; TODO stop back space if at start of string
		dec hl
		dec hl ; to over write cursor
		ld a,(cursor_shape)
		;ld a,0
		ld (hl),a
		inc hl
		ld a," "
		ld (hl),a
		ld (input_ptr),hl
		

		jr .instr1

.instr2:	cp KEY_LEFT    ; cursor left
		jr nz, .instr3
		dec hl
		ld (input_ptr),hl
		jr .instr1
	
.instr3:	cp KEY_RIGHT      ; cursor right
		jr nz, .instr4
		inc hl
		ld (input_ptr),hl
		jr .instr1

.instr4:	cp KEY_HOME    ; jump to start of line
		jr nz, .instr5
		dec hl
		ld (input_ptr),hl
		jr .instr1

.instr5:	cp KEY_END     ; jump to end of line
		jr nz, .instr6
		dec hl
		ld (input_ptr),hl
		jr .instr1
.instr6:        cp KEY_UP      ; recall last command
		jr nz, .instrnew

	ld hl, scratch
	ld de, os_last_cmd
	call strcpy
		jr .instr1


.instrnew:	; no special key pressed to see if we have room to store it

		; TODO do string size test

		dec hl ; to over write cursor
		ld (hl),a
		inc hl
		ld a,(cursor_shape)
		ld (hl),a
		inc hl
		ld a,0
		ld (hl),a

		ld (input_ptr),hl
		
		jr .instr1
.instrcr:	dec hl		; remove cursor
		ld a,' '	; TODO add a trailing space for safety
		ld (hl),a
		inc hl
		ld a,0
		ld (hl),a


		; if at end of line scroll up   
		; TODO detecting only end of line 4 for scroll up 

		;ld  

		ret


endif
; strcpy hl = dest, de source

strcpy:   LD   A, (DE)        ;Get character from string
            OR   A              ;Null terminator?
            RET  Z              ;Yes, so finished
		ld a,(de)
		ld (hl),a
            INC  DE             ;Point to next character
		inc hl
            JR   strcpy       ;Repeat
		ret


; TODO string_at 
; pass string which starts with lcd offset address and then null term string

; TODO string to dec
; TODO string to hex
; TODO byte to string hex
; TODO byte to string dec



; from z80uartmonitor
;;;;;;;;;;;;;;;;;;;;;;;;;;;;;;;;;;;;;;;;;;;;;;;;;	
; OUTPUT VALUE OF A IN HEX ONE NYBBLE AT A TIME
; pass hl for where to put the text
;;;;;;;;;;;;;;;;;;;;;;;;;;;;;;;;;;;;;;;;;;;;;;;;;	
hexout:	PUSH BC
		PUSH AF
		LD B, A
		; Upper nybble
		SRL A
		SRL A
		SRL A
		SRL A
		CALL tohex
		ld (hl),a
		inc hl	
		
		; Lower nybble
		LD A, B
		AND 0FH
		CALL tohex
		ld (hl),a
		inc hl	
		
		POP AF
		POP BC
		RET
		
;;;;;;;;;;;;;;;;;;;;;;;;;;;;;;;;;;;;;;;;;;;;;;;;;	
; TRANSLATE value in lower A TO 2 HEX CHAR CODES FOR DISPLAY
;;;;;;;;;;;;;;;;;;;;;;;;;;;;;;;;;;;;;;;;;;;;;;;;;	
tohex:
		PUSH HL
		PUSH DE
		LD D, 0
		LD E, A
		LD HL, .DATA
		ADD HL, DE
		LD A, (HL)
		POP DE
		POP HL
		RET

.DATA:
		DEFB	30h	; 0
		DEFB	31h	; 1
		DEFB	32h	; 2
		DEFB	33h	; 3
		DEFB	34h	; 4
		DEFB	35h	; 5
		DEFB	36h	; 6
		DEFB	37h	; 7
		DEFB	38h	; 8
		DEFB	39h	; 9
		DEFB	41h	; A
		DEFB	42h	; B
		DEFB	43h	; C
		DEFB	44h	; D
		DEFB	45h	; E
		DEFB	46h	; F
;;;;;;;;;;;;;;;;;;;;;;;;;;;;;;;;;;;;;;;;;;;;;;;;;;;;;;;;;;;;;;
;; 	ASCII char code for 0-9,A-F in A to single hex digit
;;    subtract $30, if result > 9 then subtract $7 more
;;;;;;;;;;;;;;;;;;;;;;;;;;;;;;;;;;;;;;;;;;;;;;;;;;;;;;;;;;;;;;
atohex:
		SUB $30
		CP 10
		RET M		; If result negative it was 0-9 so we're done
		SUB $7		; otherwise, subtract $7 more to get to $0A-$0F
		RET		




; Get 2 ASCII characters as hex byte from pointer in hl

BYTERD:
	LD	D,00h		;Set up
	CALL	HEXCON		;Get byte and convert to hex
	ADD	A,A		;First nibble so
	ADD	A,A		;multiply by 16
	ADD	A,A		;
	ADD	A,A		;
	LD	D,A		;Save hi nibble in D
HEXCON:
	ld a, (hl)		;Get next chr
	inc hl
	SUB	030h		;Makes '0'-'9' equal 0-9
	CP	00Ah		;Is it 0-9 ?
	JR	C,NALPHA	;If so miss next bit
	SUB	007h		;Else convert alpha
NALPHA:
	OR	D		;Add hi nibble back
	RET			;


;
; Get a word (16 bit) in hexadecimal notation. The result is returned in HL.
; Since the routines get_byte and therefore get_nibble are called, only valid
; characters (0-9a-f) are accepted.
;
;get_word        push    af
;                call    get_byte        ; Get the upper byte
;                ld      h, a
;                call    get_byte        ; Get the lower byte
;                ld      l, a
;                pop     af
;                ret
;
; Get a byte in hexadecimal notation. The result is returned in A. Since
; the routine get_nibble is used only valid characters are accepted - the 
; input routine only accepts characters 0-9a-f.
;
get_byte:        push    bc              ; Save contents of B (and C)
		ld a,(hl)
		inc hl
                call    nibble2val      ; Get upper nibble
                rlc     a
                rlc     a
                rlc     a
                rlc     a
                ld      b, a            ; Save upper four bits
		ld a,(hl)
                call    nibble2val      ; Get lower nibble
                or      b               ; Combine both nibbles
                pop     bc              ; Restore B (and C)
                ret
;
; Get a hexadecimal digit from the serial line. This routine blocks until
; a valid character (0-9a-f) has been entered. A valid digit will be echoed
; to the serial line interface. The lower 4 bits of A contain the value of 
; that particular digit.
;
;get_nibble      ld a,(hl)           ; Read a character
;                call    to_upper        ; Convert to upper case
;                call    is_hex          ; Was it a hex digit?
;                jr      nc, get_nibble  ; No, get another character
 ;               call    nibble2val      ; Convert nibble to value
 ;               call    print_nibble
 ;               ret
;
; is_hex checks a character stored in A for being a valid hexadecimal digit.
; A valid hexadecimal digit is denoted by a set C flag.
;
;is_hex          cp      'F' + 1         ; Greater than 'F'?
;                ret     nc              ; Yes
;                cp      '0'             ; Less than '0'?
;                jr      nc, is_hex_1    ; No, continue
;                ccf                     ; Complement carry (i.e. clear it)
;                ret
;is_hex_1        cp      '9' + 1         ; Less or equal '9*?
;                ret     c               ; Yes
;                cp      'A'             ; Less than 'A'?
;                jr      nc, is_hex_2    ; No, continue
;                ccf                     ; Yes - clear carry and return
;                ret
;is_hex_2        scf                     ; Set carry
;                ret
;
; Convert a single character contained in A to upper case:
;
to_upper:        cp      'a'             ; Nothing to do if not lower case
                ret     c
                cp      'z' + 1         ; > 'z'?
                ret     nc              ; Nothing to do, either
                and     $5f             ; Convert to upper case
                ret


to_lower:

   ; if char is in [A-Z] make it lower case

   ; enter : a = char
   ; exit  : a = lower case char
   ; uses  : af

   cp 'A'
   ret c
   
   cp 'Z'+1
   ret nc
   
   or $20
   ret

;
; Expects a hexadecimal digit (upper case!) in A and returns the
; corresponding value in A.
;
nibble2val:      cp      '9' + 1         ; Is it a digit (less or equal '9')?
                jr      c, nibble2val_1 ; Yes
                sub     7               ; Adjust for A-F
nibble2val_1:    sub     '0'             ; Fold back to 0..15
                and     $f              ; Only return lower 4 bits
                ret
;
; Print_nibble prints a single hex nibble which is contained in the lower 
; four bits of A:
;
;print_nibble    push    af              ; We won't destroy the contents of A
;                and     $f              ; Just in case...
;                add     a, '0'             ; If we have a digit we are done here.
;                cp      '9' + 1         ; Is the result > 9?
;                jr      c, print_nibble_1
;                add     a, 'A' - '0' - $a  ; Take care of A-F
;print_nibble_1  call    putc            ; Print the nibble and
;                pop     af              ; restore the original value of A
;                ret
;;
;; Send a CR/LF pair:
;
;crlf            push    af
;                ld      a, cr
;                call    putc
;                ld      a, lf
;                call    putc
;                pop     af
;                ret
;
; Print_word prints the four hex digits of a word to the serial line. The 
; word is expected to be in HL.
;
;print_word      push    hl
;                push    af
;                ld      a, h
;                call    print_byte
;                ld      a, l
;                call    print_byte
;                pop     af
;                pop     hl
;                ret
;
; Print_byte prints a single byte in hexadecimal notation to the serial line.
; The byte to be printed is expected to be in A.
;
;print_byte      push    af              ; Save the contents of the registers
;                push    bc
;                ld      b, a
;                rrca
;                rrca
;                rrca
;                rrca
;                call    print_nibble    ; Print high nibble
;                ld      a, b
;                call    print_nibble    ; Print low nibble
;                pop     bc              ; Restore original register contents
;                pop     af
;                ret





fourehexhl: 
	ld a,(hl)
	call atohex
		SRL A
		SRL A
		SRL A
		SRL A
	ld b, a
	inc hl
	ld a,(hl)
	inc hl
	call atohex
	add b
	ld d,a
	ld a,(hl)
	call atohex
		SRL A
		SRL A
		SRL A
		SRL A
	ld b, a
	inc hl
	ld a,(hl)
	inc hl
	call atohex
	add b
	ld e, a
	push de
	pop hl
	ret

; pass hl. returns z set if the byte at hl is a digit
;isdigithl: 
;	push bc
;	ld a,(hl)
;	cp ':'
;	jr nc, .isdf 		; >
;	cp '0'
;	jr c, .isdf		; <
;
;	; TODO find a better way to set z
;
;	ld b,a
;	cp b
;	pop bc
;	ret
;
;.isdf:	; not digit so clear z
;
;	; TODO find a better way to unset z
;
;	ld b,a
;	inc b
;	cp b
;
;	pop bc
;	ret
	
	


; pass hl as the four byte address to load

get_word_hl: 
	push hl
	call get_byte
	
	ld b, a

	pop hl
	inc hl
	inc hl

; TODO not able to handle a-f 
	ld a,(hl)
;	;cp ':'
;	cp 'g'
;	jr nc, .single_byte_hl 		; >
;	cp 'G'
;	jr nc, .single_byte_hl 		; >
;	cp '0'
;	jr c, .single_byte_hl		; <

	;call isdigithl
;	cp 0
	or a
	jr z, .single_byte_hl

.getwhln:   ; hex word so get next byte

	call get_byte
	ld l, a
	ld h,b
	ret
.single_byte_hl:   ld l,b
		ld h,0
		ret




	ld hl,asc+1
;	ld a, (hl)
;	call nibble2val
	call get_byte

;	call fourehexhl
	ld (scratch+52),a
	
	ld hl,scratch+50
	ld (os_cur_ptr),hl

	ret


; from https://wikiti.brandonw.net/index.php?title=Z80_Routines:Other:DispA

; Decimal Unsigned Version

;Number in a to decimal ASCII
;adapted from 16 bit found in z80 Bits to 8 bit by Galandros
;Example: display a=56 as "056"
;input: a = number
;Output: a=0,value of a in the screen
;destroys af,bc (don't know about hl and de)
DispAToASCII:
	ld	c,-100
	call	.Na1
	ld	c,-10
	call	.Na1
	ld	c,-1
.Na1:	ld	b,'0'-1
.Na2:	inc	b
	add	a,c
	jr	c,.Na2
	sub	c		;works as add 100/10/1
	push af		;safer than ld c,a
	ld	a,b		;char is in b
;TODO	CALL	PUTCHAR	;plot a char. Replace with bcall(_PutC) or similar.
	pop af		;safer than ld a,c
	ret

; Decimal Signed Version

; DispA
; --------------------------------------------------------------
; Converts a signed integer value to a zero-terminated ASCII
; string representative of that value (using radix 10).
; --------------------------------------------------------------
; INPUTS:
;     HL     Value to convert (two's complement integer).
;     DE     Base address of string destination. (pointer).
; --------------------------------------------------------------
; OUTPUTS:
;     None
; --------------------------------------------------------------
; REGISTERS/MEMORY DESTROYED
; AF HL
; --------------------------------------------------------------

;DispHLToASCII:
;   push    de
;   push    bc
;
;; Detect sign of HL.
;    bit    7, h
;    jr     z, ._DoConvert
;
;; HL is negative. Output '-' to string and negate HL.
;    ld     a, '-'
;    ld     (de), a
;    inc    de
;
;; Negate HL (using two's complement)
;    xor    a
;    sub    l
;    ld     l, a
;    ld     a, 0     ; Note that XOR A or SUB A would disturb CF
;    sbc    a, h
;    ld     h, a
;
;; Convert HL to digit characters
;._DoConvert:
;    ld     b, 0     ; B will count character length of number
;-   ld     a, 10
;    syscall  .DivHLByA  ; HL = HL / A, A = remainder
;    push   af
;    inc    b
;    ld     a, h
;    or     l
;    jr     nz, -
;
;; Retrieve digits from stack
;-   pop    af
;    or     $30
;    ld     (de), a
;    inc    de
;    djnz   -
;
;; Terminate string with NULL
;    xor    a
;    ld     (de), a
;
;    pop    bc
;    pop    de
;    ret

;Comments
;
;    This routine uses the common positive-integer radix conversion algorithm of repeatedly dividing a value by the desired radix (base case: the value is zero) and saving the remainders of each division.
;    As this algorithm gives the digits in reverse order, they are pushed onto the hardware stack so that subsequently popping them yields the correct order.
;    Note that the output string will not be fixed-width.
;
;Example Usage
;
;    ld    hl, -1004
;    ld    de, OP1
;    call  DispA
;    ld    hl, OP1
;    syscall  PutS


; from https://github.com/Zeda/Z80-Optimized-Routines/blob/master/conversion/string_to_uint16.z80


;Converts an ASCII string to an unsigned 16-bit integer
;Quits when it reaches a non-decimal digit

string_to_uint16:
atoui_16:
;Input:
;     DE points to the string
;Outputs:
;     HL is the result
;     A is the 8-bit value of the number
;     DE points to the byte after the number
;Destroys:
;     BC
;       if the string is non-empty, BC is HL/10
;Size:  24 bytes
;Speed: 42+d(104+{0,9})
;       d is the number of digits in the number
;       max is 640 cycles for a 5 digit number
;Assuming no leading zeros:
;1 digit:  146cc
;2 digit:  250cc
;3 digit:  354cc or 363cc (avg: 354.126cc)
;4 digit:  458cc or 467cc (avg: 458.27cc)
;5 digit:  562cc or 571cc or 580cc (avg: 562.4104cc)
;avg: 544.81158447265625cc (544+13297/16384)
;===============================================================
  ld hl,0
.u16a:
  ld a,(de)
  sub 30h
  cp 10
  ret nc
  inc de
  ld b,h
  ld c,l
  add hl,hl
  add hl,hl
  add hl,bc
  add hl,hl
  add a,l
  ld l,a
  jr nc,.u16a
  inc h
  jp .u16a


; from https://github.com/Zeda/Z80-Optimized-Routines/blob/master/conversion/string_to_uint16.z80

;written by Zeda
;Converts a 16-bit unsigned integer to an ASCII string.

uitoa_16:
;Input:
;   DE is the number to convert
;   HL points to where to write the ASCII string (up to 6 bytes needed).
;Output:
;   HL points to the null-terminated ASCII string
;      NOTE: This isn't necessarily the same as the input HL.
  push de
  push bc
  push af
  ex de,hl

  ld bc,-10000
  ld a,'0'-1
  inc a
  add hl,bc 
   jr c,$-2
  ld (de),a
  inc de

  ld bc,1000
  ld a,'9'+1
  dec a 
  add hl,bc 
   jr nc,$-2
  ld (de),a
  inc de

  ld bc,-100
  ld a,'0'-1
  inc a 
  add hl,bc 
   jr c,$-2
  ld (de),a
  inc de

  ld a,l
  ld h,'9'+1
  dec h 
  add a,10 
   jr nc,$-3
  add a,'0'
  ex de,hl
  ld (hl),d
  inc hl
  ld (hl),a
  inc hl
  ld (hl),0

;Now strip the leading zeros
  ld c,-6
  add hl,bc
  ld a,'0'
  inc hl 
  cp (hl) 
  jr z,$-2

;Make sure that the string is non-empty!
  ld a,(hl)
  or a
  jr nz,.atoub
  dec hl
.atoub:

  pop af
  pop bc
  pop de
  ret

; from https://github.com/Zeda/Z80-Optimized-Routines/blob/master/conversion/toUpper.z80

toUpper:
;A is the char.
;If A is a lowercase letter, this sets it to the matching uppercase
;18cc or 30cc or 41cc
;avg: 26.75cc
  cp 'a'
  ret c
  cp 'z'+1
  ret nc
  sub 'a'-'A'
  ret

; https://tutorials.eeems.ca/ASMin28Days/lesson/day16.html#cmp

; String Length
;With a length-prefixed string, finding the length is trivial. For a null-terminated string, the process is decidedly more involved. This is where CPIR comes in.

; Get the length of the null-terminated string starting at $8000 hl
;    LD     HL, $8000

strlenz:

    XOR    A               ; Zero is the value we are looking for.
    LD     B, A             ; Since we haven't the slightest clue as to the 
    LD     C, A             ; actual size of the string, put 0 in BC to search
                           ; 65, 536 bytes (the entire addressable memory space).
    CPIR                   ; Begin search for a byte equalling zero.

; BC has been decremented so that it holds -length. Now need to synthesize a NEG BC.
    LD     H, A             ; Zero HL (basically set it to 65, 536) to get the
    LD     L, A             ; number of bytes
    SBC    HL, BC           ; Find the size. CPIR doesn't affect carry.
    DEC    HL              ; Compensate for null.
	ret

; Get the length of the A terminated string starting at $8000 hl
;    LD     HL, $8000

strlent:

                  ; A is the value we are looking for.
    LD     B, 0             ; Since we haven't the slightest clue as to the 
    LD     C, 0             ; actual size of the string, put 0 in BC to search
                           ; 65, 536 bytes (the entire addressable memory space).
    CPIR                   ; Begin search for a byte equalling zero.

; BC has been decremented so that it holds -length. Now need to synthesize a NEG BC.
    LD     H, 0             ; Zero HL (basically set it to 65, 536) to get the
    LD     L, 0             ; number of bytes
    SBC    HL, BC           ; Find the size. CPIR doesn't affect carry.
    DEC    HL              ; Compensate for null.
	ret


;Comparing Strings

;IN    HL     Address of string1.
;      DE     Address of string2.

; doc given but wrong???
;OUT   zero   Set if string1 = string2, reset if string1 != string2.
;      carry  Set if string1 > string2, reset if string1 <= string2.
; tested
;OUT   carry set  if string1 = string2, carry  reset if string1 != string2.

strcmp_old:
    PUSH   HL
    PUSH   DE

    LD     A, (DE)          ; Compare lengths to determine smaller string
    CP     (HL)            ; (want to minimize work).
    JR     C, Str1IsBigger
    LD     A, (HL)

Str1IsBigger:
    LD     C, A             ; Put length in BC
    LD     B, 0
    INC    DE              ; Increment pointers to meat of string.
    INC    HL

CmpLoop:
    LD     A, (DE)          ; Compare bytes.
    CPI
    JR     NZ, NoMatch      ; If (HL) != (DE), abort.
    INC    DE              ; Update pointer.
    JP     PE, CmpLoop

    POP    DE
    POP    HL
    LD     A, (DE)          ; Check string lengths to see if really equal.
    CP     (HL)
    RET

NoMatch:
    DEC    HL
    CP     (HL)            ; Compare again to affect carry.
    POP    DE
    POP    HL
    RET

;; test strmp
;
;ld de, .str1
;ld hl, .str2
;call strcmp
;jr z, .z1
;;this
;	if DEBUG_FORTH_WORDS
;		DMARK "NZ1"
;		CALLMONITOR
;	endif
;.z1:
;
;	if DEBUG_FORTH_WORDS
;		DMARK "ZZ1"
;		CALLMONITOR
;	endif
;
;ld de, .str1
;ld hl, .str1
;call strcmp
;jr z, .z2
;;this
;	if DEBUG_FORTH_WORDS
;		DMARK "NZ2"
;		CALLMONITOR
;	endif
;.z2:
;
;	if DEBUG_FORTH_WORDS
;		DMARK "ZZ2"
;		CALLMONITOR
;	endif
;
;ld de, .str1
;ld hl, .str2
;call strcmp
;jr c, .c1
;
;	if DEBUG_FORTH_WORDS
;		DMARK "Nc1"
;		CALLMONITOR
;	endif
;.c1:
;;this
;	if DEBUG_FORTH_WORDS
;		DMARK "cc1"
;		CALLMONITOR
;	endif
;
;ld de, .str1
;ld hl, .str1
;call strcmp
;jr c, .c2
;;this
;	if DEBUG_FORTH_WORDS
;		DMARK "Nc2"
;		CALLMONITOR
;	endif
;.c2:
;
;	if DEBUG_FORTH_WORDS
;		DMARK "cc2"
;		CALLMONITOR
;	endif
;	NEXTW
;.str1:   db "string1",0
;.str2:   db "string2",0

; only care about direct match or not
; hl and de strings
; zero set if the same

strcmp:
	ld a, (de)
	cp (hl)
	jr z, .ssame
	or a
	ret

.ssame: 
;	cp 0
	or a
	ret z

	inc hl
	inc de
	jr strcmp
	
	

;Copyright (c) 2014, Luke Maurits
;All rights reserved.
;
;Redistribution and use in source and binary forms, with or without
;modification, are permitted provided that the following conditions are met:
;
;* Redistributions of source code must retain the above copyright notice, this
;  list of conditions and the following disclaimer.
;
;* Redistributions in binary form must reproduce the above copyright notice,
;  this list of conditions and the following disclaimer in the documentation
;  and/or other materials provided with the distribution.
;
;THIS SOFTWARE IS PROVIDED BY THE COPYRIGHT HOLDERS AND CONTRIBUTORS "AS IS"
;AND ANY EXPRESS OR IMPLIED WARRANTIES, INCLUDING, BUT NOT LIMITED TO, THE
;IMPLIED WARRANTIES OF MERCHANTABILITY AND FITNESS FOR A PARTICULAR PURPOSE ARE
;DISCLAIMED. IN NO EVENT SHALL THE COPYRIGHT HOLDER OR CONTRIBUTORS BE LIABLE
;FOR ANY DIRECT, INDIRECT, INCIDENTAL, SPECIAL, EXEMPLARY, OR CONSEQUENTIAL
;DAMAGES (INCLUDING, BUT NOT LIMITED TO, PROCUREMENT OF SUBSTITUTE GOODS OR
;SERVICES; LOSS OF USE, DATA, OR PROFITS; OR BUSINESS INTERRUPTION) HOWEVER
;CAUSED AND ON ANY THEORY OF LIABILITY, WHETHER IN CONTRACT, STRICT LIABILITY,
;OR TORT (INCLUDING NEGLIGENCE OR OTHERWISE) ARISING IN ANY WAY OUT OF THE USE
;OF THIS SOFTWARE, EVEN IF ADVISED OF THE POSSIBILITY OF SUCH DAMAGE.

; https://github.com/lmaurits/lm512/blob/master/string.z80

StrictStrCmp:
	; Load next chars of each string
	ld a, (de)
	ld b, a
	ld a, (hl)
	; Compare
	cp b
	; Return non-zero if chars don't match
	ret nz
	; Check for end of both strings
	cp "\0"
	; Return if strings have ended
	ret z
	; Otherwise, advance to next chars
	inc hl
	inc de
	jr StrictStrCmp

;end
; eof
