kgroveshok/z80-homebrew/images/20220323_082905.jpg

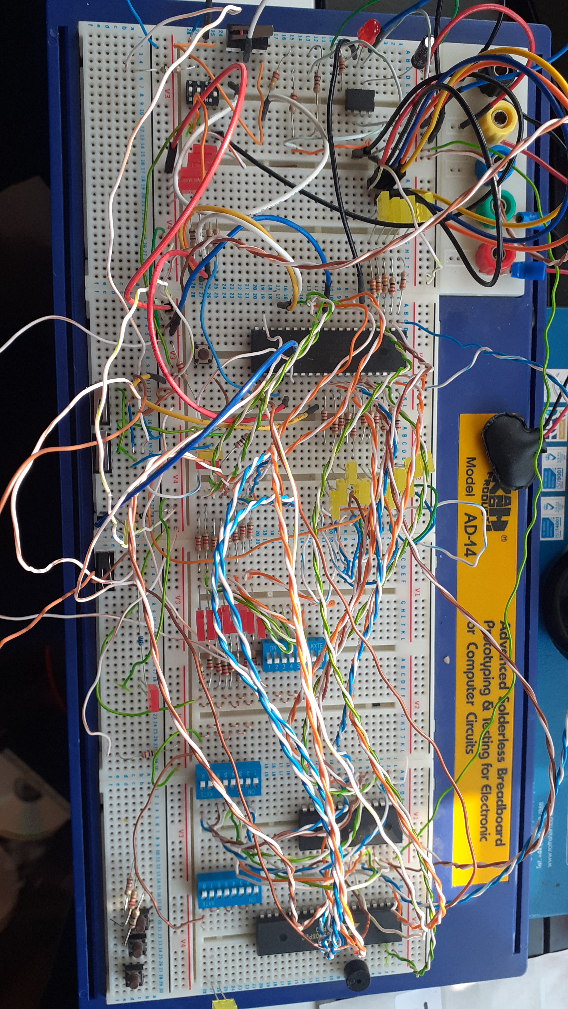
images/20220323_082905.jpg
